mfkiwl/SDR-R/hw/SDRR/Draft1.asc

C1: cap; 20p
Q1: npn; 2N3904
R1: res; 100k
R2: res; 500
V1: voltage; PULSE(0 5 1u 1n 1n 1u 2u 10)
V2: voltage; 5
Named nets: 0
.tran 0 10u 0 10p
