mfkiwl/SDR-R/fpga-src/sources_1/imports/SDR-R/fpga-src/USB_Block/vhdl/ft245_sync_if.vhd

-----------------------------------------------------------------------------
-- file			: ft245_sync_if.vhd
--
-- brief		: Interface for FTDI ft2232h in ft245 synchronous mode
-- author(s)	: marc at pignat dot org
-----------------------------------------------------------------------------
-- Copyright 2015-2019 Marc Pignat
--
-- Licensed under the Apache License, Version 2.0 (the "License");
-- you may not use this file except in compliance with the License.
-- You may obtain a copy of the License at
--
-- 		http://www.apache.org/licenses/LICENSE-2.0
--
-- Unless required by applicable law or agreed to in writing, software
-- distributed under the License is distributed on an "AS IS" BASIS,
-- See the License for the specific language governing permissions and
-- limitations under the License.
-----------------------------------------------------------------------------
--
-- FIXME	: loose bytes when using ftdi_set_latency_timer(ftdi, 1), so
--			  use ftdi_set_latency_timer(ftdi, 2).
--
-----------------------------------------------------------------------------
--
-- Usage
--
-- * This block MUST be clocked by the FTDI chip
--
-- * FTDI Signals MUST be connected directly and tied into the IO pads.
--   * For Xilinx FPGA, nothing has to be done since the "iob" attribute is set.
--
-- * Host code at https://github.com/RandomReaper/ft2tcp
-----------------------------------------------------------------------------
--
-- * FPGA -> FTDI
--   Sending data to the FTDI chip is done using in_* signals.
--   Example: Sending 2 bytes:
--             ____     ____        ____     ____     ____     ____
--   clock ___/    \___/    \/\/\/\/    \___/    \___/    \___/    \____
--
--                ____t1                           t4__________________
--   in_empty (in)    \____________________________/
--
--                                t2________________
--   in_read (out)  _______________|                \__________________
--
--                                        t3
--   in_data (in)  -------------------------< D0    >< D1    >---------
--
--   At t1, in_empty is set to '0'.
--
--   At t2, (after an unknown number of clock cycles) the ft245_sync_if is
--          ready for sendind data and set in_read to '1'.
--
--   At t3, (one clock after in_read) The data (D0) is on in_data.
--
--   At t4, in_data contains the last data, in_empty is set '0'. The
--          ft245_sync_if sets in_read to '0' at the same time.
--
--   Note : This burst can be interrupted (in_read will go to '0', when the
--          FTDI chip FIFO is full.
--
-----------------------------------------------------------------------------
--
-- * FTDI -> FPGA
--   Receiving data from the FTDI chip is done using out_* signals.
--   Example: Receiving 2 bytes:
--             ____     ____        ____     ____     ____     ____
--   clock ___/    \___/    \/\/\/\/    \___/    \___/    \___/    \____
--
--                ____t1                            __________________
--   out_full (in)    \____________________________/___________________
--
--                                t2________________t4
--   out_valid (out)  _____________|                \__________________
--
--                                          t3
--   out_data (out)  --------------< D0    >< D1    >---------
--
--   At t1, the out_full is set to '0'.
--
--   At t2, (after an unknown number of clock cycles) and when the FTDI chip has
--          received data the ft245_sync_if set out_valid to '1' and set data
--          on data out.
--
--   At t3, There is a new data on every clock on out_data
--
--   At t4, out_valid goes '0' (no more data).
--
--   Note : Data receive can be interrupted at any time by setting out_full to
--          '1' at any time.
--
-----------------------------------------------------------------------------

library ieee;
	use ieee.std_logic_1164.all;
	use ieee.numeric_std.all;

entity ft245_sync_if is
port
(
	-----------------------------------------------------
	-- Interface to the ftdi chip
	-----------------------------------------------------
	adbus			: inout	std_logic_vector(7 downto 0);
	rxf_n			: in	std_ulogic;
	txe_n			: in	std_ulogic;
	rd_n			: out	std_ulogic := '1';
	wr_n			: out	std_ulogic := '1';
	clock			: in	std_ulogic;
	oe_n			: out	std_ulogic := '1';
	siwu			: out	std_ulogic;
	reset_n			: out	std_ulogic;
	suspend_n		: in	std_ulogic;

	-----------------------------------------------------
	-- Interface to the internal logic
	-----------------------------------------------------
	reset			: in	std_ulogic;

	-- FPGA -> FTDI
	in_data			: in	std_ulogic_vector(7 downto 0);
	in_empty		: in	std_ulogic;
	in_read			: out	std_ulogic;

	-- FTDI -> FPGA
	out_data		: out	std_ulogic_vector(7 downto 0);
	out_valid		: out	std_ulogic;
	out_full		: in	std_ulogic
	
	--debug
	--debug_out          : out std_logic_vector( 10 downto 0)
);

	-- Force signals into IO pads
	-- Warning XST specific syntax
	attribute iob				: string;
	attribute iob of rxf_n		: signal is "TRUE";
	attribute iob of txe_n		: signal is "TRUE";
	attribute iob of rd_n		: signal is "TRUE";
	attribute iob of wr_n		: signal is "TRUE";
	attribute iob of oe_n		: signal is "TRUE";
	attribute iob of siwu		: signal is "TRUE";
	attribute iob of reset_n	: signal is "TRUE";
	attribute iob of suspend_n	: signal is "TRUE";

end ft245_sync_if;

architecture rtl of ft245_sync_if is

	type state_e is
	(
		STATE_RESET,
		STATE_IDLE,
		STATE_WAIT_READ1,
		STATE_WAIT_READ2,
		STATE_READ,
		STATE_READ_OLD,
		STATE_AFTER_READ1,
		STATE_AFTER_READ2,
		STATE_WRITE,
		STATE_WRITE_OLD
	);

	-- State
	signal state			: state_e := STATE_RESET;
	signal next_state		: state_e;

	-- Positive versions of ft245 control signals
	signal ft_oe			: std_ulogic;
	signal ft_write			: std_ulogic;
	signal ft_read			: std_ulogic;
	signal ft_suspend		: std_ulogic := '0';
	signal ft_tx			: std_ulogic := '0';
	signal ft_rx			: std_ulogic := '0';
    
    --debug signals
    signal bug0, bug1, bug2, bug3, bug4, bug5, bug6, bug7, bug8, bug9 : std_logic;

	-- Store missed read/write
	type failed_element_t is
	record
		data	: std_ulogic_vector(in_data'range);
		valid	: std_ulogic;
	end record;

	type failed_t is array(integer range <>) of failed_element_t;

	-- Data RX
	signal out_data_old		: failed_t(1 downto 0) :=
		(others => (data => (others => '-'), valid => '0'));
	signal read_failed		: std_ulogic;
	signal oe				: std_ulogic;
	signal adbus_int		: std_ulogic_vector(in_data'range);
	signal ft_read_old		: std_ulogic_vector(1 downto 0) := (others => '0');
	signal out_data_int		: std_ulogic_vector(in_data'range) := (others => '0');
	signal out_valid_int	: std_ulogic;

	-- Data TX
	signal in_data_old		: failed_t(2 downto 0) :=
		(others => (data => (others => '-'), valid => '0'));
	signal ft_write_old		: std_ulogic_vector(1 downto 0)  := (others => '0');
	signal write_failed		: std_ulogic := '0';
	signal old_counter		: unsigned(1 downto 0) := (others => '0');
	signal in_read_int		: std_ulogic;
	signal in_read_old		: std_ulogic := '0';

	-- Force signals into IO pads
	-- Warning XST specific syntax
	attribute iob of adbus_int		: signal is "TRUE";
	attribute iob of ft_rx			: signal is "TRUE";
	attribute iob of ft_tx			: signal is "TRUE";
	attribute iob of ft_suspend		: signal is "TRUE";

begin

-----------------------------------------------------------------------------
-- Ports
-----------------------------------------------------------------------------

-- When the ft2232h is resest, it will exit the synchronous fifo mode
reset_n <= '1';

-- Unused output
siwu <= '1';

-- Tristate
adbus <= std_logic_vector(adbus_int) when oe = '1' else (others => 'Z');

-- Synchronize input signals
in_sync: process(reset, clock)
begin
	if reset = '1' then
		out_data_int	<= (others => '0');
		ft_tx			<= '0';
		ft_rx			<= '0';
		ft_suspend		<= '0';
	elsif rising_edge(clock) then
		out_data_int	<= std_ulogic_vector(adbus);
		ft_tx			<= not txe_n;
		ft_rx			<= not rxf_n;
		ft_suspend		<= not suspend_n;
		end if;
end process;

-- Synchronize output signals
out_sync: process(reset, clock)
begin
	if reset = '1' then
		adbus_int	<= (others => '0');
		rd_n			<= '1';
		wr_n			<= '1';
		oe_n			<= '1';
	elsif rising_edge(clock) then
		adbus_int		<= in_data;
		rd_n			<= not ft_read;
		wr_n			<= not ft_write;
		oe_n			<= not ft_oe;
		if state = STATE_WRITE_OLD then
			adbus_int <= in_data_old(in_data_old'left).data;
		end if;
	end if;
end process;

--debug process
--debug_sync: process(clock)
--begin
--    if rising_edge(clock) then
--        debug_out(0) <= bug0;
--        debug_out(1) <= bug1;
--        debug_out(2) <= bug2;
--        debug_out(3) <= bug3;
--        debug_out(4) <= bug4;
--        debug_out(5) <= bug5;
--        debug_out(6) <= bug6;
--        debug_out(7) <= bug7;
--        debug_out(8) <= bug8;
--        debug_out(9) <= bug9;
--    end if;
--end process; 

-----------------------------------------------------------------------------
-- State machine
-----------------------------------------------------------------------------

state_machine: process(reset, clock)
begin
	if reset = '1' then
		state <= STATE_RESET;
	elsif rising_edge(clock) then
		state <= next_state;
	end if;
end process;

state_machine_next: process(state, in_empty, ft_rx, ft_tx, write_failed, ft_write, old_counter, out_full, read_failed)
begin
	next_state <= state;

	case state is
		when STATE_RESET =>
			next_state <= STATE_IDLE;
		when STATE_IDLE =>
			if in_empty = '0' and ft_tx = '1' then
				next_state <= STATE_WRITE;
			end if;

			if write_failed = '1' and ft_tx = '1' then
				next_state <= STATE_WRITE_OLD;
			end if;

			if ft_rx = '1' and out_full = '0' then
				next_state <= STATE_WAIT_READ1;
			end if;

			if read_failed = '1' and out_full = '0' then
				next_state <= STATE_READ_OLD;
			end if;

		when STATE_WAIT_READ1 =>
			next_state <= STATE_WAIT_READ2;

		when STATE_WAIT_READ2 =>
			next_state <= STATE_READ;

		when STATE_READ =>
			if ft_rx = '0' or out_full = '1' then
				next_state <= STATE_AFTER_READ1;
			end if;

		when STATE_AFTER_READ1 =>
			next_state <= STATE_AFTER_READ2;
		when STATE_AFTER_READ2 =>
			next_state <= STATE_IDLE;

		when STATE_WRITE =>
			if ft_tx = '1' and in_empty = '0' then
				next_state <= STATE_WRITE;
			else
				next_state <= STATE_IDLE;
			end if;

		when STATE_WRITE_OLD =>
			if old_counter = in_data_old'left then
				next_state <= STATE_IDLE;
			end if;

		when STATE_READ_OLD =>
			if out_full = '1' or read_failed = '0' then
				next_state <= STATE_IDLE;
			end if;

	end case;
end process;


-- ft_oe and oe are not driven simultaneously to avoid bus contention.
with state select ft_oe <=
		'1' when STATE_WAIT_READ1 | STATE_WAIT_READ2 | STATE_READ,
		'0' when others;

with state select oe <=
		'0' when STATE_WAIT_READ1 | STATE_WAIT_READ2 | STATE_READ | STATE_AFTER_READ1 | STATE_AFTER_READ2,
		'1' when others;

with state select ft_read <=
		not out_full when STATE_WAIT_READ2 | STATE_READ,
		'0' when others;

with state select ft_write <=
		ft_tx when STATE_WRITE,
		in_data_old(in_data_old'left).valid when STATE_WRITE_OLD,
		'0' when others;

in_read <= in_read_int;
with next_state select in_read_int <=
		ft_tx when STATE_WRITE,
		'0' when others;

---Debug case states
with state select bug0 <=
    '1' when STATE_RESET, --pin 39
    '0' when others;
with state select bug1 <=
    '1' when STATE_IDLE, --pin 40
    '0' when others;
with state select bug2 <=
    '1' when STATE_WAIT_READ1, --pin 41
    '0' when others;
with state select bug3 <=
    '1' when STATE_WAIT_READ2, --pin 42
    '0' when others;
with state select bug4 <=
    '1' when STATE_READ,  --pin 43
    '0' when others;
with state select bug5 <=
    '1' when STATE_READ_OLD, --pin 44
    '0' when others;
with state select bug6 <=
    '1' when STATE_AFTER_READ1, -- pin 45
    '0' when others;
with state select bug7 <=
    '1' when STATE_AFTER_READ2, -- pin 46
    '0' when others;
with state select bug8 <=
    '1' when STATE_WRITE, ---pin 47
    '0' when others;
with state select bug9 <=
    '1' when STATE_WRITE_OLD, --pin 48
    '0' when others;
-----------------------------------------------------------------------------
-- RX data
-----------------------------------------------------------------------------

old_rx: process(reset, clock)
begin
	if reset = '1' then
		for i in ft_read_old'range loop
			ft_read_old(i) <= '0';
		end loop;
	elsif rising_edge(clock) then
		for i in ft_read_old'left downto 1 loop
			ft_read_old(i) <= ft_read_old(i-1);
		end loop;
		ft_read_old(0)	<= ft_read;
	end if;
end process;

read_failed_proc: process(out_data_old)
begin
	read_failed <= '0';
	for i in out_data_old'range loop
		if out_data_old(i).valid = '1' then
			read_failed <= '1';
		end if;
	end loop;
end process;

out_data_old_proc: process(reset, clock)
begin
	if reset = '1' then
		for i in out_data_old'range loop
			out_data_old(i).data <= (others => '0');
			out_data_old(i).valid <= '0';
		end loop;
	elsif rising_edge(clock) then
		if (ft_read_old(1) and ft_rx) = '1' or state = STATE_READ_OLD then
			for i in out_data_old'left downto 1 loop
				out_data_old(i) <= out_data_old(i-1);
			end loop;
			out_data_old(0).data	<= out_data_int;
			out_data_old(0).valid	<= ft_read_old(1) and ft_rx;
		end if;
	end if;
end process;

out_valid <= out_valid_int;
with state select out_valid_int <=
	ft_read_old(1) and ft_rx and not out_full when STATE_READ,
	out_data_old(out_data_old'left).valid and not out_full when STATE_READ_OLD,
	'0' when others;

out_data_proc: process(state, out_data_old, out_data_int, out_valid_int)
begin
	out_data <= out_data_int;

	if state = STATE_READ_OLD then
		out_data <= out_data_old(out_data_old'left).data;
	end if;

	--pragma synthesis_off
	if out_valid_int = '0' then
		out_data <= (others => '-');
	end if;
	--pragma synthesis_on

end process;

-----------------------------------------------------------------------------
-- TX data
-----------------------------------------------------------------------------
----reset stuff Or something for old tx/ writing?
old_tx: process(reset, clock)
begin
	if reset = '1' then
		for i in ft_write_old'range loop
			ft_write_old(i) <= '0';
		end loop;
	elsif rising_edge(clock) then
		for i in ft_write_old'left downto 1 loop
			ft_write_old(i) <= ft_write_old(i-1);
		end loop;
		ft_write_old(0)	<= ft_write;
	end if;
end process;

--something for reset
in_read_old_proc: process(reset, clock)
begin
	if reset = '1' then
		in_read_old			<= '0';
	elsif rising_edge(clock) then
		in_read_old			<= in_read_int;
	end if;
end process;

--looks like this is a process is for write failures
process(reset, clock)
begin
	if reset = '1' then
		for i in in_data_old'range loop
			in_data_old(i).data	 <= (others => '0');
			in_data_old(i).valid <= '0';

			--pragma synthesis_off
			in_data_old(i).data <= (others => '-');
			--pragma synthesis_on

		end loop;

		old_counter <= (others => '0');
		write_failed<= '0';
	elsif rising_edge(clock) then
		if write_failed = '0' then
			for i in in_data_old'left downto 1 loop
				in_data_old(i)		<= in_data_old(i-1);
			end loop;
			in_data_old(0).data		<= in_data;
			in_data_old(0).valid	<= in_read_old;

		end if;

		if ft_write_old(1) = '1' and ft_tx = '0' then
			write_failed <= '1';
		end if;

		if state = STATE_WRITE_OLD then
			old_counter <= old_counter + 1;
			for i in in_data_old'left downto 1 loop
				in_data_old(i) <= in_data_old(i-1);
			end loop;

			in_data_old(0).valid <= '0';

			--pragma synthesis_off
			in_data_old(0).data <= (others => '-');
			--pragma synthesis_on

			if next_state = STATE_IDLE then
				old_counter <= (others => '0');
				write_failed <= '0';
			end if;
		end if;
	end if;
end process;

end architecture;
