mfkiwl/SDR-R/fpga-src/sources_1/ip/FPGAtoFTDI_fifo/FPGAtoFTDI_fifo_stub.v

// Copyright 1986-2018 Xilinx, Inc. All Rights Reserved.
// --------------------------------------------------------------------------------
// Tool Version: Vivado v.2018.2.2 (win64) Build 2348494 Mon Oct  1 18:25:44 MDT 2018
// Date        : Thu May 16 00:08:55 2019
// Host        : DESKTOP-4O36AQC running 64-bit major release  (build 9200)
// Command     : write_verilog -force -mode synth_stub
//               C:/Users/Guy/Desktop/UMBC/2019_Spring/451/SDRR_FINAL/SDRR_FINAL.srcs/sources_1/ip/FPGAtoFTDI_fifo/FPGAtoFTDI_fifo_stub.v
// Design      : FPGAtoFTDI_fifo
// Purpose     : Stub declaration of top-level module interface
// Device      : xc7a15tcpg236-1
// --------------------------------------------------------------------------------

// This empty module with port declaration file causes synthesis tools to infer a black box for IP.
// The synthesis directives are for Synopsys Synplify support to prevent IO buffer insertion.
// Please paste the declaration into a Verilog source file or add the file as an additional source.
(* x_core_info = "fifo_generator_v13_2_2,Vivado 2018.2.2" *)
module FPGAtoFTDI_fifo(rst, wr_clk, rd_clk, din, wr_en, rd_en, dout, full, 
  empty)
/* synthesis syn_black_box black_box_pad_pin="rst,wr_clk,rd_clk,din[15:0],wr_en,rd_en,dout[7:0],full,empty" */;
  input rst;
  input wr_clk;
  input rd_clk;
  input [15:0]din;
  input wr_en;
  input rd_en;
  output [7:0]dout;
  output full;
  output empty;
endmodule
