mfkiwl/SDR-R/fpga-src/sources_1/ip/FPGAtoFTDI_fifo/FPGAtoFTDI_fifo_sim_netlist.v

// Copyright 1986-2018 Xilinx, Inc. All Rights Reserved.
// --------------------------------------------------------------------------------
// Tool Version: Vivado v.2018.2.2 (win64) Build 2348494 Mon Oct  1 18:25:44 MDT 2018
// Date        : Thu May 16 00:08:55 2019
// Host        : DESKTOP-4O36AQC running 64-bit major release  (build 9200)
// Command     : write_verilog -force -mode funcsim
//               C:/Users/Guy/Desktop/UMBC/2019_Spring/451/SDRR_FINAL/SDRR_FINAL.srcs/sources_1/ip/FPGAtoFTDI_fifo/FPGAtoFTDI_fifo_sim_netlist.v
// Design      : FPGAtoFTDI_fifo
// Purpose     : This verilog netlist is a functional simulation representation of the design and should not be modified
//               or synthesized. This netlist cannot be used for SDF annotated simulation.
// Device      : xc7a15tcpg236-1
// --------------------------------------------------------------------------------
`timescale 1 ps / 1 ps

(* CHECK_LICENSE_TYPE = "FPGAtoFTDI_fifo,fifo_generator_v13_2_2,{}" *) (* downgradeipidentifiedwarnings = "yes" *) (* x_core_info = "fifo_generator_v13_2_2,Vivado 2018.2.2" *) 
(* NotValidForBitStream *)
module FPGAtoFTDI_fifo
   (rst,
    wr_clk,
    rd_clk,
    din,
    wr_en,
    rd_en,
    dout,
    full,
    empty);
  input rst;
  (* x_interface_info = "xilinx.com:signal:clock:1.0 write_clk CLK" *) (* x_interface_parameter = "XIL_INTERFACENAME write_clk, FREQ_HZ 100000000, PHASE 0.000" *) input wr_clk;
  (* x_interface_info = "xilinx.com:signal:clock:1.0 read_clk CLK" *) (* x_interface_parameter = "XIL_INTERFACENAME read_clk, FREQ_HZ 100000000, PHASE 0.000" *) input rd_clk;
  (* x_interface_info = "xilinx.com:interface:fifo_write:1.0 FIFO_WRITE WR_DATA" *) input [15:0]din;
  (* x_interface_info = "xilinx.com:interface:fifo_write:1.0 FIFO_WRITE WR_EN" *) input wr_en;
  (* x_interface_info = "xilinx.com:interface:fifo_read:1.0 FIFO_READ RD_EN" *) input rd_en;
  (* x_interface_info = "xilinx.com:interface:fifo_read:1.0 FIFO_READ RD_DATA" *) output [7:0]dout;
  (* x_interface_info = "xilinx.com:interface:fifo_write:1.0 FIFO_WRITE FULL" *) output full;
  (* x_interface_info = "xilinx.com:interface:fifo_read:1.0 FIFO_READ EMPTY" *) output empty;

  wire [15:0]din;
  wire [7:0]dout;
  wire empty;
  wire full;
  wire rd_clk;
  wire rd_en;
  wire rst;
  wire wr_clk;
  wire wr_en;
  wire NLW_U0_almost_empty_UNCONNECTED;
  wire NLW_U0_almost_full_UNCONNECTED;
  wire NLW_U0_axi_ar_dbiterr_UNCONNECTED;
  wire NLW_U0_axi_ar_overflow_UNCONNECTED;
  wire NLW_U0_axi_ar_prog_empty_UNCONNECTED;
  wire NLW_U0_axi_ar_prog_full_UNCONNECTED;
  wire NLW_U0_axi_ar_sbiterr_UNCONNECTED;
  wire NLW_U0_axi_ar_underflow_UNCONNECTED;
  wire NLW_U0_axi_aw_dbiterr_UNCONNECTED;
  wire NLW_U0_axi_aw_overflow_UNCONNECTED;
  wire NLW_U0_axi_aw_prog_empty_UNCONNECTED;
  wire NLW_U0_axi_aw_prog_full_UNCONNECTED;
  wire NLW_U0_axi_aw_sbiterr_UNCONNECTED;
  wire NLW_U0_axi_aw_underflow_UNCONNECTED;
  wire NLW_U0_axi_b_dbiterr_UNCONNECTED;
  wire NLW_U0_axi_b_overflow_UNCONNECTED;
  wire NLW_U0_axi_b_prog_empty_UNCONNECTED;
  wire NLW_U0_axi_b_prog_full_UNCONNECTED;
  wire NLW_U0_axi_b_sbiterr_UNCONNECTED;
  wire NLW_U0_axi_b_underflow_UNCONNECTED;
  wire NLW_U0_axi_r_dbiterr_UNCONNECTED;
  wire NLW_U0_axi_r_overflow_UNCONNECTED;
  wire NLW_U0_axi_r_prog_empty_UNCONNECTED;
  wire NLW_U0_axi_r_prog_full_UNCONNECTED;
  wire NLW_U0_axi_r_sbiterr_UNCONNECTED;
  wire NLW_U0_axi_r_underflow_UNCONNECTED;
  wire NLW_U0_axi_w_dbiterr_UNCONNECTED;
  wire NLW_U0_axi_w_overflow_UNCONNECTED;
  wire NLW_U0_axi_w_prog_empty_UNCONNECTED;
  wire NLW_U0_axi_w_prog_full_UNCONNECTED;
  wire NLW_U0_axi_w_sbiterr_UNCONNECTED;
  wire NLW_U0_axi_w_underflow_UNCONNECTED;
  wire NLW_U0_axis_dbiterr_UNCONNECTED;
  wire NLW_U0_axis_overflow_UNCONNECTED;
  wire NLW_U0_axis_prog_empty_UNCONNECTED;
  wire NLW_U0_axis_prog_full_UNCONNECTED;
  wire NLW_U0_axis_sbiterr_UNCONNECTED;
  wire NLW_U0_axis_underflow_UNCONNECTED;
  wire NLW_U0_dbiterr_UNCONNECTED;
  wire NLW_U0_m_axi_arvalid_UNCONNECTED;
  wire NLW_U0_m_axi_awvalid_UNCONNECTED;
  wire NLW_U0_m_axi_bready_UNCONNECTED;
  wire NLW_U0_m_axi_rready_UNCONNECTED;
  wire NLW_U0_m_axi_wlast_UNCONNECTED;
  wire NLW_U0_m_axi_wvalid_UNCONNECTED;
  wire NLW_U0_m_axis_tlast_UNCONNECTED;
  wire NLW_U0_m_axis_tvalid_UNCONNECTED;
  wire NLW_U0_overflow_UNCONNECTED;
  wire NLW_U0_prog_empty_UNCONNECTED;
  wire NLW_U0_prog_full_UNCONNECTED;
  wire NLW_U0_rd_rst_busy_UNCONNECTED;
  wire NLW_U0_s_axi_arready_UNCONNECTED;
  wire NLW_U0_s_axi_awready_UNCONNECTED;
  wire NLW_U0_s_axi_bvalid_UNCONNECTED;
  wire NLW_U0_s_axi_rlast_UNCONNECTED;
  wire NLW_U0_s_axi_rvalid_UNCONNECTED;
  wire NLW_U0_s_axi_wready_UNCONNECTED;
  wire NLW_U0_s_axis_tready_UNCONNECTED;
  wire NLW_U0_sbiterr_UNCONNECTED;
  wire NLW_U0_underflow_UNCONNECTED;
  wire NLW_U0_valid_UNCONNECTED;
  wire NLW_U0_wr_ack_UNCONNECTED;
  wire NLW_U0_wr_rst_busy_UNCONNECTED;
  wire [4:0]NLW_U0_axi_ar_data_count_UNCONNECTED;
  wire [4:0]NLW_U0_axi_ar_rd_data_count_UNCONNECTED;
  wire [4:0]NLW_U0_axi_ar_wr_data_count_UNCONNECTED;
  wire [4:0]NLW_U0_axi_aw_data_count_UNCONNECTED;
  wire [4:0]NLW_U0_axi_aw_rd_data_count_UNCONNECTED;
  wire [4:0]NLW_U0_axi_aw_wr_data_count_UNCONNECTED;
  wire [4:0]NLW_U0_axi_b_data_count_UNCONNECTED;
  wire [4:0]NLW_U0_axi_b_rd_data_count_UNCONNECTED;
  wire [4:0]NLW_U0_axi_b_wr_data_count_UNCONNECTED;
  wire [10:0]NLW_U0_axi_r_data_count_UNCONNECTED;
  wire [10:0]NLW_U0_axi_r_rd_data_count_UNCONNECTED;
  wire [10:0]NLW_U0_axi_r_wr_data_count_UNCONNECTED;
  wire [10:0]NLW_U0_axi_w_data_count_UNCONNECTED;
  wire [10:0]NLW_U0_axi_w_rd_data_count_UNCONNECTED;
  wire [10:0]NLW_U0_axi_w_wr_data_count_UNCONNECTED;
  wire [10:0]NLW_U0_axis_data_count_UNCONNECTED;
  wire [10:0]NLW_U0_axis_rd_data_count_UNCONNECTED;
  wire [10:0]NLW_U0_axis_wr_data_count_UNCONNECTED;
  wire [9:0]NLW_U0_data_count_UNCONNECTED;
  wire [31:0]NLW_U0_m_axi_araddr_UNCONNECTED;
  wire [1:0]NLW_U0_m_axi_arburst_UNCONNECTED;
  wire [3:0]NLW_U0_m_axi_arcache_UNCONNECTED;
  wire [0:0]NLW_U0_m_axi_arid_UNCONNECTED;
  wire [7:0]NLW_U0_m_axi_arlen_UNCONNECTED;
  wire [0:0]NLW_U0_m_axi_arlock_UNCONNECTED;
  wire [2:0]NLW_U0_m_axi_arprot_UNCONNECTED;
  wire [3:0]NLW_U0_m_axi_arqos_UNCONNECTED;
  wire [3:0]NLW_U0_m_axi_arregion_UNCONNECTED;
  wire [2:0]NLW_U0_m_axi_arsize_UNCONNECTED;
  wire [0:0]NLW_U0_m_axi_aruser_UNCONNECTED;
  wire [31:0]NLW_U0_m_axi_awaddr_UNCONNECTED;
  wire [1:0]NLW_U0_m_axi_awburst_UNCONNECTED;
  wire [3:0]NLW_U0_m_axi_awcache_UNCONNECTED;
  wire [0:0]NLW_U0_m_axi_awid_UNCONNECTED;
  wire [7:0]NLW_U0_m_axi_awlen_UNCONNECTED;
  wire [0:0]NLW_U0_m_axi_awlock_UNCONNECTED;
  wire [2:0]NLW_U0_m_axi_awprot_UNCONNECTED;
  wire [3:0]NLW_U0_m_axi_awqos_UNCONNECTED;
  wire [3:0]NLW_U0_m_axi_awregion_UNCONNECTED;
  wire [2:0]NLW_U0_m_axi_awsize_UNCONNECTED;
  wire [0:0]NLW_U0_m_axi_awuser_UNCONNECTED;
  wire [63:0]NLW_U0_m_axi_wdata_UNCONNECTED;
  wire [0:0]NLW_U0_m_axi_wid_UNCONNECTED;
  wire [7:0]NLW_U0_m_axi_wstrb_UNCONNECTED;
  wire [0:0]NLW_U0_m_axi_wuser_UNCONNECTED;
  wire [7:0]NLW_U0_m_axis_tdata_UNCONNECTED;
  wire [0:0]NLW_U0_m_axis_tdest_UNCONNECTED;
  wire [0:0]NLW_U0_m_axis_tid_UNCONNECTED;
  wire [0:0]NLW_U0_m_axis_tkeep_UNCONNECTED;
  wire [0:0]NLW_U0_m_axis_tstrb_UNCONNECTED;
  wire [3:0]NLW_U0_m_axis_tuser_UNCONNECTED;
  wire [10:0]NLW_U0_rd_data_count_UNCONNECTED;
  wire [0:0]NLW_U0_s_axi_bid_UNCONNECTED;
  wire [1:0]NLW_U0_s_axi_bresp_UNCONNECTED;
  wire [0:0]NLW_U0_s_axi_buser_UNCONNECTED;
  wire [63:0]NLW_U0_s_axi_rdata_UNCONNECTED;
  wire [0:0]NLW_U0_s_axi_rid_UNCONNECTED;
  wire [1:0]NLW_U0_s_axi_rresp_UNCONNECTED;
  wire [0:0]NLW_U0_s_axi_ruser_UNCONNECTED;
  wire [9:0]NLW_U0_wr_data_count_UNCONNECTED;

  (* C_ADD_NGC_CONSTRAINT = "0" *) 
  (* C_APPLICATION_TYPE_AXIS = "0" *) 
  (* C_APPLICATION_TYPE_RACH = "0" *) 
  (* C_APPLICATION_TYPE_RDCH = "0" *) 
  (* C_APPLICATION_TYPE_WACH = "0" *) 
  (* C_APPLICATION_TYPE_WDCH = "0" *) 
  (* C_APPLICATION_TYPE_WRCH = "0" *) 
  (* C_AXIS_TDATA_WIDTH = "8" *) 
  (* C_AXIS_TDEST_WIDTH = "1" *) 
  (* C_AXIS_TID_WIDTH = "1" *) 
  (* C_AXIS_TKEEP_WIDTH = "1" *) 
  (* C_AXIS_TSTRB_WIDTH = "1" *) 
  (* C_AXIS_TUSER_WIDTH = "4" *) 
  (* C_AXIS_TYPE = "0" *) 
  (* C_AXI_ADDR_WIDTH = "32" *) 
  (* C_AXI_ARUSER_WIDTH = "1" *) 
  (* C_AXI_AWUSER_WIDTH = "1" *) 
  (* C_AXI_BUSER_WIDTH = "1" *) 
  (* C_AXI_DATA_WIDTH = "64" *) 
  (* C_AXI_ID_WIDTH = "1" *) 
  (* C_AXI_LEN_WIDTH = "8" *) 
  (* C_AXI_LOCK_WIDTH = "1" *) 
  (* C_AXI_RUSER_WIDTH = "1" *) 
  (* C_AXI_TYPE = "1" *) 
  (* C_AXI_WUSER_WIDTH = "1" *) 
  (* C_COMMON_CLOCK = "0" *) 
  (* C_COUNT_TYPE = "0" *) 
  (* C_DATA_COUNT_WIDTH = "10" *) 
  (* C_DEFAULT_VALUE = "BlankString" *) 
  (* C_DIN_WIDTH = "16" *) 
  (* C_DIN_WIDTH_AXIS = "1" *) 
  (* C_DIN_WIDTH_RACH = "32" *) 
  (* C_DIN_WIDTH_RDCH = "64" *) 
  (* C_DIN_WIDTH_WACH = "1" *) 
  (* C_DIN_WIDTH_WDCH = "64" *) 
  (* C_DIN_WIDTH_WRCH = "2" *) 
  (* C_DOUT_RST_VAL = "0" *) 
  (* C_DOUT_WIDTH = "8" *) 
  (* C_ENABLE_RLOCS = "0" *) 
  (* C_ENABLE_RST_SYNC = "1" *) 
  (* C_EN_SAFETY_CKT = "0" *) 
  (* C_ERROR_INJECTION_TYPE = "0" *) 
  (* C_ERROR_INJECTION_TYPE_AXIS = "0" *) 
  (* C_ERROR_INJECTION_TYPE_RACH = "0" *) 
  (* C_ERROR_INJECTION_TYPE_RDCH = "0" *) 
  (* C_ERROR_INJECTION_TYPE_WACH = "0" *) 
  (* C_ERROR_INJECTION_TYPE_WDCH = "0" *) 
  (* C_ERROR_INJECTION_TYPE_WRCH = "0" *) 
  (* C_FAMILY = "artix7" *) 
  (* C_FULL_FLAGS_RST_VAL = "1" *) 
  (* C_HAS_ALMOST_EMPTY = "0" *) 
  (* C_HAS_ALMOST_FULL = "0" *) 
  (* C_HAS_AXIS_TDATA = "1" *) 
  (* C_HAS_AXIS_TDEST = "0" *) 
  (* C_HAS_AXIS_TID = "0" *) 
  (* C_HAS_AXIS_TKEEP = "0" *) 
  (* C_HAS_AXIS_TLAST = "0" *) 
  (* C_HAS_AXIS_TREADY = "1" *) 
  (* C_HAS_AXIS_TSTRB = "0" *) 
  (* C_HAS_AXIS_TUSER = "1" *) 
  (* C_HAS_AXI_ARUSER = "0" *) 
  (* C_HAS_AXI_AWUSER = "0" *) 
  (* C_HAS_AXI_BUSER = "0" *) 
  (* C_HAS_AXI_ID = "0" *) 
  (* C_HAS_AXI_RD_CHANNEL = "1" *) 
  (* C_HAS_AXI_RUSER = "0" *) 
  (* C_HAS_AXI_WR_CHANNEL = "1" *) 
  (* C_HAS_AXI_WUSER = "0" *) 
  (* C_HAS_BACKUP = "0" *) 
  (* C_HAS_DATA_COUNT = "0" *) 
  (* C_HAS_DATA_COUNTS_AXIS = "0" *) 
  (* C_HAS_DATA_COUNTS_RACH = "0" *) 
  (* C_HAS_DATA_COUNTS_RDCH = "0" *) 
  (* C_HAS_DATA_COUNTS_WACH = "0" *) 
  (* C_HAS_DATA_COUNTS_WDCH = "0" *) 
  (* C_HAS_DATA_COUNTS_WRCH = "0" *) 
  (* C_HAS_INT_CLK = "0" *) 
  (* C_HAS_MASTER_CE = "0" *) 
  (* C_HAS_MEMINIT_FILE = "0" *) 
  (* C_HAS_OVERFLOW = "0" *) 
  (* C_HAS_PROG_FLAGS_AXIS = "0" *) 
  (* C_HAS_PROG_FLAGS_RACH = "0" *) 
  (* C_HAS_PROG_FLAGS_RDCH = "0" *) 
  (* C_HAS_PROG_FLAGS_WACH = "0" *) 
  (* C_HAS_PROG_FLAGS_WDCH = "0" *) 
  (* C_HAS_PROG_FLAGS_WRCH = "0" *) 
  (* C_HAS_RD_DATA_COUNT = "0" *) 
  (* C_HAS_RD_RST = "0" *) 
  (* C_HAS_RST = "1" *) 
  (* C_HAS_SLAVE_CE = "0" *) 
  (* C_HAS_SRST = "0" *) 
  (* C_HAS_UNDERFLOW = "0" *) 
  (* C_HAS_VALID = "0" *) 
  (* C_HAS_WR_ACK = "0" *) 
  (* C_HAS_WR_DATA_COUNT = "0" *) 
  (* C_HAS_WR_RST = "0" *) 
  (* C_IMPLEMENTATION_TYPE = "2" *) 
  (* C_IMPLEMENTATION_TYPE_AXIS = "1" *) 
  (* C_IMPLEMENTATION_TYPE_RACH = "1" *) 
  (* C_IMPLEMENTATION_TYPE_RDCH = "1" *) 
  (* C_IMPLEMENTATION_TYPE_WACH = "1" *) 
  (* C_IMPLEMENTATION_TYPE_WDCH = "1" *) 
  (* C_IMPLEMENTATION_TYPE_WRCH = "1" *) 
  (* C_INIT_WR_PNTR_VAL = "0" *) 
  (* C_INTERFACE_TYPE = "0" *) 
  (* C_MEMORY_TYPE = "1" *) 
  (* C_MIF_FILE_NAME = "BlankString" *) 
  (* C_MSGON_VAL = "1" *) 
  (* C_OPTIMIZATION_MODE = "0" *) 
  (* C_OVERFLOW_LOW = "0" *) 
  (* C_POWER_SAVING_MODE = "0" *) 
  (* C_PRELOAD_LATENCY = "1" *) 
  (* C_PRELOAD_REGS = "0" *) 
  (* C_PRIM_FIFO_TYPE = "1kx18" *) 
  (* C_PRIM_FIFO_TYPE_AXIS = "1kx18" *) 
  (* C_PRIM_FIFO_TYPE_RACH = "512x36" *) 
  (* C_PRIM_FIFO_TYPE_RDCH = "1kx36" *) 
  (* C_PRIM_FIFO_TYPE_WACH = "512x36" *) 
  (* C_PRIM_FIFO_TYPE_WDCH = "1kx36" *) 
  (* C_PRIM_FIFO_TYPE_WRCH = "512x36" *) 
  (* C_PROG_EMPTY_THRESH_ASSERT_VAL = "2" *) 
  (* C_PROG_EMPTY_THRESH_ASSERT_VAL_AXIS = "1022" *) 
  (* C_PROG_EMPTY_THRESH_ASSERT_VAL_RACH = "1022" *) 
  (* C_PROG_EMPTY_THRESH_ASSERT_VAL_RDCH = "1022" *) 
  (* C_PROG_EMPTY_THRESH_ASSERT_VAL_WACH = "1022" *) 
  (* C_PROG_EMPTY_THRESH_ASSERT_VAL_WDCH = "1022" *) 
  (* C_PROG_EMPTY_THRESH_ASSERT_VAL_WRCH = "1022" *) 
  (* C_PROG_EMPTY_THRESH_NEGATE_VAL = "3" *) 
  (* C_PROG_EMPTY_TYPE = "0" *) 
  (* C_PROG_EMPTY_TYPE_AXIS = "0" *) 
  (* C_PROG_EMPTY_TYPE_RACH = "0" *) 
  (* C_PROG_EMPTY_TYPE_RDCH = "0" *) 
  (* C_PROG_EMPTY_TYPE_WACH = "0" *) 
  (* C_PROG_EMPTY_TYPE_WDCH = "0" *) 
  (* C_PROG_EMPTY_TYPE_WRCH = "0" *) 
  (* C_PROG_FULL_THRESH_ASSERT_VAL = "1021" *) 
  (* C_PROG_FULL_THRESH_ASSERT_VAL_AXIS = "1023" *) 
  (* C_PROG_FULL_THRESH_ASSERT_VAL_RACH = "1023" *) 
  (* C_PROG_FULL_THRESH_ASSERT_VAL_RDCH = "1023" *) 
  (* C_PROG_FULL_THRESH_ASSERT_VAL_WACH = "1023" *) 
  (* C_PROG_FULL_THRESH_ASSERT_VAL_WDCH = "1023" *) 
  (* C_PROG_FULL_THRESH_ASSERT_VAL_WRCH = "1023" *) 
  (* C_PROG_FULL_THRESH_NEGATE_VAL = "1020" *) 
  (* C_PROG_FULL_TYPE = "0" *) 
  (* C_PROG_FULL_TYPE_AXIS = "0" *) 
  (* C_PROG_FULL_TYPE_RACH = "0" *) 
  (* C_PROG_FULL_TYPE_RDCH = "0" *) 
  (* C_PROG_FULL_TYPE_WACH = "0" *) 
  (* C_PROG_FULL_TYPE_WDCH = "0" *) 
  (* C_PROG_FULL_TYPE_WRCH = "0" *) 
  (* C_RACH_TYPE = "0" *) 
  (* C_RDCH_TYPE = "0" *) 
  (* C_RD_DATA_COUNT_WIDTH = "11" *) 
  (* C_RD_DEPTH = "2048" *) 
  (* C_RD_FREQ = "1" *) 
  (* C_RD_PNTR_WIDTH = "11" *) 
  (* C_REG_SLICE_MODE_AXIS = "0" *) 
  (* C_REG_SLICE_MODE_RACH = "0" *) 
  (* C_REG_SLICE_MODE_RDCH = "0" *) 
  (* C_REG_SLICE_MODE_WACH = "0" *) 
  (* C_REG_SLICE_MODE_WDCH = "0" *) 
  (* C_REG_SLICE_MODE_WRCH = "0" *) 
  (* C_SELECT_XPM = "0" *) 
  (* C_SYNCHRONIZER_STAGE = "2" *) 
  (* C_UNDERFLOW_LOW = "0" *) 
  (* C_USE_COMMON_OVERFLOW = "0" *) 
  (* C_USE_COMMON_UNDERFLOW = "0" *) 
  (* C_USE_DEFAULT_SETTINGS = "0" *) 
  (* C_USE_DOUT_RST = "1" *) 
  (* C_USE_ECC = "0" *) 
  (* C_USE_ECC_AXIS = "0" *) 
  (* C_USE_ECC_RACH = "0" *) 
  (* C_USE_ECC_RDCH = "0" *) 
  (* C_USE_ECC_WACH = "0" *) 
  (* C_USE_ECC_WDCH = "0" *) 
  (* C_USE_ECC_WRCH = "0" *) 
  (* C_USE_EMBEDDED_REG = "0" *) 
  (* C_USE_FIFO16_FLAGS = "0" *) 
  (* C_USE_FWFT_DATA_COUNT = "0" *) 
  (* C_USE_PIPELINE_REG = "0" *) 
  (* C_VALID_LOW = "0" *) 
  (* C_WACH_TYPE = "0" *) 
  (* C_WDCH_TYPE = "0" *) 
  (* C_WRCH_TYPE = "0" *) 
  (* C_WR_ACK_LOW = "0" *) 
  (* C_WR_DATA_COUNT_WIDTH = "10" *) 
  (* C_WR_DEPTH = "1024" *) 
  (* C_WR_DEPTH_AXIS = "1024" *) 
  (* C_WR_DEPTH_RACH = "16" *) 
  (* C_WR_DEPTH_RDCH = "1024" *) 
  (* C_WR_DEPTH_WACH = "16" *) 
  (* C_WR_DEPTH_WDCH = "1024" *) 
  (* C_WR_DEPTH_WRCH = "16" *) 
  (* C_WR_FREQ = "1" *) 
  (* C_WR_PNTR_WIDTH = "10" *) 
  (* C_WR_PNTR_WIDTH_AXIS = "10" *) 
  (* C_WR_PNTR_WIDTH_RACH = "4" *) 
  (* C_WR_PNTR_WIDTH_RDCH = "10" *) 
  (* C_WR_PNTR_WIDTH_WACH = "4" *) 
  (* C_WR_PNTR_WIDTH_WDCH = "10" *) 
  (* C_WR_PNTR_WIDTH_WRCH = "4" *) 
  (* C_WR_RESPONSE_LATENCY = "1" *) 
  FPGAtoFTDI_fifo_fifo_generator_v13_2_2 U0
       (.almost_empty(NLW_U0_almost_empty_UNCONNECTED),
        .almost_full(NLW_U0_almost_full_UNCONNECTED),
        .axi_ar_data_count(NLW_U0_axi_ar_data_count_UNCONNECTED[4:0]),
        .axi_ar_dbiterr(NLW_U0_axi_ar_dbiterr_UNCONNECTED),
        .axi_ar_injectdbiterr(1'b0),
        .axi_ar_injectsbiterr(1'b0),
        .axi_ar_overflow(NLW_U0_axi_ar_overflow_UNCONNECTED),
        .axi_ar_prog_empty(NLW_U0_axi_ar_prog_empty_UNCONNECTED),
        .axi_ar_prog_empty_thresh({1'b0,1'b0,1'b0,1'b0}),
        .axi_ar_prog_full(NLW_U0_axi_ar_prog_full_UNCONNECTED),
        .axi_ar_prog_full_thresh({1'b0,1'b0,1'b0,1'b0}),
        .axi_ar_rd_data_count(NLW_U0_axi_ar_rd_data_count_UNCONNECTED[4:0]),
        .axi_ar_sbiterr(NLW_U0_axi_ar_sbiterr_UNCONNECTED),
        .axi_ar_underflow(NLW_U0_axi_ar_underflow_UNCONNECTED),
        .axi_ar_wr_data_count(NLW_U0_axi_ar_wr_data_count_UNCONNECTED[4:0]),
        .axi_aw_data_count(NLW_U0_axi_aw_data_count_UNCONNECTED[4:0]),
        .axi_aw_dbiterr(NLW_U0_axi_aw_dbiterr_UNCONNECTED),
        .axi_aw_injectdbiterr(1'b0),
        .axi_aw_injectsbiterr(1'b0),
        .axi_aw_overflow(NLW_U0_axi_aw_overflow_UNCONNECTED),
        .axi_aw_prog_empty(NLW_U0_axi_aw_prog_empty_UNCONNECTED),
        .axi_aw_prog_empty_thresh({1'b0,1'b0,1'b0,1'b0}),
        .axi_aw_prog_full(NLW_U0_axi_aw_prog_full_UNCONNECTED),
        .axi_aw_prog_full_thresh({1'b0,1'b0,1'b0,1'b0}),
        .axi_aw_rd_data_count(NLW_U0_axi_aw_rd_data_count_UNCONNECTED[4:0]),
        .axi_aw_sbiterr(NLW_U0_axi_aw_sbiterr_UNCONNECTED),
        .axi_aw_underflow(NLW_U0_axi_aw_underflow_UNCONNECTED),
        .axi_aw_wr_data_count(NLW_U0_axi_aw_wr_data_count_UNCONNECTED[4:0]),
        .axi_b_data_count(NLW_U0_axi_b_data_count_UNCONNECTED[4:0]),
        .axi_b_dbiterr(NLW_U0_axi_b_dbiterr_UNCONNECTED),
        .axi_b_injectdbiterr(1'b0),
        .axi_b_injectsbiterr(1'b0),
        .axi_b_overflow(NLW_U0_axi_b_overflow_UNCONNECTED),
        .axi_b_prog_empty(NLW_U0_axi_b_prog_empty_UNCONNECTED),
        .axi_b_prog_empty_thresh({1'b0,1'b0,1'b0,1'b0}),
        .axi_b_prog_full(NLW_U0_axi_b_prog_full_UNCONNECTED),
        .axi_b_prog_full_thresh({1'b0,1'b0,1'b0,1'b0}),
        .axi_b_rd_data_count(NLW_U0_axi_b_rd_data_count_UNCONNECTED[4:0]),
        .axi_b_sbiterr(NLW_U0_axi_b_sbiterr_UNCONNECTED),
        .axi_b_underflow(NLW_U0_axi_b_underflow_UNCONNECTED),
        .axi_b_wr_data_count(NLW_U0_axi_b_wr_data_count_UNCONNECTED[4:0]),
        .axi_r_data_count(NLW_U0_axi_r_data_count_UNCONNECTED[10:0]),
        .axi_r_dbiterr(NLW_U0_axi_r_dbiterr_UNCONNECTED),
        .axi_r_injectdbiterr(1'b0),
        .axi_r_injectsbiterr(1'b0),
        .axi_r_overflow(NLW_U0_axi_r_overflow_UNCONNECTED),
        .axi_r_prog_empty(NLW_U0_axi_r_prog_empty_UNCONNECTED),
        .axi_r_prog_empty_thresh({1'b0,1'b0,1'b0,1'b0,1'b0,1'b0,1'b0,1'b0,1'b0,1'b0}),
        .axi_r_prog_full(NLW_U0_axi_r_prog_full_UNCONNECTED),
        .axi_r_prog_full_thresh({1'b0,1'b0,1'b0,1'b0,1'b0,1'b0,1'b0,1'b0,1'b0,1'b0}),
        .axi_r_rd_data_count(NLW_U0_axi_r_rd_data_count_UNCONNECTED[10:0]),
        .axi_r_sbiterr(NLW_U0_axi_r_sbiterr_UNCONNECTED),
        .axi_r_underflow(NLW_U0_axi_r_underflow_UNCONNECTED),
        .axi_r_wr_data_count(NLW_U0_axi_r_wr_data_count_UNCONNECTED[10:0]),
        .axi_w_data_count(NLW_U0_axi_w_data_count_UNCONNECTED[10:0]),
        .axi_w_dbiterr(NLW_U0_axi_w_dbiterr_UNCONNECTED),
        .axi_w_injectdbiterr(1'b0),
        .axi_w_injectsbiterr(1'b0),
        .axi_w_overflow(NLW_U0_axi_w_overflow_UNCONNECTED),
        .axi_w_prog_empty(NLW_U0_axi_w_prog_empty_UNCONNECTED),
        .axi_w_prog_empty_thresh({1'b0,1'b0,1'b0,1'b0,1'b0,1'b0,1'b0,1'b0,1'b0,1'b0}),
        .axi_w_prog_full(NLW_U0_axi_w_prog_full_UNCONNECTED),
        .axi_w_prog_full_thresh({1'b0,1'b0,1'b0,1'b0,1'b0,1'b0,1'b0,1'b0,1'b0,1'b0}),
        .axi_w_rd_data_count(NLW_U0_axi_w_rd_data_count_UNCONNECTED[10:0]),
        .axi_w_sbiterr(NLW_U0_axi_w_sbiterr_UNCONNECTED),
        .axi_w_underflow(NLW_U0_axi_w_underflow_UNCONNECTED),
        .axi_w_wr_data_count(NLW_U0_axi_w_wr_data_count_UNCONNECTED[10:0]),
        .axis_data_count(NLW_U0_axis_data_count_UNCONNECTED[10:0]),
        .axis_dbiterr(NLW_U0_axis_dbiterr_UNCONNECTED),
        .axis_injectdbiterr(1'b0),
        .axis_injectsbiterr(1'b0),
        .axis_overflow(NLW_U0_axis_overflow_UNCONNECTED),
        .axis_prog_empty(NLW_U0_axis_prog_empty_UNCONNECTED),
        .axis_prog_empty_thresh({1'b0,1'b0,1'b0,1'b0,1'b0,1'b0,1'b0,1'b0,1'b0,1'b0}),
        .axis_prog_full(NLW_U0_axis_prog_full_UNCONNECTED),
        .axis_prog_full_thresh({1'b0,1'b0,1'b0,1'b0,1'b0,1'b0,1'b0,1'b0,1'b0,1'b0}),
        .axis_rd_data_count(NLW_U0_axis_rd_data_count_UNCONNECTED[10:0]),
        .axis_sbiterr(NLW_U0_axis_sbiterr_UNCONNECTED),
        .axis_underflow(NLW_U0_axis_underflow_UNCONNECTED),
        .axis_wr_data_count(NLW_U0_axis_wr_data_count_UNCONNECTED[10:0]),
        .backup(1'b0),
        .backup_marker(1'b0),
        .clk(1'b0),
        .data_count(NLW_U0_data_count_UNCONNECTED[9:0]),
        .dbiterr(NLW_U0_dbiterr_UNCONNECTED),
        .din(din),
        .dout(dout),
        .empty(empty),
        .full(full),
        .injectdbiterr(1'b0),
        .injectsbiterr(1'b0),
        .int_clk(1'b0),
        .m_aclk(1'b0),
        .m_aclk_en(1'b0),
        .m_axi_araddr(NLW_U0_m_axi_araddr_UNCONNECTED[31:0]),
        .m_axi_arburst(NLW_U0_m_axi_arburst_UNCONNECTED[1:0]),
        .m_axi_arcache(NLW_U0_m_axi_arcache_UNCONNECTED[3:0]),
        .m_axi_arid(NLW_U0_m_axi_arid_UNCONNECTED[0]),
        .m_axi_arlen(NLW_U0_m_axi_arlen_UNCONNECTED[7:0]),
        .m_axi_arlock(NLW_U0_m_axi_arlock_UNCONNECTED[0]),
        .m_axi_arprot(NLW_U0_m_axi_arprot_UNCONNECTED[2:0]),
        .m_axi_arqos(NLW_U0_m_axi_arqos_UNCONNECTED[3:0]),
        .m_axi_arready(1'b0),
        .m_axi_arregion(NLW_U0_m_axi_arregion_UNCONNECTED[3:0]),
        .m_axi_arsize(NLW_U0_m_axi_arsize_UNCONNECTED[2:0]),
        .m_axi_aruser(NLW_U0_m_axi_aruser_UNCONNECTED[0]),
        .m_axi_arvalid(NLW_U0_m_axi_arvalid_UNCONNECTED),
        .m_axi_awaddr(NLW_U0_m_axi_awaddr_UNCONNECTED[31:0]),
        .m_axi_awburst(NLW_U0_m_axi_awburst_UNCONNECTED[1:0]),
        .m_axi_awcache(NLW_U0_m_axi_awcache_UNCONNECTED[3:0]),
        .m_axi_awid(NLW_U0_m_axi_awid_UNCONNECTED[0]),
        .m_axi_awlen(NLW_U0_m_axi_awlen_UNCONNECTED[7:0]),
        .m_axi_awlock(NLW_U0_m_axi_awlock_UNCONNECTED[0]),
        .m_axi_awprot(NLW_U0_m_axi_awprot_UNCONNECTED[2:0]),
        .m_axi_awqos(NLW_U0_m_axi_awqos_UNCONNECTED[3:0]),
        .m_axi_awready(1'b0),
        .m_axi_awregion(NLW_U0_m_axi_awregion_UNCONNECTED[3:0]),
        .m_axi_awsize(NLW_U0_m_axi_awsize_UNCONNECTED[2:0]),
        .m_axi_awuser(NLW_U0_m_axi_awuser_UNCONNECTED[0]),
        .m_axi_awvalid(NLW_U0_m_axi_awvalid_UNCONNECTED),
        .m_axi_bid(1'b0),
        .m_axi_bready(NLW_U0_m_axi_bready_UNCONNECTED),
        .m_axi_bresp({1'b0,1'b0}),
        .m_axi_buser(1'b0),
        .m_axi_bvalid(1'b0),
        .m_axi_rdata({1'b0,1'b0,1'b0,1'b0,1'b0,1'b0,1'b0,1'b0,1'b0,1'b0,1'b0,1'b0,1'b0,1'b0,1'b0,1'b0,1'b0,1'b0,1'b0,1'b0,1'b0,1'b0,1'b0,1'b0,1'b0,1'b0,1'b0,1'b0,1'b0,1'b0,1'b0,1'b0,1'b0,1'b0,1'b0,1'b0,1'b0,1'b0,1'b0,1'b0,1'b0,1'b0,1'b0,1'b0,1'b0,1'b0,1'b0,1'b0,1'b0,1'b0,1'b0,1'b0,1'b0,1'b0,1'b0,1'b0,1'b0,1'b0,1'b0,1'b0,1'b0,1'b0,1'b0,1'b0}),
        .m_axi_rid(1'b0),
        .m_axi_rlast(1'b0),
        .m_axi_rready(NLW_U0_m_axi_rready_UNCONNECTED),
        .m_axi_rresp({1'b0,1'b0}),
        .m_axi_ruser(1'b0),
        .m_axi_rvalid(1'b0),
        .m_axi_wdata(NLW_U0_m_axi_wdata_UNCONNECTED[63:0]),
        .m_axi_wid(NLW_U0_m_axi_wid_UNCONNECTED[0]),
        .m_axi_wlast(NLW_U0_m_axi_wlast_UNCONNECTED),
        .m_axi_wready(1'b0),
        .m_axi_wstrb(NLW_U0_m_axi_wstrb_UNCONNECTED[7:0]),
        .m_axi_wuser(NLW_U0_m_axi_wuser_UNCONNECTED[0]),
        .m_axi_wvalid(NLW_U0_m_axi_wvalid_UNCONNECTED),
        .m_axis_tdata(NLW_U0_m_axis_tdata_UNCONNECTED[7:0]),
        .m_axis_tdest(NLW_U0_m_axis_tdest_UNCONNECTED[0]),
        .m_axis_tid(NLW_U0_m_axis_tid_UNCONNECTED[0]),
        .m_axis_tkeep(NLW_U0_m_axis_tkeep_UNCONNECTED[0]),
        .m_axis_tlast(NLW_U0_m_axis_tlast_UNCONNECTED),
        .m_axis_tready(1'b0),
        .m_axis_tstrb(NLW_U0_m_axis_tstrb_UNCONNECTED[0]),
        .m_axis_tuser(NLW_U0_m_axis_tuser_UNCONNECTED[3:0]),
        .m_axis_tvalid(NLW_U0_m_axis_tvalid_UNCONNECTED),
        .overflow(NLW_U0_overflow_UNCONNECTED),
        .prog_empty(NLW_U0_prog_empty_UNCONNECTED),
        .prog_empty_thresh({1'b0,1'b0,1'b0,1'b0,1'b0,1'b0,1'b0,1'b0,1'b0,1'b0,1'b0}),
        .prog_empty_thresh_assert({1'b0,1'b0,1'b0,1'b0,1'b0,1'b0,1'b0,1'b0,1'b0,1'b0,1'b0}),
        .prog_empty_thresh_negate({1'b0,1'b0,1'b0,1'b0,1'b0,1'b0,1'b0,1'b0,1'b0,1'b0,1'b0}),
        .prog_full(NLW_U0_prog_full_UNCONNECTED),
        .prog_full_thresh({1'b0,1'b0,1'b0,1'b0,1'b0,1'b0,1'b0,1'b0,1'b0,1'b0}),
        .prog_full_thresh_assert({1'b0,1'b0,1'b0,1'b0,1'b0,1'b0,1'b0,1'b0,1'b0,1'b0}),
        .prog_full_thresh_negate({1'b0,1'b0,1'b0,1'b0,1'b0,1'b0,1'b0,1'b0,1'b0,1'b0}),
        .rd_clk(rd_clk),
        .rd_data_count(NLW_U0_rd_data_count_UNCONNECTED[10:0]),
        .rd_en(rd_en),
        .rd_rst(1'b0),
        .rd_rst_busy(NLW_U0_rd_rst_busy_UNCONNECTED),
        .rst(rst),
        .s_aclk(1'b0),
        .s_aclk_en(1'b0),
        .s_aresetn(1'b0),
        .s_axi_araddr({1'b0,1'b0,1'b0,1'b0,1'b0,1'b0,1'b0,1'b0,1'b0,1'b0,1'b0,1'b0,1'b0,1'b0,1'b0,1'b0,1'b0,1'b0,1'b0,1'b0,1'b0,1'b0,1'b0,1'b0,1'b0,1'b0,1'b0,1'b0,1'b0,1'b0,1'b0,1'b0}),
        .s_axi_arburst({1'b0,1'b0}),
        .s_axi_arcache({1'b0,1'b0,1'b0,1'b0}),
        .s_axi_arid(1'b0),
        .s_axi_arlen({1'b0,1'b0,1'b0,1'b0,1'b0,1'b0,1'b0,1'b0}),
        .s_axi_arlock(1'b0),
        .s_axi_arprot({1'b0,1'b0,1'b0}),
        .s_axi_arqos({1'b0,1'b0,1'b0,1'b0}),
        .s_axi_arready(NLW_U0_s_axi_arready_UNCONNECTED),
        .s_axi_arregion({1'b0,1'b0,1'b0,1'b0}),
        .s_axi_arsize({1'b0,1'b0,1'b0}),
        .s_axi_aruser(1'b0),
        .s_axi_arvalid(1'b0),
        .s_axi_awaddr({1'b0,1'b0,1'b0,1'b0,1'b0,1'b0,1'b0,1'b0,1'b0,1'b0,1'b0,1'b0,1'b0,1'b0,1'b0,1'b0,1'b0,1'b0,1'b0,1'b0,1'b0,1'b0,1'b0,1'b0,1'b0,1'b0,1'b0,1'b0,1'b0,1'b0,1'b0,1'b0}),
        .s_axi_awburst({1'b0,1'b0}),
        .s_axi_awcache({1'b0,1'b0,1'b0,1'b0}),
        .s_axi_awid(1'b0),
        .s_axi_awlen({1'b0,1'b0,1'b0,1'b0,1'b0,1'b0,1'b0,1'b0}),
        .s_axi_awlock(1'b0),
        .s_axi_awprot({1'b0,1'b0,1'b0}),
        .s_axi_awqos({1'b0,1'b0,1'b0,1'b0}),
        .s_axi_awready(NLW_U0_s_axi_awready_UNCONNECTED),
        .s_axi_awregion({1'b0,1'b0,1'b0,1'b0}),
        .s_axi_awsize({1'b0,1'b0,1'b0}),
        .s_axi_awuser(1'b0),
        .s_axi_awvalid(1'b0),
        .s_axi_bid(NLW_U0_s_axi_bid_UNCONNECTED[0]),
        .s_axi_bready(1'b0),
        .s_axi_bresp(NLW_U0_s_axi_bresp_UNCONNECTED[1:0]),
        .s_axi_buser(NLW_U0_s_axi_buser_UNCONNECTED[0]),
        .s_axi_bvalid(NLW_U0_s_axi_bvalid_UNCONNECTED),
        .s_axi_rdata(NLW_U0_s_axi_rdata_UNCONNECTED[63:0]),
        .s_axi_rid(NLW_U0_s_axi_rid_UNCONNECTED[0]),
        .s_axi_rlast(NLW_U0_s_axi_rlast_UNCONNECTED),
        .s_axi_rready(1'b0),
        .s_axi_rresp(NLW_U0_s_axi_rresp_UNCONNECTED[1:0]),
        .s_axi_ruser(NLW_U0_s_axi_ruser_UNCONNECTED[0]),
        .s_axi_rvalid(NLW_U0_s_axi_rvalid_UNCONNECTED),
        .s_axi_wdata({1'b0,1'b0,1'b0,1'b0,1'b0,1'b0,1'b0,1'b0,1'b0,1'b0,1'b0,1'b0,1'b0,1'b0,1'b0,1'b0,1'b0,1'b0,1'b0,1'b0,1'b0,1'b0,1'b0,1'b0,1'b0,1'b0,1'b0,1'b0,1'b0,1'b0,1'b0,1'b0,1'b0,1'b0,1'b0,1'b0,1'b0,1'b0,1'b0,1'b0,1'b0,1'b0,1'b0,1'b0,1'b0,1'b0,1'b0,1'b0,1'b0,1'b0,1'b0,1'b0,1'b0,1'b0,1'b0,1'b0,1'b0,1'b0,1'b0,1'b0,1'b0,1'b0,1'b0,1'b0}),
        .s_axi_wid(1'b0),
        .s_axi_wlast(1'b0),
        .s_axi_wready(NLW_U0_s_axi_wready_UNCONNECTED),
        .s_axi_wstrb({1'b0,1'b0,1'b0,1'b0,1'b0,1'b0,1'b0,1'b0}),
        .s_axi_wuser(1'b0),
        .s_axi_wvalid(1'b0),
        .s_axis_tdata({1'b0,1'b0,1'b0,1'b0,1'b0,1'b0,1'b0,1'b0}),
        .s_axis_tdest(1'b0),
        .s_axis_tid(1'b0),
        .s_axis_tkeep(1'b0),
        .s_axis_tlast(1'b0),
        .s_axis_tready(NLW_U0_s_axis_tready_UNCONNECTED),
        .s_axis_tstrb(1'b0),
        .s_axis_tuser({1'b0,1'b0,1'b0,1'b0}),
        .s_axis_tvalid(1'b0),
        .sbiterr(NLW_U0_sbiterr_UNCONNECTED),
        .sleep(1'b0),
        .srst(1'b0),
        .underflow(NLW_U0_underflow_UNCONNECTED),
        .valid(NLW_U0_valid_UNCONNECTED),
        .wr_ack(NLW_U0_wr_ack_UNCONNECTED),
        .wr_clk(wr_clk),
        .wr_data_count(NLW_U0_wr_data_count_UNCONNECTED[9:0]),
        .wr_en(wr_en),
        .wr_rst(1'b0),
        .wr_rst_busy(NLW_U0_wr_rst_busy_UNCONNECTED));
endmodule

(* DEF_VAL = "1'b0" *) (* DEST_SYNC_FF = "2" *) (* INIT_SYNC_FF = "0" *) 
(* INV_DEF_VAL = "1'b1" *) (* ORIG_REF_NAME = "xpm_cdc_async_rst" *) (* RST_ACTIVE_HIGH = "1" *) 
(* VERSION = "0" *) (* XPM_MODULE = "TRUE" *) (* xpm_cdc = "ASYNC_RST" *) 
module FPGAtoFTDI_fifo_xpm_cdc_async_rst
   (src_arst,
    dest_clk,
    dest_arst);
  input src_arst;
  input dest_clk;
  output dest_arst;

  (* RTL_KEEP = "true" *) (* async_reg = "true" *) (* xpm_cdc = "ASYNC_RST" *) wire [1:0]arststages_ff;
  wire dest_clk;
  wire src_arst;

  assign dest_arst = arststages_ff[1];
  (* ASYNC_REG *) 
  (* KEEP = "true" *) 
  (* XPM_CDC = "ASYNC_RST" *) 
  FDPE #(
    .INIT(1'b0)) 
    \arststages_ff_reg[0] 
       (.C(dest_clk),
        .CE(1'b1),
        .D(1'b0),
        .PRE(src_arst),
        .Q(arststages_ff[0]));
  (* ASYNC_REG *) 
  (* KEEP = "true" *) 
  (* XPM_CDC = "ASYNC_RST" *) 
  FDPE #(
    .INIT(1'b0)) 
    \arststages_ff_reg[1] 
       (.C(dest_clk),
        .CE(1'b1),
        .D(arststages_ff[0]),
        .PRE(src_arst),
        .Q(arststages_ff[1]));
endmodule

(* DEF_VAL = "1'b0" *) (* DEST_SYNC_FF = "2" *) (* INIT_SYNC_FF = "0" *) 
(* INV_DEF_VAL = "1'b1" *) (* ORIG_REF_NAME = "xpm_cdc_async_rst" *) (* RST_ACTIVE_HIGH = "1" *) 
(* VERSION = "0" *) (* XPM_MODULE = "TRUE" *) (* xpm_cdc = "ASYNC_RST" *) 
module FPGAtoFTDI_fifo_xpm_cdc_async_rst__1
   (src_arst,
    dest_clk,
    dest_arst);
  input src_arst;
  input dest_clk;
  output dest_arst;

  (* RTL_KEEP = "true" *) (* async_reg = "true" *) (* xpm_cdc = "ASYNC_RST" *) wire [1:0]arststages_ff;
  wire dest_clk;
  wire src_arst;

  assign dest_arst = arststages_ff[1];
  (* ASYNC_REG *) 
  (* KEEP = "true" *) 
  (* XPM_CDC = "ASYNC_RST" *) 
  FDPE #(
    .INIT(1'b0)) 
    \arststages_ff_reg[0] 
       (.C(dest_clk),
        .CE(1'b1),
        .D(1'b0),
        .PRE(src_arst),
        .Q(arststages_ff[0]));
  (* ASYNC_REG *) 
  (* KEEP = "true" *) 
  (* XPM_CDC = "ASYNC_RST" *) 
  FDPE #(
    .INIT(1'b0)) 
    \arststages_ff_reg[1] 
       (.C(dest_clk),
        .CE(1'b1),
        .D(arststages_ff[0]),
        .PRE(src_arst),
        .Q(arststages_ff[1]));
endmodule

(* DEST_SYNC_FF = "2" *) (* INIT_SYNC_FF = "0" *) (* ORIG_REF_NAME = "xpm_cdc_gray" *) 
(* REG_OUTPUT = "1" *) (* SIM_ASSERT_CHK = "0" *) (* SIM_LOSSLESS_GRAY_CHK = "0" *) 
(* VERSION = "0" *) (* WIDTH = "10" *) (* XPM_MODULE = "TRUE" *) 
(* xpm_cdc = "GRAY" *) 
module FPGAtoFTDI_fifo_xpm_cdc_gray
   (src_clk,
    src_in_bin,
    dest_clk,
    dest_out_bin);
  input src_clk;
  input [9:0]src_in_bin;
  input dest_clk;
  output [9:0]dest_out_bin;

  wire [9:0]async_path;
  wire [8:0]binval;
  wire dest_clk;
  (* RTL_KEEP = "true" *) (* async_reg = "true" *) (* xpm_cdc = "GRAY" *) wire [9:0]\dest_graysync_ff[0] ;
  (* RTL_KEEP = "true" *) (* async_reg = "true" *) (* xpm_cdc = "GRAY" *) wire [9:0]\dest_graysync_ff[1] ;
  wire [9:0]dest_out_bin;
  wire [8:0]gray_enc;
  wire src_clk;
  wire [9:0]src_in_bin;

  (* ASYNC_REG *) 
  (* KEEP = "true" *) 
  (* XPM_CDC = "GRAY" *) 
  FDRE \dest_graysync_ff_reg[0][0] 
       (.C(dest_clk),
        .CE(1'b1),
        .D(async_path[0]),
        .Q(\dest_graysync_ff[0] [0]),
        .R(1'b0));
  (* ASYNC_REG *) 
  (* KEEP = "true" *) 
  (* XPM_CDC = "GRAY" *) 
  FDRE \dest_graysync_ff_reg[0][1] 
       (.C(dest_clk),
        .CE(1'b1),
        .D(async_path[1]),
        .Q(\dest_graysync_ff[0] [1]),
        .R(1'b0));
  (* ASYNC_REG *) 
  (* KEEP = "true" *) 
  (* XPM_CDC = "GRAY" *) 
  FDRE \dest_graysync_ff_reg[0][2] 
       (.C(dest_clk),
        .CE(1'b1),
        .D(async_path[2]),
        .Q(\dest_graysync_ff[0] [2]),
        .R(1'b0));
  (* ASYNC_REG *) 
  (* KEEP = "true" *) 
  (* XPM_CDC = "GRAY" *) 
  FDRE \dest_graysync_ff_reg[0][3] 
       (.C(dest_clk),
        .CE(1'b1),
        .D(async_path[3]),
        .Q(\dest_graysync_ff[0] [3]),
        .R(1'b0));
  (* ASYNC_REG *) 
  (* KEEP = "true" *) 
  (* XPM_CDC = "GRAY" *) 
  FDRE \dest_graysync_ff_reg[0][4] 
       (.C(dest_clk),
        .CE(1'b1),
        .D(async_path[4]),
        .Q(\dest_graysync_ff[0] [4]),
        .R(1'b0));
  (* ASYNC_REG *) 
  (* KEEP = "true" *) 
  (* XPM_CDC = "GRAY" *) 
  FDRE \dest_graysync_ff_reg[0][5] 
       (.C(dest_clk),
        .CE(1'b1),
        .D(async_path[5]),
        .Q(\dest_graysync_ff[0] [5]),
        .R(1'b0));
  (* ASYNC_REG *) 
  (* KEEP = "true" *) 
  (* XPM_CDC = "GRAY" *) 
  FDRE \dest_graysync_ff_reg[0][6] 
       (.C(dest_clk),
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
        .O(gray_enc[2]));
  (* SOFT_HLUTNM = "soft_lutpair1" *) 
  LUT2 #(
    .INIT(4'h6)) 
    \src_gray_ff[3]_i_1 
       (.I0(src_in_bin[4]),
        .I1(src_in_bin[3]),
        .O(gray_enc[3]));
  (* SOFT_HLUTNM = "soft_lutpair2" *) 
  LUT2 #(
    .INIT(4'h6)) 
    \src_gray_ff[4]_i_1 
       (.I0(src_in_bin[5]),
        .I1(src_in_bin[4]),
        .O(gray_enc[4]));
  (* SOFT_HLUTNM = "soft_lutpair2" *) 
  LUT2 #(
    .INIT(4'h6)) 
    \src_gray_ff[5]_i_1 
       (.I0(src_in_bin[6]),
        .I1(src_in_bin[5]),
        .O(gray_enc[5]));
  (* SOFT_HLUTNM = "soft_lutpair3" *) 
  LUT2 #(
    .INIT(4'h6)) 
    \src_gray_ff[6]_i_1 
       (.I0(src_in_bin[7]),
        .I1(src_in_bin[6]),
        .O(gray_enc[6]));
  (* SOFT_HLUTNM = "soft_lutpair3" *) 
  LUT2 #(
    .INIT(4'h6)) 
    \src_gray_ff[7]_i_1 
       (.I0(src_in_bin[8]),
        .I1(src_in_bin[7]),
        .O(gray_enc[7]));
  LUT2 #(
    .INIT(4'h6)) 
    \src_gray_ff[8]_i_1 
       (.I0(src_in_bin[9]),
        .I1(src_in_bin[8]),
        .O(gray_enc[8]));
  FDRE \src_gray_ff_reg[0] 
       (.C(src_clk),
        .CE(1'b1),
        .D(gray_enc[0]),
        .Q(async_path[0]),
        .R(1'b0));
  FDRE \src_gray_ff_reg[1] 
       (.C(src_clk),
        .CE(1'b1),
        .D(gray_enc[1]),
        .Q(async_path[1]),
        .R(1'b0));
  FDRE \src_gray_ff_reg[2] 
       (.C(src_clk),
        .CE(1'b1),
        .D(gray_enc[2]),
        .Q(async_path[2]),
        .R(1'b0));
  FDRE \src_gray_ff_reg[3] 
       (.C(src_clk),
        .CE(1'b1),
        .D(gray_enc[3]),
        .Q(async_path[3]),
        .R(1'b0));
  FDRE \src_gray_ff_reg[4] 
       (.C(src_clk),
        .CE(1'b1),
        .D(gray_enc[4]),
        .Q(async_path[4]),
        .R(1'b0));
  FDRE \src_gray_ff_reg[5] 
       (.C(src_clk),
        .CE(1'b1),
        .D(gray_enc[5]),
        .Q(async_path[5]),
        .R(1'b0));
  FDRE \src_gray_ff_reg[6] 
       (.C(src_clk),
        .CE(1'b1),
        .D(gray_enc[6]),
        .Q(async_path[6]),
        .R(1'b0));
  FDRE \src_gray_ff_reg[7] 
       (.C(src_clk),
        .CE(1'b1),
        .D(gray_enc[7]),
        .Q(async_path[7]),
        .R(1'b0));
  FDRE \src_gray_ff_reg[8] 
       (.C(src_clk),
        .CE(1'b1),
        .D(gray_enc[8]),
        .Q(async_path[8]),
        .R(1'b0));
  FDRE \src_gray_ff_reg[9] 
       (.C(src_clk),
        .CE(1'b1),
        .D(src_in_bin[9]),
        .Q(async_path[9]),
        .R(1'b0));
endmodule

(* DEST_SYNC_FF = "2" *) (* INIT_SYNC_FF = "0" *) (* ORIG_REF_NAME = "xpm_cdc_gray" *) 
(* REG_OUTPUT = "1" *) (* SIM_ASSERT_CHK = "0" *) (* SIM_LOSSLESS_GRAY_CHK = "0" *) 
(* VERSION = "0" *) (* WIDTH = "11" *) (* XPM_MODULE = "TRUE" *) 
(* xpm_cdc = "GRAY" *) 
module FPGAtoFTDI_fifo_xpm_cdc_gray__parameterized0
   (src_clk,
    src_in_bin,
    dest_clk,
    dest_out_bin);
  input src_clk;
  input [10:0]src_in_bin;
  input dest_clk;
  output [10:0]dest_out_bin;

  wire [10:0]async_path;
  wire [9:0]binval;
  wire dest_clk;
  (* RTL_KEEP = "true" *) (* async_reg = "true" *) (* xpm_cdc = "GRAY" *) wire [10:0]\dest_graysync_ff[0] ;
  (* RTL_KEEP = "true" *) (* async_reg = "true" *) (* xpm_cdc = "GRAY" *) wire [10:0]\dest_graysync_ff[1] ;
  wire [10:0]dest_out_bin;
  wire [9:0]gray_enc;
  wire src_clk;
  wire [10:0]src_in_bin;

  (* ASYNC_REG *) 
  (* KEEP = "true" *) 
  (* XPM_CDC = "GRAY" *) 
  FDRE \dest_graysync_ff_reg[0][0] 
       (.C(dest_clk),
        .CE(1'b1),
        .D(async_path[0]),
        .Q(\dest_graysync_ff[0] [0]),
        .R(1'b0));
  (* ASYNC_REG *) 
  (* KEEP = "true" *) 
  (* XPM_CDC = "GRAY" *) 
  FDRE \dest_graysync_ff_reg[0][10] 
       (.C(dest_clk),
        .CE(1'b1),
        .D(async_path[10]),
        .Q(\dest_graysync_ff[0] [10]),
        .R(1'b0));
  (* ASYNC_REG *) 
  (* KEEP = "true" *) 
  (* XPM_CDC = "GRAY" *) 
  FDRE \dest_graysync_ff_reg[0][1] 
       (.C(dest_clk),
        .CE(1'b1),
        .D(async_path[1]),
        .Q(\dest_graysync_ff[0] [1]),
        .R(1'b0));
  (* ASYNC_REG *) 
  (* KEEP = "true" *) 
  (* XPM_CDC = "GRAY" *) 
  FDRE \dest_graysync_ff_reg[0][2] 
       (.C(dest_clk),
        .CE(1'b1),
        .D(async_path[2]),
        .Q(\dest_graysync_ff[0] [2]),
        .R(1'b0));
  (* ASYNC_REG *) 
  (* KEEP = "true" *) 
  (* XPM_CDC = "GRAY" *) 
  FDRE \dest_graysync_ff_reg[0][3] 
       (.C(dest_clk),
        .CE(1'b1),
        .D(async_path[3]),
        .Q(\dest_graysync_ff[0] [3]),
        .R(1'b0));
  (* ASYNC_REG *) 
  (* KEEP = "true" *) 
  (* XPM_CDC = "GRAY" *) 
  FDRE \dest_graysync_ff_reg[0][4] 
       (.C(dest_clk),
        .CE(1'b1),
        .D(async_path[4]),
        .Q(\dest_graysync_ff[0] [4]),
        .R(1'b0));
  (* ASYNC_REG *) 
  (* KEEP = "true" *) 
  (* XPM_CDC = "GRAY" *) 
  FDRE \dest_graysync_ff_reg[0][5] 
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
        .R(1'b0));
  FDRE \src_gray_ff_reg[5] 
       (.C(src_clk),
        .CE(1'b1),
        .D(gray_enc[5]),
        .Q(async_path[5]),
        .R(1'b0));
  FDRE \src_gray_ff_reg[6] 
       (.C(src_clk),
        .CE(1'b1),
        .D(gray_enc[6]),
        .Q(async_path[6]),
        .R(1'b0));
  FDRE \src_gray_ff_reg[7] 
       (.C(src_clk),
        .CE(1'b1),
        .D(gray_enc[7]),
        .Q(async_path[7]),
        .R(1'b0));
  FDRE \src_gray_ff_reg[8] 
       (.C(src_clk),
        .CE(1'b1),
        .D(gray_enc[8]),
        .Q(async_path[8]),
        .R(1'b0));
  FDRE \src_gray_ff_reg[9] 
       (.C(src_clk),
        .CE(1'b1),
        .D(gray_enc[9]),
        .Q(async_path[9]),
        .R(1'b0));
endmodule

(* DEST_SYNC_FF = "4" *) (* INIT_SYNC_FF = "0" *) (* ORIG_REF_NAME = "xpm_cdc_single" *) 
(* SIM_ASSERT_CHK = "0" *) (* SRC_INPUT_REG = "0" *) (* VERSION = "0" *) 
(* XPM_MODULE = "TRUE" *) (* xpm_cdc = "SINGLE" *) 
module FPGAtoFTDI_fifo_xpm_cdc_single
   (src_clk,
    src_in,
    dest_clk,
    dest_out);
  input src_clk;
  input src_in;
  input dest_clk;
  output dest_out;

  wire dest_clk;
  wire src_in;
  (* RTL_KEEP = "true" *) (* async_reg = "true" *) (* xpm_cdc = "SINGLE" *) wire [3:0]syncstages_ff;

  assign dest_out = syncstages_ff[3];
  (* ASYNC_REG *) 
  (* KEEP = "true" *) 
  (* XPM_CDC = "SINGLE" *) 
  FDRE \syncstages_ff_reg[0] 
       (.C(dest_clk),
        .CE(1'b1),
        .D(src_in),
        .Q(syncstages_ff[0]),
        .R(1'b0));
  (* ASYNC_REG *) 
  (* KEEP = "true" *) 
  (* XPM_CDC = "SINGLE" *) 
  FDRE \syncstages_ff_reg[1] 
       (.C(dest_clk),
        .CE(1'b1),
        .D(syncstages_ff[0]),
        .Q(syncstages_ff[1]),
        .R(1'b0));
  (* ASYNC_REG *) 
  (* KEEP = "true" *) 
  (* XPM_CDC = "SINGLE" *) 
  FDRE \syncstages_ff_reg[2] 
       (.C(dest_clk),
        .CE(1'b1),
        .D(syncstages_ff[1]),
        .Q(syncstages_ff[2]),
        .R(1'b0));
  (* ASYNC_REG *) 
  (* KEEP = "true" *) 
  (* XPM_CDC = "SINGLE" *) 
  FDRE \syncstages_ff_reg[3] 
       (.C(dest_clk),
        .CE(1'b1),
        .D(syncstages_ff[2]),
        .Q(syncstages_ff[3]),
        .R(1'b0));
endmodule

(* DEST_SYNC_FF = "4" *) (* INIT_SYNC_FF = "0" *) (* ORIG_REF_NAME = "xpm_cdc_single" *) 
(* SIM_ASSERT_CHK = "0" *) (* SRC_INPUT_REG = "0" *) (* VERSION = "0" *) 
(* XPM_MODULE = "TRUE" *) (* xpm_cdc = "SINGLE" *) 
module FPGAtoFTDI_fifo_xpm_cdc_single__1
   (src_clk,
    src_in,
    dest_clk,
    dest_out);
  input src_clk;
  input src_in;
  input dest_clk;
  output dest_out;

  wire dest_clk;
  wire src_in;
  (* RTL_KEEP = "true" *) (* async_reg = "true" *) (* xpm_cdc = "SINGLE" *) wire [3:0]syncstages_ff;

  assign dest_out = syncstages_ff[3];
  (* ASYNC_REG *) 
  (* KEEP = "true" *) 
  (* XPM_CDC = "SINGLE" *) 
  FDRE \syncstages_ff_reg[0] 
       (.C(dest_clk),
        .CE(1'b1),
        .D(src_in),
        .Q(syncstages_ff[0]),
        .R(1'b0));
  (* ASYNC_REG *) 
  (* KEEP = "true" *) 
  (* XPM_CDC = "SINGLE" *) 
  FDRE \syncstages_ff_reg[1] 
       (.C(dest_clk),
        .CE(1'b1),
        .D(syncstages_ff[0]),
        .Q(syncstages_ff[1]),
        .R(1'b0));
  (* ASYNC_REG *) 
  (* KEEP = "true" *) 
  (* XPM_CDC = "SINGLE" *) 
  FDRE \syncstages_ff_reg[2] 
       (.C(dest_clk),
        .CE(1'b1),
        .D(syncstages_ff[1]),
        .Q(syncstages_ff[2]),
        .R(1'b0));
  (* ASYNC_REG *) 
  (* KEEP = "true" *) 
  (* XPM_CDC = "SINGLE" *) 
  FDRE \syncstages_ff_reg[3] 
       (.C(dest_clk),
        .CE(1'b1),
        .D(syncstages_ff[2]),
        .Q(syncstages_ff[3]),
        .R(1'b0));
endmodule

(* ORIG_REF_NAME = "blk_mem_gen_generic_cstr" *) 
module FPGAtoFTDI_fifo_blk_mem_gen_generic_cstr
   (dout,
    wr_clk,
    rd_clk,
    E,
    tmp_ram_rd_en,
    AR,
    \gic0.gc0.count_d2_reg[9] ,
    \gc0.count_d1_reg[10] ,
    din);
  output [7:0]dout;
  input wr_clk;
  input rd_clk;
  input [0:0]E;
  input tmp_ram_rd_en;
  input [0:0]AR;
  input [9:0]\gic0.gc0.count_d2_reg[9] ;
  input [10:0]\gc0.count_d1_reg[10] ;
  input [15:0]din;

  wire [0:0]AR;
  wire [0:0]E;
  wire [15:0]din;
  wire [7:0]dout;
  wire [10:0]\gc0.count_d1_reg[10] ;
  wire [9:0]\gic0.gc0.count_d2_reg[9] ;
  wire rd_clk;
  wire tmp_ram_rd_en;
  wire wr_clk;

  FPGAtoFTDI_fifo_blk_mem_gen_prim_width \ramloop[0].ram.r 
       (.AR(AR),
        .E(E),
        .din(din),
        .dout(dout),
        .\gc0.count_d1_reg[10] (\gc0.count_d1_reg[10] ),
        .\gic0.gc0.count_d2_reg[9] (\gic0.gc0.count_d2_reg[9] ),
        .rd_clk(rd_clk),
        .tmp_ram_rd_en(tmp_ram_rd_en),
        .wr_clk(wr_clk));
endmodule

(* ORIG_REF_NAME = "blk_mem_gen_prim_width" *) 
module FPGAtoFTDI_fifo_blk_mem_gen_prim_width
   (dout,
    wr_clk,
    rd_clk,
    E,
    tmp_ram_rd_en,
    AR,
    \gic0.gc0.count_d2_reg[9] ,
    \gc0.count_d1_reg[10] ,
    din);
  output [7:0]dout;
  input wr_clk;
  input rd_clk;
  input [0:0]E;
  input tmp_ram_rd_en;
  input [0:0]AR;
  input [9:0]\gic0.gc0.count_d2_reg[9] ;
  input [10:0]\gc0.count_d1_reg[10] ;
  input [15:0]din;

  wire [0:0]AR;
  wire [0:0]E;
  wire [15:0]din;
  wire [7:0]dout;
  wire [10:0]\gc0.count_d1_reg[10] ;
  wire [9:0]\gic0.gc0.count_d2_reg[9] ;
  wire rd_clk;
  wire tmp_ram_rd_en;
  wire wr_clk;

  FPGAtoFTDI_fifo_blk_mem_gen_prim_wrapper \prim_noinit.ram 
       (.AR(AR),
        .E(E),
        .din(din),
        .dout(dout),
        .\gc0.count_d1_reg[10] (\gc0.count_d1_reg[10] ),
        .\gic0.gc0.count_d2_reg[9] (\gic0.gc0.count_d2_reg[9] ),
        .rd_clk(rd_clk),
        .tmp_ram_rd_en(tmp_ram_rd_en),
        .wr_clk(wr_clk));
endmodule

(* ORIG_REF_NAME = "blk_mem_gen_prim_wrapper" *) 
module FPGAtoFTDI_fifo_blk_mem_gen_prim_wrapper
   (dout,
    wr_clk,
    rd_clk,
    E,
    tmp_ram_rd_en,
    AR,
    \gic0.gc0.count_d2_reg[9] ,
    \gc0.count_d1_reg[10] ,
    din);
  output [7:0]dout;
  input wr_clk;
  input rd_clk;
  input [0:0]E;
  input tmp_ram_rd_en;
  input [0:0]AR;
  input [9:0]\gic0.gc0.count_d2_reg[9] ;
  input [10:0]\gc0.count_d1_reg[10] ;
  input [15:0]din;

  wire [0:0]AR;
  wire \DEVICE_7SERIES.NO_BMM_INFO.SDP.SIMPLE_PRIM18.ram_n_35 ;
  wire [0:0]E;
  wire [15:0]din;
  wire [7:0]dout;
  wire [10:0]\gc0.count_d1_reg[10] ;
  wire [9:0]\gic0.gc0.count_d2_reg[9] ;
  wire rd_clk;
  wire tmp_ram_rd_en;
  wire wr_clk;
  wire [15:0]\NLW_DEVICE_7SERIES.NO_BMM_INFO.SDP.SIMPLE_PRIM18.ram_DOADO_UNCONNECTED ;
  wire [15:8]\NLW_DEVICE_7SERIES.NO_BMM_INFO.SDP.SIMPLE_PRIM18.ram_DOBDO_UNCONNECTED ;
  wire [1:0]\NLW_DEVICE_7SERIES.NO_BMM_INFO.SDP.SIMPLE_PRIM18.ram_DOPADOP_UNCONNECTED ;
  wire [1:1]\NLW_DEVICE_7SERIES.NO_BMM_INFO.SDP.SIMPLE_PRIM18.ram_DOPBDOP_UNCONNECTED ;

  (* box_type = "PRIMITIVE" *) 
  RAMB18E1 #(
    .DOA_REG(0),
    .DOB_REG(0),
    .INITP_00(256'h0000000000000000000000000000000000000000000000000000000000000000),
    .INITP_01(256'h0000000000000000000000000000000000000000000000000000000000000000),
    .INITP_02(256'h0000000000000000000000000000000000000000000000000000000000000000),
    .INITP_03(256'h0000000000000000000000000000000000000000000000000000000000000000),
    .INITP_04(256'h0000000000000000000000000000000000000000000000000000000000000000),
    .INITP_05(256'h0000000000000000000000000000000000000000000000000000000000000000),
    .INITP_06(256'h0000000000000000000000000000000000000000000000000000000000000000),
    .INITP_07(256'h0000000000000000000000000000000000000000000000000000000000000000),
    .INIT_00(256'h0000000000000000000000000000000000000000000000000000000000000000),
    .INIT_01(256'h0000000000000000000000000000000000000000000000000000000000000000),
    .INIT_02(256'h0000000000000000000000000000000000000000000000000000000000000000),
    .INIT_03(256'h0000000000000000000000000000000000000000000000000000000000000000),
    .INIT_04(256'h0000000000000000000000000000000000000000000000000000000000000000),
    .INIT_05(256'h0000000000000000000000000000000000000000000000000000000000000000),
    .INIT_06(256'h0000000000000000000000000000000000000000000000000000000000000000),
    .INIT_07(256'h0000000000000000000000000000000000000000000000000000000000000000),
    .INIT_08(256'h0000000000000000000000000000000000000000000000000000000000000000),
    .INIT_09(256'h0000000000000000000000000000000000000000000000000000000000000000),
    .INIT_0A(256'h0000000000000000000000000000000000000000000000000000000000000000),
    .INIT_0B(256'h0000000000000000000000000000000000000000000000000000000000000000),
    .INIT_0C(256'h0000000000000000000000000000000000000000000000000000000000000000),
    .INIT_0D(256'h0000000000000000000000000000000000000000000000000000000000000000),
    .INIT_0E(256'h0000000000000000000000000000000000000000000000000000000000000000),
    .INIT_0F(256'h0000000000000000000000000000000000000000000000000000000000000000),
    .INIT_10(256'h0000000000000000000000000000000000000000000000000000000000000000),
    .INIT_11(256'h0000000000000000000000000000000000000000000000000000000000000000),
    .INIT_12(256'h0000000000000000000000000000000000000000000000000000000000000000),
    .INIT_13(256'h0000000000000000000000000000000000000000000000000000000000000000),
    .INIT_14(256'h0000000000000000000000000000000000000000000000000000000000000000),
    .INIT_15(256'h0000000000000000000000000000000000000000000000000000000000000000),
    .INIT_16(256'h0000000000000000000000000000000000000000000000000000000000000000),
    .INIT_17(256'h0000000000000000000000000000000000000000000000000000000000000000),
    .INIT_18(256'h0000000000000000000000000000000000000000000000000000000000000000),
    .INIT_19(256'h0000000000000000000000000000000000000000000000000000000000000000),
    .INIT_1A(256'h0000000000000000000000000000000000000000000000000000000000000000),
    .INIT_1B(256'h0000000000000000000000000000000000000000000000000000000000000000),
    .INIT_1C(256'h0000000000000000000000000000000000000000000000000000000000000000),
    .INIT_1D(256'h0000000000000000000000000000000000000000000000000000000000000000),
    .INIT_1E(256'h0000000000000000000000000000000000000000000000000000000000000000),
    .INIT_1F(256'h0000000000000000000000000000000000000000000000000000000000000000),
    .INIT_20(256'h0000000000000000000000000000000000000000000000000000000000000000),
    .INIT_21(256'h0000000000000000000000000000000000000000000000000000000000000000),
    .INIT_22(256'h0000000000000000000000000000000000000000000000000000000000000000),
    .INIT_23(256'h0000000000000000000000000000000000000000000000000000000000000000),
    .INIT_24(256'h0000000000000000000000000000000000000000000000000000000000000000),
    .INIT_25(256'h0000000000000000000000000000000000000000000000000000000000000000),
    .INIT_26(256'h0000000000000000000000000000000000000000000000000000000000000000),
    .INIT_27(256'h0000000000000000000000000000000000000000000000000000000000000000),
    .INIT_28(256'h0000000000000000000000000000000000000000000000000000000000000000),
    .INIT_29(256'h0000000000000000000000000000000000000000000000000000000000000000),
    .INIT_2A(256'h0000000000000000000000000000000000000000000000000000000000000000),
    .INIT_2B(256'h0000000000000000000000000000000000000000000000000000000000000000),
    .INIT_2C(256'h0000000000000000000000000000000000000000000000000000000000000000),
    .INIT_2D(256'h0000000000000000000000000000000000000000000000000000000000000000),
    .INIT_2E(256'h0000000000000000000000000000000000000000000000000000000000000000),
    .INIT_2F(256'h0000000000000000000000000000000000000000000000000000000000000000),
    .INIT_30(256'h0000000000000000000000000000000000000000000000000000000000000000),
    .INIT_31(256'h0000000000000000000000000000000000000000000000000000000000000000),
    .INIT_32(256'h0000000000000000000000000000000000000000000000000000000000000000),
    .INIT_33(256'h0000000000000000000000000000000000000000000000000000000000000000),
    .INIT_34(256'h0000000000000000000000000000000000000000000000000000000000000000),
    .INIT_35(256'h0000000000000000000000000000000000000000000000000000000000000000),
    .INIT_36(256'h0000000000000000000000000000000000000000000000000000000000000000),
    .INIT_37(256'h0000000000000000000000000000000000000000000000000000000000000000),
    .INIT_38(256'h0000000000000000000000000000000000000000000000000000000000000000),
    .INIT_39(256'h0000000000000000000000000000000000000000000000000000000000000000),
    .INIT_3A(256'h0000000000000000000000000000000000000000000000000000000000000000),
    .INIT_3B(256'h0000000000000000000000000000000000000000000000000000000000000000),
    .INIT_3C(256'h0000000000000000000000000000000000000000000000000000000000000000),
    .INIT_3D(256'h0000000000000000000000000000000000000000000000000000000000000000),
    .INIT_3E(256'h0000000000000000000000000000000000000000000000000000000000000000),
    .INIT_3F(256'h0000000000000000000000000000000000000000000000000000000000000000),
    .INIT_A(18'h00000),
    .INIT_B(18'h00000),
    .INIT_FILE("NONE"),
    .IS_CLKARDCLK_INVERTED(1'b0),
    .IS_CLKBWRCLK_INVERTED(1'b0),
    .IS_ENARDEN_INVERTED(1'b0),
    .IS_ENBWREN_INVERTED(1'b0),
    .IS_RSTRAMARSTRAM_INVERTED(1'b0),
    .IS_RSTRAMB_INVERTED(1'b0),
    .IS_RSTREGARSTREG_INVERTED(1'b0),
    .IS_RSTREGB_INVERTED(1'b0),
    .RAM_MODE("TDP"),
    .RDADDR_COLLISION_HWCONFIG("DELAYED_WRITE"),
    .READ_WIDTH_A(9),
    .READ_WIDTH_B(9),
    .RSTREG_PRIORITY_A("REGCE"),
    .RSTREG_PRIORITY_B("REGCE"),
    .SIM_COLLISION_CHECK("ALL"),
    .SIM_DEVICE("7SERIES"),
    .SRVAL_A(18'h00000),
    .SRVAL_B(18'h00000),
    .WRITE_MODE_A("WRITE_FIRST"),
    .WRITE_MODE_B("WRITE_FIRST"),
    .WRITE_WIDTH_A(18),
    .WRITE_WIDTH_B(18)) 
    \DEVICE_7SERIES.NO_BMM_INFO.SDP.SIMPLE_PRIM18.ram 
       (.ADDRARDADDR({\gic0.gc0.count_d2_reg[9] ,1'b0,1'b0,1'b0,1'b0}),
        .ADDRBWRADDR({\gc0.count_d1_reg[10] ,1'b0,1'b0,1'b0}),
        .CLKARDCLK(wr_clk),
        .CLKBWRCLK(rd_clk),
        .DIADI({din[7:0],din[15:8]}),
        .DIBDI({1'b0,1'b0,1'b0,1'b0,1'b0,1'b0,1'b0,1'b0,1'b0,1'b0,1'b0,1'b0,1'b0,1'b0,1'b0,1'b0}),
        .DIPADIP({1'b0,1'b0}),
        .DIPBDIP({1'b0,1'b0}),
        .DOADO(\NLW_DEVICE_7SERIES.NO_BMM_INFO.SDP.SIMPLE_PRIM18.ram_DOADO_UNCONNECTED [15:0]),
        .DOBDO({\NLW_DEVICE_7SERIES.NO_BMM_INFO.SDP.SIMPLE_PRIM18.ram_DOBDO_UNCONNECTED [15:8],dout}),
        .DOPADOP(\NLW_DEVICE_7SERIES.NO_BMM_INFO.SDP.SIMPLE_PRIM18.ram_DOPADOP_UNCONNECTED [1:0]),
        .DOPBDOP({\NLW_DEVICE_7SERIES.NO_BMM_INFO.SDP.SIMPLE_PRIM18.ram_DOPBDOP_UNCONNECTED [1],\DEVICE_7SERIES.NO_BMM_INFO.SDP.SIMPLE_PRIM18.ram_n_35 }),
        .ENARDEN(E),
        .ENBWREN(tmp_ram_rd_en),
        .REGCEAREGCE(1'b0),
        .REGCEB(1'b0),
        .RSTRAMARSTRAM(1'b0),
        .RSTRAMB(AR),
        .RSTREGARSTREG(1'b0),
        .RSTREGB(1'b0),
        .WEA({E,E}),
        .WEBWE({1'b0,1'b0,1'b0,1'b0}));
endmodule

(* ORIG_REF_NAME = "blk_mem_gen_top" *) 
module FPGAtoFTDI_fifo_blk_mem_gen_top
   (dout,
    wr_clk,
    rd_clk,
    E,
    tmp_ram_rd_en,
    AR,
    \gic0.gc0.count_d2_reg[9] ,
    \gc0.count_d1_reg[10] ,
    din);
  output [7:0]dout;
  input wr_clk;
  input rd_clk;
  input [0:0]E;
  input tmp_ram_rd_en;
  input [0:0]AR;
  input [9:0]\gic0.gc0.count_d2_reg[9] ;
  input [10:0]\gc0.count_d1_reg[10] ;
  input [15:0]din;

  wire [0:0]AR;
  wire [0:0]E;
  wire [15:0]din;
  wire [7:0]dout;
  wire [10:0]\gc0.count_d1_reg[10] ;
  wire [9:0]\gic0.gc0.count_d2_reg[9] ;
  wire rd_clk;
  wire tmp_ram_rd_en;
  wire wr_clk;

  FPGAtoFTDI_fifo_blk_mem_gen_generic_cstr \valid.cstr 
       (.AR(AR),
        .E(E),
        .din(din),
        .dout(dout),
        .\gc0.count_d1_reg[10] (\gc0.count_d1_reg[10] ),
        .\gic0.gc0.count_d2_reg[9] (\gic0.gc0.count_d2_reg[9] ),
        .rd_clk(rd_clk),
        .tmp_ram_rd_en(tmp_ram_rd_en),
        .wr_clk(wr_clk));
endmodule

(* ORIG_REF_NAME = "blk_mem_gen_v8_4_1" *) 
module FPGAtoFTDI_fifo_blk_mem_gen_v8_4_1
   (dout,
    wr_clk,
    rd_clk,
    E,
    tmp_ram_rd_en,
    AR,
    \gic0.gc0.count_d2_reg[9] ,
    \gc0.count_d1_reg[10] ,
    din);
  output [7:0]dout;
  input wr_clk;
  input rd_clk;
  input [0:0]E;
  input tmp_ram_rd_en;
  input [0:0]AR;
  input [9:0]\gic0.gc0.count_d2_reg[9] ;
  input [10:0]\gc0.count_d1_reg[10] ;
  input [15:0]din;

  wire [0:0]AR;
  wire [0:0]E;
  wire [15:0]din;
  wire [7:0]dout;
  wire [10:0]\gc0.count_d1_reg[10] ;
  wire [9:0]\gic0.gc0.count_d2_reg[9] ;
  wire rd_clk;
  wire tmp_ram_rd_en;
  wire wr_clk;

  FPGAtoFTDI_fifo_blk_mem_gen_v8_4_1_synth inst_blk_mem_gen
       (.AR(AR),
        .E(E),
        .din(din),
        .dout(dout),
        .\gc0.count_d1_reg[10] (\gc0.count_d1_reg[10] ),
        .\gic0.gc0.count_d2_reg[9] (\gic0.gc0.count_d2_reg[9] ),
        .rd_clk(rd_clk),
        .tmp_ram_rd_en(tmp_ram_rd_en),
        .wr_clk(wr_clk));
endmodule

(* ORIG_REF_NAME = "blk_mem_gen_v8_4_1_synth" *) 
module FPGAtoFTDI_fifo_blk_mem_gen_v8_4_1_synth
   (dout,
    wr_clk,
    rd_clk,
    E,
    tmp_ram_rd_en,
    AR,
    \gic0.gc0.count_d2_reg[9] ,
    \gc0.count_d1_reg[10] ,
    din);
  output [7:0]dout;
  input wr_clk;
  input rd_clk;
  input [0:0]E;
  input tmp_ram_rd_en;
  input [0:0]AR;
  input [9:0]\gic0.gc0.count_d2_reg[9] ;
  input [10:0]\gc0.count_d1_reg[10] ;
  input [15:0]din;

  wire [0:0]AR;
  wire [0:0]E;
  wire [15:0]din;
  wire [7:0]dout;
  wire [10:0]\gc0.count_d1_reg[10] ;
  wire [9:0]\gic0.gc0.count_d2_reg[9] ;
  wire rd_clk;
  wire tmp_ram_rd_en;
  wire wr_clk;

  FPGAtoFTDI_fifo_blk_mem_gen_top \gnbram.gnativebmg.native_blk_mem_gen 
       (.AR(AR),
        .E(E),
        .din(din),
        .dout(dout),
        .\gc0.count_d1_reg[10] (\gc0.count_d1_reg[10] ),
        .\gic0.gc0.count_d2_reg[9] (\gic0.gc0.count_d2_reg[9] ),
        .rd_clk(rd_clk),
        .tmp_ram_rd_en(tmp_ram_rd_en),
        .wr_clk(wr_clk));
endmodule

(* ORIG_REF_NAME = "clk_x_pntrs" *) 
module FPGAtoFTDI_fifo_clk_x_pntrs
   (v1_reg,
    v1_reg_0,
    v1_reg_1,
    WR_PNTR_RD,
    v1_reg_2,
    Q,
    \gic0.gc0.count_reg[9] ,
    \gc0.count_d1_reg[10] ,
    \gc0.count_reg[10] ,
    wr_clk,
    \gic0.gc0.count_d2_reg[9] ,
    rd_clk);
  output [4:0]v1_reg;
  output [4:0]v1_reg_0;
  output [0:0]v1_reg_1;
  output [8:0]WR_PNTR_RD;
  output [0:0]v1_reg_2;
  input [9:0]Q;
  input [9:0]\gic0.gc0.count_reg[9] ;
  input [10:0]\gc0.count_d1_reg[10] ;
  input [0:0]\gc0.count_reg[10] ;
  input wr_clk;
  input [9:0]\gic0.gc0.count_d2_reg[9] ;
  input rd_clk;

  wire [9:0]Q;
  wire [8:0]WR_PNTR_RD;
  wire [10:0]\gc0.count_d1_reg[10] ;
  wire [0:0]\gc0.count_reg[10] ;
  wire [9:0]\gic0.gc0.count_d2_reg[9] ;
  wire [9:0]\gic0.gc0.count_reg[9] ;
  wire [9:9]p_24_out;
  wire [10:0]p_25_out;
  wire rd_clk;
  wire [4:0]v1_reg;
  wire [4:0]v1_reg_0;
  wire [0:0]v1_reg_1;
  wire [0:0]v1_reg_2;
  wire wr_clk;

  LUT4 #(
    .INIT(16'h9009)) 
    \gmux.gm[0].gm1.m1_i_1 
       (.I0(p_25_out[1]),
        .I1(Q[0]),
        .I2(p_25_out[2]),
        .I3(Q[1]),
        .O(v1_reg[0]));
  LUT4 #(
    .INIT(16'h9009)) 
    \gmux.gm[0].gm1.m1_i_1__0 
       (.I0(p_25_out[1]),
        .I1(\gic0.gc0.count_reg[9] [0]),
        .I2(p_25_out[2]),
        .I3(\gic0.gc0.count_reg[9] [1]),
        .O(v1_reg_0[0]));
  LUT4 #(
    .INIT(16'h9009)) 
    \gmux.gm[1].gms.ms_i_1 
       (.I0(p_25_out[3]),
        .I1(Q[2]),
        .I2(p_25_out[4]),
        .I3(Q[3]),
        .O(v1_reg[1]));
  LUT4 #(
    .INIT(16'h9009)) 
    \gmux.gm[1].gms.ms_i_1__0 
       (.I0(p_25_out[3]),
        .I1(\gic0.gc0.count_reg[9] [2]),
        .I2(p_25_out[4]),
        .I3(\gic0.gc0.count_reg[9] [3]),
        .O(v1_reg_0[1]));
  LUT4 #(
    .INIT(16'h9009)) 
    \gmux.gm[2].gms.ms_i_1 
       (.I0(p_25_out[5]),
        .I1(Q[4]),
        .I2(p_25_out[6]),
        .I3(Q[5]),
        .O(v1_reg[2]));
  LUT4 #(
    .INIT(16'h9009)) 
    \gmux.gm[2].gms.ms_i_1__0 
       (.I0(p_25_out[5]),
        .I1(\gic0.gc0.count_reg[9] [4]),
        .I2(p_25_out[6]),
        .I3(\gic0.gc0.count_reg[9] [5]),
        .O(v1_reg_0[2]));
  LUT4 #(
    .INIT(16'h9009)) 
    \gmux.gm[3].gms.ms_i_1 
       (.I0(p_25_out[7]),
        .I1(Q[6]),
        .I2(p_25_out[8]),
        .I3(Q[7]),
        .O(v1_reg[3]));
  LUT4 #(
    .INIT(16'h9009)) 
    \gmux.gm[3].gms.ms_i_1__0 
       (.I0(p_25_out[7]),
        .I1(\gic0.gc0.count_reg[9] [6]),
        .I2(p_25_out[8]),
        .I3(\gic0.gc0.count_reg[9] [7]),
        .O(v1_reg_0[3]));
  LUT4 #(
    .INIT(16'h9009)) 
    \gmux.gm[4].gms.ms_i_1 
       (.I0(p_25_out[9]),
        .I1(Q[8]),
        .I2(p_25_out[10]),
        .I3(Q[9]),
        .O(v1_reg[4]));
  LUT4 #(
    .INIT(16'h9009)) 
    \gmux.gm[4].gms.ms_i_1__0 
       (.I0(p_25_out[9]),
        .I1(\gic0.gc0.count_reg[9] [8]),
        .I2(p_25_out[10]),
        .I3(\gic0.gc0.count_reg[9] [9]),
        .O(v1_reg_0[4]));
  LUT2 #(
    .INIT(4'h9)) 
    \gmux.gm[5].gms.ms_i_1 
       (.I0(p_24_out),
        .I1(\gc0.count_d1_reg[10] [10]),
        .O(v1_reg_1));
  LUT2 #(
    .INIT(4'h9)) 
    \gmux.gm[5].gms.ms_i_1__0 
       (.I0(p_24_out),
        .I1(\gc0.count_reg[10] ),
        .O(v1_reg_2));
  (* DEST_SYNC_FF = "2" *) 
  (* INIT_SYNC_FF = "0" *) 
  (* REG_OUTPUT = "1" *) 
  (* SIM_ASSERT_CHK = "0" *) 
  (* SIM_LOSSLESS_GRAY_CHK = "0" *) 
  (* VERSION = "0" *) 
  (* WIDTH = "11" *) 
  (* XPM_CDC = "GRAY" *) 
  (* XPM_MODULE = "TRUE" *) 
  FPGAtoFTDI_fifo_xpm_cdc_gray__parameterized0 rd_pntr_cdc_inst
       (.dest_clk(wr_clk),
        .dest_out_bin(p_25_out),
        .src_clk(rd_clk),
        .src_in_bin(\gc0.count_d1_reg[10] ));
  (* DEST_SYNC_FF = "2" *) 
  (* INIT_SYNC_FF = "0" *) 
  (* REG_OUTPUT = "1" *) 
  (* SIM_ASSERT_CHK = "0" *) 
  (* SIM_LOSSLESS_GRAY_CHK = "0" *) 
  (* VERSION = "0" *) 
  (* WIDTH = "10" *) 
  (* XPM_CDC = "GRAY" *) 
  (* XPM_MODULE = "TRUE" *) 
  FPGAtoFTDI_fifo_xpm_cdc_gray wr_pntr_cdc_inst
       (.dest_clk(rd_clk),
        .dest_out_bin({p_24_out,WR_PNTR_RD}),
        .src_clk(wr_clk),
        .src_in_bin(\gic0.gc0.count_d2_reg[9] ));
endmodule

(* ORIG_REF_NAME = "compare" *) 
module FPGAtoFTDI_fifo_compare
   (ram_empty_fb_i_reg,
    v1_reg,
    \dest_out_bin_ff_reg[9] ,
    rd_en,
    out,
    comp1);
  output ram_empty_fb_i_reg;
  input [4:0]v1_reg;
  input [0:0]\dest_out_bin_ff_reg[9] ;
  input rd_en;
  input out;
  input comp1;

  wire carrynet_0;
  wire carrynet_1;
  wire carrynet_2;
  wire carrynet_3;
  wire carrynet_4;
  wire comp0;
  wire comp1;
  wire [0:0]\dest_out_bin_ff_reg[9] ;
  wire out;
  wire ram_empty_fb_i_reg;
  wire rd_en;
  wire [4:0]v1_reg;
  wire [3:0]\NLW_gmux.gm[0].gm1.m1_CARRY4_O_UNCONNECTED ;
  wire [3:2]\NLW_gmux.gm[4].gms.ms_CARRY4_CO_UNCONNECTED ;
  wire [3:2]\NLW_gmux.gm[4].gms.ms_CARRY4_DI_UNCONNECTED ;
  wire [3:0]\NLW_gmux.gm[4].gms.ms_CARRY4_O_UNCONNECTED ;
  wire [3:2]\NLW_gmux.gm[4].gms.ms_CARRY4_S_UNCONNECTED ;

  (* XILINX_LEGACY_PRIM = "(MUXCY,XORCY)" *) 
  (* box_type = "PRIMITIVE" *) 
  CARRY4 \gmux.gm[0].gm1.m1_CARRY4 
       (.CI(1'b0),
        .CO({carrynet_3,carrynet_2,carrynet_1,carrynet_0}),
        .CYINIT(1'b1),
        .DI({1'b0,1'b0,1'b0,1'b0}),
        .O(\NLW_gmux.gm[0].gm1.m1_CARRY4_O_UNCONNECTED [3:0]),
        .S(v1_reg[3:0]));
  (* XILINX_LEGACY_PRIM = "(MUXCY,XORCY)" *) 
  (* box_type = "PRIMITIVE" *) 
  CARRY4 \gmux.gm[4].gms.ms_CARRY4 
       (.CI(carrynet_3),
        .CO({\NLW_gmux.gm[4].gms.ms_CARRY4_CO_UNCONNECTED [3:2],comp0,carrynet_4}),
        .CYINIT(1'b0),
        .DI({\NLW_gmux.gm[4].gms.ms_CARRY4_DI_UNCONNECTED [3:2],1'b0,1'b0}),
        .O(\NLW_gmux.gm[4].gms.ms_CARRY4_O_UNCONNECTED [3:0]),
        .S({\NLW_gmux.gm[4].gms.ms_CARRY4_S_UNCONNECTED [3:2],\dest_out_bin_ff_reg[9] ,v1_reg[4]}));
  LUT4 #(
    .INIT(16'hAEAA)) 
    ram_empty_i_i_1
       (.I0(comp0),
        .I1(rd_en),
        .I2(out),
        .I3(comp1),
        .O(ram_empty_fb_i_reg));
endmodule

(* ORIG_REF_NAME = "compare" *) 
module FPGAtoFTDI_fifo_compare_1
   (comp1,
    v1_reg_0,
    \dest_out_bin_ff_reg[9] );
  output comp1;
  input [4:0]v1_reg_0;
  input [0:0]\dest_out_bin_ff_reg[9] ;

  wire carrynet_0;
  wire carrynet_1;
  wire carrynet_2;
  wire carrynet_3;
  wire carrynet_4;
  wire comp1;
  wire [0:0]\dest_out_bin_ff_reg[9] ;
  wire [4:0]v1_reg_0;
  wire [3:0]\NLW_gmux.gm[0].gm1.m1_CARRY4_O_UNCONNECTED ;
  wire [3:2]\NLW_gmux.gm[4].gms.ms_CARRY4_CO_UNCONNECTED ;
  wire [3:2]\NLW_gmux.gm[4].gms.ms_CARRY4_DI_UNCONNECTED ;
  wire [3:0]\NLW_gmux.gm[4].gms.ms_CARRY4_O_UNCONNECTED ;
  wire [3:2]\NLW_gmux.gm[4].gms.ms_CARRY4_S_UNCONNECTED ;

  (* XILINX_LEGACY_PRIM = "(MUXCY,XORCY)" *) 
  (* box_type = "PRIMITIVE" *) 
  CARRY4 \gmux.gm[0].gm1.m1_CARRY4 
       (.CI(1'b0),
        .CO({carrynet_3,carrynet_2,carrynet_1,carrynet_0}),
        .CYINIT(1'b1),
        .DI({1'b0,1'b0,1'b0,1'b0}),
        .O(\NLW_gmux.gm[0].gm1.m1_CARRY4_O_UNCONNECTED [3:0]),
        .S(v1_reg_0[3:0]));
  (* XILINX_LEGACY_PRIM = "(MUXCY,XORCY)" *) 
  (* box_type = "PRIMITIVE" *) 
  CARRY4 \gmux.gm[4].gms.ms_CARRY4 
       (.CI(carrynet_3),
        .CO({\NLW_gmux.gm[4].gms.ms_CARRY4_CO_UNCONNECTED [3:2],comp1,carrynet_4}),
        .CYINIT(1'b0),
        .DI({\NLW_gmux.gm[4].gms.ms_CARRY4_DI_UNCONNECTED [3:2],1'b0,1'b0}),
        .O(\NLW_gmux.gm[4].gms.ms_CARRY4_O_UNCONNECTED [3:0]),
        .S({\NLW_gmux.gm[4].gms.ms_CARRY4_S_UNCONNECTED [3:2],\dest_out_bin_ff_reg[9] ,v1_reg_0[4]}));
endmodule

(* ORIG_REF_NAME = "compare" *) 
module FPGAtoFTDI_fifo_compare__parameterized0
   (comp1,
    v1_reg);
  output comp1;
  input [4:0]v1_reg;

  wire carrynet_0;
  wire carrynet_1;
  wire carrynet_2;
  wire carrynet_3;
  wire comp1;
  wire [4:0]v1_reg;
  wire [3:0]\NLW_gmux.gm[0].gm1.m1_CARRY4_O_UNCONNECTED ;
  wire [3:1]\NLW_gmux.gm[4].gms.ms_CARRY4_CO_UNCONNECTED ;
  wire [3:1]\NLW_gmux.gm[4].gms.ms_CARRY4_DI_UNCONNECTED ;
  wire [3:0]\NLW_gmux.gm[4].gms.ms_CARRY4_O_UNCONNECTED ;
  wire [3:1]\NLW_gmux.gm[4].gms.ms_CARRY4_S_UNCONNECTED ;

  (* XILINX_LEGACY_PRIM = "(MUXCY,XORCY)" *) 
  (* box_type = "PRIMITIVE" *) 
  CARRY4 \gmux.gm[0].gm1.m1_CARRY4 
       (.CI(1'b0),
        .CO({carrynet_3,carrynet_2,carrynet_1,carrynet_0}),
        .CYINIT(1'b1),
        .DI({1'b0,1'b0,1'b0,1'b0}),
        .O(\NLW_gmux.gm[0].gm1.m1_CARRY4_O_UNCONNECTED [3:0]),
        .S(v1_reg[3:0]));
  (* XILINX_LEGACY_PRIM = "(MUXCY,XORCY)" *) 
  (* box_type = "PRIMITIVE" *) 
  CARRY4 \gmux.gm[4].gms.ms_CARRY4 
       (.CI(carrynet_3),
        .CO({\NLW_gmux.gm[4].gms.ms_CARRY4_CO_UNCONNECTED [3:1],comp1}),
        .CYINIT(1'b0),
        .DI({\NLW_gmux.gm[4].gms.ms_CARRY4_DI_UNCONNECTED [3:1],1'b0}),
        .O(\NLW_gmux.gm[4].gms.ms_CARRY4_O_UNCONNECTED [3:0]),
        .S({\NLW_gmux.gm[4].gms.ms_CARRY4_S_UNCONNECTED [3:1],v1_reg[4]}));
endmodule

(* ORIG_REF_NAME = "compare" *) 
module FPGAtoFTDI_fifo_compare__parameterized0_0
   (ram_full_fb_i_reg,
    v1_reg_0,
    out,
    wr_en,
    comp1,
    \grstd1.grst_full.grst_f.rst_d3_reg );
  output ram_full_fb_i_reg;
  input [4:0]v1_reg_0;
  input out;
  input wr_en;
  input comp1;
  input \grstd1.grst_full.grst_f.rst_d3_reg ;

  wire carrynet_0;
  wire carrynet_1;
  wire carrynet_2;
  wire carrynet_3;
  wire comp1;
  wire comp2;
  wire \grstd1.grst_full.grst_f.rst_d3_reg ;
  wire out;
  wire ram_full_fb_i_reg;
  wire [4:0]v1_reg_0;
  wire wr_en;
  wire [3:0]\NLW_gmux.gm[0].gm1.m1_CARRY4_O_UNCONNECTED ;
  wire [3:1]\NLW_gmux.gm[4].gms.ms_CARRY4_CO_UNCONNECTED ;
  wire [3:1]\NLW_gmux.gm[4].gms.ms_CARRY4_DI_UNCONNECTED ;
  wire [3:0]\NLW_gmux.gm[4].gms.ms_CARRY4_O_UNCONNECTED ;
  wire [3:1]\NLW_gmux.gm[4].gms.ms_CARRY4_S_UNCONNECTED ;

  (* XILINX_LEGACY_PRIM = "(MUXCY,XORCY)" *) 
  (* box_type = "PRIMITIVE" *) 
  CARRY4 \gmux.gm[0].gm1.m1_CARRY4 
       (.CI(1'b0),
        .CO({carrynet_3,carrynet_2,carrynet_1,carrynet_0}),
        .CYINIT(1'b1),
        .DI({1'b0,1'b0,1'b0,1'b0}),
        .O(\NLW_gmux.gm[0].gm1.m1_CARRY4_O_UNCONNECTED [3:0]),
        .S(v1_reg_0[3:0]));
  (* XILINX_LEGACY_PRIM = "(MUXCY,XORCY)" *) 
  (* box_type = "PRIMITIVE" *) 
  CARRY4 \gmux.gm[4].gms.ms_CARRY4 
       (.CI(carrynet_3),
        .CO({\NLW_gmux.gm[4].gms.ms_CARRY4_CO_UNCONNECTED [3:1],comp2}),
        .CYINIT(1'b0),
        .DI({\NLW_gmux.gm[4].gms.ms_CARRY4_DI_UNCONNECTED [3:1],1'b0}),
        .O(\NLW_gmux.gm[4].gms.ms_CARRY4_O_UNCONNECTED [3:0]),
        .S({\NLW_gmux.gm[4].gms.ms_CARRY4_S_UNCONNECTED [3:1],v1_reg_0[4]}));
  LUT5 #(
    .INIT(32'h0000FF20)) 
    ram_full_i_i_1
       (.I0(comp2),
        .I1(out),
        .I2(wr_en),
        .I3(comp1),
        .I4(\grstd1.grst_full.grst_f.rst_d3_reg ),
        .O(ram_full_fb_i_reg));
endmodule

(* ORIG_REF_NAME = "fifo_generator_ramfifo" *) 
module FPGAtoFTDI_fifo_fifo_generator_ramfifo
   (wr_rst_busy,
    AR,
    dout,
    empty,
    full,
    rst,
    wr_clk,
    rd_clk,
    din,
    wr_en,
    rd_en);
  output wr_rst_busy;
  output [0:0]AR;
  output [7:0]dout;
  output empty;
  output full;
  input rst;
  input wr_clk;
  input rd_clk;
  input [15:0]din;
  input wr_en;
  input rd_en;

  wire [0:0]AR;
  wire [15:0]din;
  wire [7:0]dout;
  wire empty;
  wire full;
  wire [5:5]\gras.rsts/c0/v1_reg ;
  wire [5:5]\gras.rsts/c1/v1_reg ;
  wire [4:0]\gwas.wsts/c1/v1_reg ;
  wire [4:0]\gwas.wsts/c2/v1_reg ;
  wire [10:0]p_0_out;
  wire [9:0]p_13_out;
  wire [9:0]p_14_out;
  wire p_20_out;
  wire [8:0]p_24_out;
  wire rd_clk;
  wire rd_en;
  wire [10:10]rd_pntr_plus1;
  wire rst;
  wire rst_full_ff_i;
  wire rst_full_gen_i;
  wire rstblk_n_0;
  wire tmp_ram_rd_en;
  wire wr_clk;
  wire wr_en;
  wire [9:0]wr_pntr_plus2;
  wire wr_rst_busy;

  FPGAtoFTDI_fifo_clk_x_pntrs \gntv_or_sync_fifo.gcx.clkx 
       (.Q(p_14_out),
        .WR_PNTR_RD(p_24_out),
        .\gc0.count_d1_reg[10] (p_0_out),
        .\gc0.count_reg[10] (rd_pntr_plus1),
        .\gic0.gc0.count_d2_reg[9] (p_13_out),
        .\gic0.gc0.count_reg[9] (wr_pntr_plus2),
        .rd_clk(rd_clk),
        .v1_reg(\gwas.wsts/c1/v1_reg ),
        .v1_reg_0(\gwas.wsts/c2/v1_reg ),
        .v1_reg_1(\gras.rsts/c0/v1_reg ),
        .v1_reg_2(\gras.rsts/c1/v1_reg ),
        .wr_clk(wr_clk));
  FPGAtoFTDI_fifo_rd_logic \gntv_or_sync_fifo.gl0.rd 
       (.AR(AR),
        .\DEVICE_7SERIES.NO_BMM_INFO.SDP.SIMPLE_PRIM18.ram (p_0_out),
        .Q(rd_pntr_plus1),
        .WR_PNTR_RD(p_24_out),
        .\dest_out_bin_ff_reg[9] (\gras.rsts/c0/v1_reg ),
        .\dest_out_bin_ff_reg[9]_0 (\gras.rsts/c1/v1_reg ),
        .empty(empty),
        .rd_clk(rd_clk),
        .rd_en(rd_en),
        .tmp_ram_rd_en(tmp_ram_rd_en));
  FPGAtoFTDI_fifo_wr_logic \gntv_or_sync_fifo.gl0.wr 
       (.AR(rstblk_n_0),
        .\DEVICE_7SERIES.NO_BMM_INFO.SDP.SIMPLE_PRIM18.ram (p_13_out),
        .E(p_20_out),
        .Q(wr_pntr_plus2),
        .full(full),
        .\gic0.gc0.count_d2_reg[9] (p_14_out),
        .\grstd1.grst_full.grst_f.rst_d3_reg (rst_full_gen_i),
        .out(rst_full_ff_i),
        .v1_reg(\gwas.wsts/c1/v1_reg ),
        .v1_reg_0(\gwas.wsts/c2/v1_reg ),
        .wr_clk(wr_clk),
        .wr_en(wr_en));
  FPGAtoFTDI_fifo_memory \gntv_or_sync_fifo.mem 
       (.AR(AR),
        .E(p_20_out),
        .din(din),
        .dout(dout),
        .\gc0.count_d1_reg[10] (p_0_out),
        .\gic0.gc0.count_d2_reg[9] (p_13_out),
        .rd_clk(rd_clk),
        .tmp_ram_rd_en(tmp_ram_rd_en),
        .wr_clk(wr_clk));
  FPGAtoFTDI_fifo_reset_blk_ramfifo rstblk
       (.AR(rstblk_n_0),
        .out(rst_full_ff_i),
        .ram_full_fb_i_reg(rst_full_gen_i),
        .rd_clk(rd_clk),
        .rst(rst),
        .\syncstages_ff_reg[0] (AR),
        .wr_clk(wr_clk),
        .wr_rst_busy(wr_rst_busy));
endmodule

(* ORIG_REF_NAME = "fifo_generator_top" *) 
module FPGAtoFTDI_fifo_fifo_generator_top
   (wr_rst_busy,
    AR,
    dout,
    empty,
    full,
    rst,
    wr_clk,
    rd_clk,
    din,
    wr_en,
    rd_en);
  output wr_rst_busy;
  output [0:0]AR;
  output [7:0]dout;
  output empty;
  output full;
  input rst;
  input wr_clk;
  input rd_clk;
  input [15:0]din;
  input wr_en;
  input rd_en;

  wire [0:0]AR;
  wire [15:0]din;
  wire [7:0]dout;
  wire empty;
  wire full;
  wire rd_clk;
  wire rd_en;
  wire rst;
  wire wr_clk;
  wire wr_en;
  wire wr_rst_busy;

  FPGAtoFTDI_fifo_fifo_generator_ramfifo \grf.rf 
       (.AR(AR),
        .din(din),
        .dout(dout),
        .empty(empty),
        .full(full),
        .rd_clk(rd_clk),
        .rd_en(rd_en),
        .rst(rst),
        .wr_clk(wr_clk),
        .wr_en(wr_en),
        .wr_rst_busy(wr_rst_busy));
endmodule
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
