mfkiwl/SDR-R/fpga-src/sources_1/ip/FPGAtoFTDI_fifo/FPGAtoFTDI_fifo_sim_netlist.vhdl

-- Copyright 1986-2018 Xilinx, Inc. All Rights Reserved.
-- --------------------------------------------------------------------------------
-- Tool Version: Vivado v.2018.2.2 (win64) Build 2348494 Mon Oct  1 18:25:44 MDT 2018
-- Date        : Thu May 16 00:08:55 2019
-- Host        : DESKTOP-4O36AQC running 64-bit major release  (build 9200)
-- Command     : write_vhdl -force -mode funcsim
--               C:/Users/Guy/Desktop/UMBC/2019_Spring/451/SDRR_FINAL/SDRR_FINAL.srcs/sources_1/ip/FPGAtoFTDI_fifo/FPGAtoFTDI_fifo_sim_netlist.vhdl
-- Design      : FPGAtoFTDI_fifo
-- Purpose     : This VHDL netlist is a functional simulation representation of the design and should not be modified or
--               synthesized. This netlist cannot be used for SDF annotated simulation.
-- Device      : xc7a15tcpg236-1
-- --------------------------------------------------------------------------------
library IEEE;
use IEEE.STD_LOGIC_1164.ALL;
library UNISIM;
use UNISIM.VCOMPONENTS.ALL;
entity FPGAtoFTDI_fifo_xpm_cdc_async_rst is
  port (
    src_arst : in STD_LOGIC;
    dest_clk : in STD_LOGIC;
    dest_arst : out STD_LOGIC
  );
  attribute DEF_VAL : string;
  attribute DEF_VAL of FPGAtoFTDI_fifo_xpm_cdc_async_rst : entity is "1'b0";
  attribute DEST_SYNC_FF : integer;
  attribute DEST_SYNC_FF of FPGAtoFTDI_fifo_xpm_cdc_async_rst : entity is 2;
  attribute INIT_SYNC_FF : integer;
  attribute INIT_SYNC_FF of FPGAtoFTDI_fifo_xpm_cdc_async_rst : entity is 0;
  attribute INV_DEF_VAL : string;
  attribute INV_DEF_VAL of FPGAtoFTDI_fifo_xpm_cdc_async_rst : entity is "1'b1";
  attribute ORIG_REF_NAME : string;
  attribute ORIG_REF_NAME of FPGAtoFTDI_fifo_xpm_cdc_async_rst : entity is "xpm_cdc_async_rst";
  attribute RST_ACTIVE_HIGH : integer;
  attribute RST_ACTIVE_HIGH of FPGAtoFTDI_fifo_xpm_cdc_async_rst : entity is 1;
  attribute VERSION : integer;
  attribute VERSION of FPGAtoFTDI_fifo_xpm_cdc_async_rst : entity is 0;
  attribute XPM_MODULE : string;
  attribute XPM_MODULE of FPGAtoFTDI_fifo_xpm_cdc_async_rst : entity is "TRUE";
  attribute xpm_cdc : string;
  attribute xpm_cdc of FPGAtoFTDI_fifo_xpm_cdc_async_rst : entity is "ASYNC_RST";
end FPGAtoFTDI_fifo_xpm_cdc_async_rst;

architecture STRUCTURE of FPGAtoFTDI_fifo_xpm_cdc_async_rst is
  signal arststages_ff : STD_LOGIC_VECTOR ( 1 downto 0 );
  attribute RTL_KEEP : string;
  attribute RTL_KEEP of arststages_ff : signal is "true";
  attribute async_reg : string;
  attribute async_reg of arststages_ff : signal is "true";
  attribute xpm_cdc of arststages_ff : signal is "ASYNC_RST";
  attribute ASYNC_REG_boolean : boolean;
  attribute ASYNC_REG_boolean of \arststages_ff_reg[0]\ : label is std.standard.true;
  attribute KEEP : string;
  attribute KEEP of \arststages_ff_reg[0]\ : label is "true";
  attribute XPM_CDC of \arststages_ff_reg[0]\ : label is "ASYNC_RST";
  attribute ASYNC_REG_boolean of \arststages_ff_reg[1]\ : label is std.standard.true;
  attribute KEEP of \arststages_ff_reg[1]\ : label is "true";
  attribute XPM_CDC of \arststages_ff_reg[1]\ : label is "ASYNC_RST";
begin
  dest_arst <= arststages_ff(1);
\arststages_ff_reg[0]\: unisim.vcomponents.FDPE
    generic map(
      INIT => '0'
    )
        port map (
      C => dest_clk,
      CE => '1',
      D => '0',
      PRE => src_arst,
      Q => arststages_ff(0)
    );
\arststages_ff_reg[1]\: unisim.vcomponents.FDPE
    generic map(
      INIT => '0'
    )
        port map (
      C => dest_clk,
      CE => '1',
      D => arststages_ff(0),
      PRE => src_arst,
      Q => arststages_ff(1)
    );
end STRUCTURE;
library IEEE;
use IEEE.STD_LOGIC_1164.ALL;
library UNISIM;
use UNISIM.VCOMPONENTS.ALL;
entity \FPGAtoFTDI_fifo_xpm_cdc_async_rst__1\ is
  port (
    src_arst : in STD_LOGIC;
    dest_clk : in STD_LOGIC;
    dest_arst : out STD_LOGIC
  );
  attribute DEF_VAL : string;
  attribute DEF_VAL of \FPGAtoFTDI_fifo_xpm_cdc_async_rst__1\ : entity is "1'b0";
  attribute DEST_SYNC_FF : integer;
  attribute DEST_SYNC_FF of \FPGAtoFTDI_fifo_xpm_cdc_async_rst__1\ : entity is 2;
  attribute INIT_SYNC_FF : integer;
  attribute INIT_SYNC_FF of \FPGAtoFTDI_fifo_xpm_cdc_async_rst__1\ : entity is 0;
  attribute INV_DEF_VAL : string;
  attribute INV_DEF_VAL of \FPGAtoFTDI_fifo_xpm_cdc_async_rst__1\ : entity is "1'b1";
  attribute ORIG_REF_NAME : string;
  attribute ORIG_REF_NAME of \FPGAtoFTDI_fifo_xpm_cdc_async_rst__1\ : entity is "xpm_cdc_async_rst";
  attribute RST_ACTIVE_HIGH : integer;
  attribute RST_ACTIVE_HIGH of \FPGAtoFTDI_fifo_xpm_cdc_async_rst__1\ : entity is 1;
  attribute VERSION : integer;
  attribute VERSION of \FPGAtoFTDI_fifo_xpm_cdc_async_rst__1\ : entity is 0;
  attribute XPM_MODULE : string;
  attribute XPM_MODULE of \FPGAtoFTDI_fifo_xpm_cdc_async_rst__1\ : entity is "TRUE";
  attribute xpm_cdc : string;
  attribute xpm_cdc of \FPGAtoFTDI_fifo_xpm_cdc_async_rst__1\ : entity is "ASYNC_RST";
end \FPGAtoFTDI_fifo_xpm_cdc_async_rst__1\;

architecture STRUCTURE of \FPGAtoFTDI_fifo_xpm_cdc_async_rst__1\ is
  signal arststages_ff : STD_LOGIC_VECTOR ( 1 downto 0 );
  attribute RTL_KEEP : string;
  attribute RTL_KEEP of arststages_ff : signal is "true";
  attribute async_reg : string;
  attribute async_reg of arststages_ff : signal is "true";
  attribute xpm_cdc of arststages_ff : signal is "ASYNC_RST";
  attribute ASYNC_REG_boolean : boolean;
  attribute ASYNC_REG_boolean of \arststages_ff_reg[0]\ : label is std.standard.true;
  attribute KEEP : string;
  attribute KEEP of \arststages_ff_reg[0]\ : label is "true";
  attribute XPM_CDC of \arststages_ff_reg[0]\ : label is "ASYNC_RST";
  attribute ASYNC_REG_boolean of \arststages_ff_reg[1]\ : label is std.standard.true;
  attribute KEEP of \arststages_ff_reg[1]\ : label is "true";
  attribute XPM_CDC of \arststages_ff_reg[1]\ : label is "ASYNC_RST";
begin
  dest_arst <= arststages_ff(1);
\arststages_ff_reg[0]\: unisim.vcomponents.FDPE
    generic map(
      INIT => '0'
    )
        port map (
      C => dest_clk,
      CE => '1',
      D => '0',
      PRE => src_arst,
      Q => arststages_ff(0)
    );
\arststages_ff_reg[1]\: unisim.vcomponents.FDPE
    generic map(
      INIT => '0'
    )
        port map (
      C => dest_clk,
      CE => '1',
      D => arststages_ff(0),
      PRE => src_arst,
      Q => arststages_ff(1)
    );
end STRUCTURE;
library IEEE;
use IEEE.STD_LOGIC_1164.ALL;
library UNISIM;
use UNISIM.VCOMPONENTS.ALL;
entity FPGAtoFTDI_fifo_xpm_cdc_gray is
  port (
    src_clk : in STD_LOGIC;
    src_in_bin : in STD_LOGIC_VECTOR ( 9 downto 0 );
    dest_clk : in STD_LOGIC;
    dest_out_bin : out STD_LOGIC_VECTOR ( 9 downto 0 )
  );
  attribute DEST_SYNC_FF : integer;
  attribute DEST_SYNC_FF of FPGAtoFTDI_fifo_xpm_cdc_gray : entity is 2;
  attribute INIT_SYNC_FF : integer;
  attribute INIT_SYNC_FF of FPGAtoFTDI_fifo_xpm_cdc_gray : entity is 0;
  attribute ORIG_REF_NAME : string;
  attribute ORIG_REF_NAME of FPGAtoFTDI_fifo_xpm_cdc_gray : entity is "xpm_cdc_gray";
  attribute REG_OUTPUT : integer;
  attribute REG_OUTPUT of FPGAtoFTDI_fifo_xpm_cdc_gray : entity is 1;
  attribute SIM_ASSERT_CHK : integer;
  attribute SIM_ASSERT_CHK of FPGAtoFTDI_fifo_xpm_cdc_gray : entity is 0;
  attribute SIM_LOSSLESS_GRAY_CHK : integer;
  attribute SIM_LOSSLESS_GRAY_CHK of FPGAtoFTDI_fifo_xpm_cdc_gray : entity is 0;
  attribute VERSION : integer;
  attribute VERSION of FPGAtoFTDI_fifo_xpm_cdc_gray : entity is 0;
  attribute WIDTH : integer;
  attribute WIDTH of FPGAtoFTDI_fifo_xpm_cdc_gray : entity is 10;
  attribute XPM_MODULE : string;
  attribute XPM_MODULE of FPGAtoFTDI_fifo_xpm_cdc_gray : entity is "TRUE";
  attribute xpm_cdc : string;
  attribute xpm_cdc of FPGAtoFTDI_fifo_xpm_cdc_gray : entity is "GRAY";
end FPGAtoFTDI_fifo_xpm_cdc_gray;

architecture STRUCTURE of FPGAtoFTDI_fifo_xpm_cdc_gray is
  signal async_path : STD_LOGIC_VECTOR ( 9 downto 0 );
  signal binval : STD_LOGIC_VECTOR ( 8 downto 0 );
  signal \dest_graysync_ff[0]\ : STD_LOGIC_VECTOR ( 9 downto 0 );
  attribute RTL_KEEP : string;
  attribute RTL_KEEP of \dest_graysync_ff[0]\ : signal is "true";
  attribute async_reg : string;
  attribute async_reg of \dest_graysync_ff[0]\ : signal is "true";
  attribute xpm_cdc of \dest_graysync_ff[0]\ : signal is "GRAY";
  signal \dest_graysync_ff[1]\ : STD_LOGIC_VECTOR ( 9 downto 0 );
  attribute RTL_KEEP of \dest_graysync_ff[1]\ : signal is "true";
  attribute async_reg of \dest_graysync_ff[1]\ : signal is "true";
  attribute xpm_cdc of \dest_graysync_ff[1]\ : signal is "GRAY";
  signal gray_enc : STD_LOGIC_VECTOR ( 8 downto 0 );
  attribute ASYNC_REG_boolean : boolean;
  attribute ASYNC_REG_boolean of \dest_graysync_ff_reg[0][0]\ : label is std.standard.true;
  attribute KEEP : string;
  attribute KEEP of \dest_graysync_ff_reg[0][0]\ : label is "true";
  attribute XPM_CDC of \dest_graysync_ff_reg[0][0]\ : label is "GRAY";
  attribute ASYNC_REG_boolean of \dest_graysync_ff_reg[0][1]\ : label is std.standard.true;
  attribute KEEP of \dest_graysync_ff_reg[0][1]\ : label is "true";
  attribute XPM_CDC of \dest_graysync_ff_reg[0][1]\ : label is "GRAY";
  attribute ASYNC_REG_boolean of \dest_graysync_ff_reg[0][2]\ : label is std.standard.true;
  attribute KEEP of \dest_graysync_ff_reg[0][2]\ : label is "true";
  attribute XPM_CDC of \dest_graysync_ff_reg[0][2]\ : label is "GRAY";
  attribute ASYNC_REG_boolean of \dest_graysync_ff_reg[0][3]\ : label is std.standard.true;
  attribute KEEP of \dest_graysync_ff_reg[0][3]\ : label is "true";
  attribute XPM_CDC of \dest_graysync_ff_reg[0][3]\ : label is "GRAY";
  attribute ASYNC_REG_boolean of \dest_graysync_ff_reg[0][4]\ : label is std.standard.true;
  attribute KEEP of \dest_graysync_ff_reg[0][4]\ : label is "true";
  attribute XPM_CDC of \dest_graysync_ff_reg[0][4]\ : label is "GRAY";
  attribute ASYNC_REG_boolean of \dest_graysync_ff_reg[0][5]\ : label is std.standard.true;
  attribute KEEP of \dest_graysync_ff_reg[0][5]\ : label is "true";
  attribute XPM_CDC of \dest_graysync_ff_reg[0][5]\ : label is "GRAY";
  attribute ASYNC_REG_boolean of \dest_graysync_ff_reg[0][6]\ : label is std.standard.true;
  attribute KEEP of \dest_graysync_ff_reg[0][6]\ : label is "true";
  attribute XPM_CDC of \dest_graysync_ff_reg[0][6]\ : label is "GRAY";
  attribute ASYNC_REG_boolean of \dest_graysync_ff_reg[0][7]\ : label is std.standard.true;
  attribute KEEP of \dest_graysync_ff_reg[0][7]\ : label is "true";
  attribute XPM_CDC of \dest_graysync_ff_reg[0][7]\ : label is "GRAY";
  attribute ASYNC_REG_boolean of \dest_graysync_ff_reg[0][8]\ : label is std.standard.true;
  attribute KEEP of \dest_graysync_ff_reg[0][8]\ : label is "true";
  attribute XPM_CDC of \dest_graysync_ff_reg[0][8]\ : label is "GRAY";
  attribute ASYNC_REG_boolean of \dest_graysync_ff_reg[0][9]\ : label is std.standard.true;
  attribute KEEP of \dest_graysync_ff_reg[0][9]\ : label is "true";
  attribute XPM_CDC of \dest_graysync_ff_reg[0][9]\ : label is "GRAY";
  attribute ASYNC_REG_boolean of \dest_graysync_ff_reg[1][0]\ : label is std.standard.true;
  attribute KEEP of \dest_graysync_ff_reg[1][0]\ : label is "true";
  attribute XPM_CDC of \dest_graysync_ff_reg[1][0]\ : label is "GRAY";
  attribute ASYNC_REG_boolean of \dest_graysync_ff_reg[1][1]\ : label is std.standard.true;
  attribute KEEP of \dest_graysync_ff_reg[1][1]\ : label is "true";
  attribute XPM_CDC of \dest_graysync_ff_reg[1][1]\ : label is "GRAY";
  attribute ASYNC_REG_boolean of \dest_graysync_ff_reg[1][2]\ : label is std.standard.true;
  attribute KEEP of \dest_graysync_ff_reg[1][2]\ : label is "true";
  attribute XPM_CDC of \dest_graysync_ff_reg[1][2]\ : label is "GRAY";
  attribute ASYNC_REG_boolean of \dest_graysync_ff_reg[1][3]\ : label is std.standard.true;
  attribute KEEP of \dest_graysync_ff_reg[1][3]\ : label is "true";
  attribute XPM_CDC of \dest_graysync_ff_reg[1][3]\ : label is "GRAY";
  attribute ASYNC_REG_boolean of \dest_graysync_ff_reg[1][4]\ : label is std.standard.true;
  attribute KEEP of \dest_graysync_ff_reg[1][4]\ : label is "true";
  attribute XPM_CDC of \dest_graysync_ff_reg[1][4]\ : label is "GRAY";
  attribute ASYNC_REG_boolean of \dest_graysync_ff_reg[1][5]\ : label is std.standard.true;
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
     port map (
      C => src_clk,
      CE => '1',
      D => gray_enc(8),
      Q => async_path(8),
      R => '0'
    );
\src_gray_ff_reg[9]\: unisim.vcomponents.FDRE
     port map (
      C => src_clk,
      CE => '1',
      D => src_in_bin(9),
      Q => async_path(9),
      R => '0'
    );
end STRUCTURE;
library IEEE;
use IEEE.STD_LOGIC_1164.ALL;
library UNISIM;
use UNISIM.VCOMPONENTS.ALL;
entity \FPGAtoFTDI_fifo_xpm_cdc_gray__parameterized0\ is
  port (
    src_clk : in STD_LOGIC;
    src_in_bin : in STD_LOGIC_VECTOR ( 10 downto 0 );
    dest_clk : in STD_LOGIC;
    dest_out_bin : out STD_LOGIC_VECTOR ( 10 downto 0 )
  );
  attribute DEST_SYNC_FF : integer;
  attribute DEST_SYNC_FF of \FPGAtoFTDI_fifo_xpm_cdc_gray__parameterized0\ : entity is 2;
  attribute INIT_SYNC_FF : integer;
  attribute INIT_SYNC_FF of \FPGAtoFTDI_fifo_xpm_cdc_gray__parameterized0\ : entity is 0;
  attribute ORIG_REF_NAME : string;
  attribute ORIG_REF_NAME of \FPGAtoFTDI_fifo_xpm_cdc_gray__parameterized0\ : entity is "xpm_cdc_gray";
  attribute REG_OUTPUT : integer;
  attribute REG_OUTPUT of \FPGAtoFTDI_fifo_xpm_cdc_gray__parameterized0\ : entity is 1;
  attribute SIM_ASSERT_CHK : integer;
  attribute SIM_ASSERT_CHK of \FPGAtoFTDI_fifo_xpm_cdc_gray__parameterized0\ : entity is 0;
  attribute SIM_LOSSLESS_GRAY_CHK : integer;
  attribute SIM_LOSSLESS_GRAY_CHK of \FPGAtoFTDI_fifo_xpm_cdc_gray__parameterized0\ : entity is 0;
  attribute VERSION : integer;
  attribute VERSION of \FPGAtoFTDI_fifo_xpm_cdc_gray__parameterized0\ : entity is 0;
  attribute WIDTH : integer;
  attribute WIDTH of \FPGAtoFTDI_fifo_xpm_cdc_gray__parameterized0\ : entity is 11;
  attribute XPM_MODULE : string;
  attribute XPM_MODULE of \FPGAtoFTDI_fifo_xpm_cdc_gray__parameterized0\ : entity is "TRUE";
  attribute xpm_cdc : string;
  attribute xpm_cdc of \FPGAtoFTDI_fifo_xpm_cdc_gray__parameterized0\ : entity is "GRAY";
end \FPGAtoFTDI_fifo_xpm_cdc_gray__parameterized0\;

architecture STRUCTURE of \FPGAtoFTDI_fifo_xpm_cdc_gray__parameterized0\ is
  signal async_path : STD_LOGIC_VECTOR ( 10 downto 0 );
  signal binval : STD_LOGIC_VECTOR ( 9 downto 0 );
  signal \dest_graysync_ff[0]\ : STD_LOGIC_VECTOR ( 10 downto 0 );
  attribute RTL_KEEP : string;
  attribute RTL_KEEP of \dest_graysync_ff[0]\ : signal is "true";
  attribute async_reg : string;
  attribute async_reg of \dest_graysync_ff[0]\ : signal is "true";
  attribute xpm_cdc of \dest_graysync_ff[0]\ : signal is "GRAY";
  signal \dest_graysync_ff[1]\ : STD_LOGIC_VECTOR ( 10 downto 0 );
  attribute RTL_KEEP of \dest_graysync_ff[1]\ : signal is "true";
  attribute async_reg of \dest_graysync_ff[1]\ : signal is "true";
  attribute xpm_cdc of \dest_graysync_ff[1]\ : signal is "GRAY";
  signal gray_enc : STD_LOGIC_VECTOR ( 9 downto 0 );
  attribute ASYNC_REG_boolean : boolean;
  attribute ASYNC_REG_boolean of \dest_graysync_ff_reg[0][0]\ : label is std.standard.true;
  attribute KEEP : string;
  attribute KEEP of \dest_graysync_ff_reg[0][0]\ : label is "true";
  attribute XPM_CDC of \dest_graysync_ff_reg[0][0]\ : label is "GRAY";
  attribute ASYNC_REG_boolean of \dest_graysync_ff_reg[0][10]\ : label is std.standard.true;
  attribute KEEP of \dest_graysync_ff_reg[0][10]\ : label is "true";
  attribute XPM_CDC of \dest_graysync_ff_reg[0][10]\ : label is "GRAY";
  attribute ASYNC_REG_boolean of \dest_graysync_ff_reg[0][1]\ : label is std.standard.true;
  attribute KEEP of \dest_graysync_ff_reg[0][1]\ : label is "true";
  attribute XPM_CDC of \dest_graysync_ff_reg[0][1]\ : label is "GRAY";
  attribute ASYNC_REG_boolean of \dest_graysync_ff_reg[0][2]\ : label is std.standard.true;
  attribute KEEP of \dest_graysync_ff_reg[0][2]\ : label is "true";
  attribute XPM_CDC of \dest_graysync_ff_reg[0][2]\ : label is "GRAY";
  attribute ASYNC_REG_boolean of \dest_graysync_ff_reg[0][3]\ : label is std.standard.true;
  attribute KEEP of \dest_graysync_ff_reg[0][3]\ : label is "true";
  attribute XPM_CDC of \dest_graysync_ff_reg[0][3]\ : label is "GRAY";
  attribute ASYNC_REG_boolean of \dest_graysync_ff_reg[0][4]\ : label is std.standard.true;
  attribute KEEP of \dest_graysync_ff_reg[0][4]\ : label is "true";
  attribute XPM_CDC of \dest_graysync_ff_reg[0][4]\ : label is "GRAY";
  attribute ASYNC_REG_boolean of \dest_graysync_ff_reg[0][5]\ : label is std.standard.true;
  attribute KEEP of \dest_graysync_ff_reg[0][5]\ : label is "true";
  attribute XPM_CDC of \dest_graysync_ff_reg[0][5]\ : label is "GRAY";
  attribute ASYNC_REG_boolean of \dest_graysync_ff_reg[0][6]\ : label is std.standard.true;
  attribute KEEP of \dest_graysync_ff_reg[0][6]\ : label is "true";
  attribute XPM_CDC of \dest_graysync_ff_reg[0][6]\ : label is "GRAY";
  attribute ASYNC_REG_boolean of \dest_graysync_ff_reg[0][7]\ : label is std.standard.true;
  attribute KEEP of \dest_graysync_ff_reg[0][7]\ : label is "true";
  attribute XPM_CDC of \dest_graysync_ff_reg[0][7]\ : label is "GRAY";
  attribute ASYNC_REG_boolean of \dest_graysync_ff_reg[0][8]\ : label is std.standard.true;
  attribute KEEP of \dest_graysync_ff_reg[0][8]\ : label is "true";
  attribute XPM_CDC of \dest_graysync_ff_reg[0][8]\ : label is "GRAY";
  attribute ASYNC_REG_boolean of \dest_graysync_ff_reg[0][9]\ : label is std.standard.true;
  attribute KEEP of \dest_graysync_ff_reg[0][9]\ : label is "true";
  attribute XPM_CDC of \dest_graysync_ff_reg[0][9]\ : label is "GRAY";
  attribute ASYNC_REG_boolean of \dest_graysync_ff_reg[1][0]\ : label is std.standard.true;
  attribute KEEP of \dest_graysync_ff_reg[1][0]\ : label is "true";
  attribute XPM_CDC of \dest_graysync_ff_reg[1][0]\ : label is "GRAY";
  attribute ASYNC_REG_boolean of \dest_graysync_ff_reg[1][10]\ : label is std.standard.true;
  attribute KEEP of \dest_graysync_ff_reg[1][10]\ : label is "true";
  attribute XPM_CDC of \dest_graysync_ff_reg[1][10]\ : label is "GRAY";
  attribute ASYNC_REG_boolean of \dest_graysync_ff_reg[1][1]\ : label is std.standard.true;
  attribute KEEP of \dest_graysync_ff_reg[1][1]\ : label is "true";
  attribute XPM_CDC of \dest_graysync_ff_reg[1][1]\ : label is "GRAY";
  attribute ASYNC_REG_boolean of \dest_graysync_ff_reg[1][2]\ : label is std.standard.true;
  attribute KEEP of \dest_graysync_ff_reg[1][2]\ : label is "true";
  attribute XPM_CDC of \dest_graysync_ff_reg[1][2]\ : label is "GRAY";
  attribute ASYNC_REG_boolean of \dest_graysync_ff_reg[1][3]\ : label is std.standard.true;
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
    generic map(
      INIT => X"6"
    )
        port map (
      I0 => src_in_bin(9),
      I1 => src_in_bin(8),
      O => gray_enc(8)
    );
\src_gray_ff[9]_i_1\: unisim.vcomponents.LUT2
    generic map(
      INIT => X"6"
    )
        port map (
      I0 => src_in_bin(10),
      I1 => src_in_bin(9),
      O => gray_enc(9)
    );
\src_gray_ff_reg[0]\: unisim.vcomponents.FDRE
     port map (
      C => src_clk,
      CE => '1',
      D => gray_enc(0),
      Q => async_path(0),
      R => '0'
    );
\src_gray_ff_reg[10]\: unisim.vcomponents.FDRE
     port map (
      C => src_clk,
      CE => '1',
      D => src_in_bin(10),
      Q => async_path(10),
      R => '0'
    );
\src_gray_ff_reg[1]\: unisim.vcomponents.FDRE
     port map (
      C => src_clk,
      CE => '1',
      D => gray_enc(1),
      Q => async_path(1),
      R => '0'
    );
\src_gray_ff_reg[2]\: unisim.vcomponents.FDRE
     port map (
      C => src_clk,
      CE => '1',
      D => gray_enc(2),
      Q => async_path(2),
      R => '0'
    );
\src_gray_ff_reg[3]\: unisim.vcomponents.FDRE
     port map (
      C => src_clk,
      CE => '1',
      D => gray_enc(3),
      Q => async_path(3),
      R => '0'
    );
\src_gray_ff_reg[4]\: unisim.vcomponents.FDRE
     port map (
      C => src_clk,
      CE => '1',
      D => gray_enc(4),
      Q => async_path(4),
      R => '0'
    );
\src_gray_ff_reg[5]\: unisim.vcomponents.FDRE
     port map (
      C => src_clk,
      CE => '1',
      D => gray_enc(5),
      Q => async_path(5),
      R => '0'
    );
\src_gray_ff_reg[6]\: unisim.vcomponents.FDRE
     port map (
      C => src_clk,
      CE => '1',
      D => gray_enc(6),
      Q => async_path(6),
      R => '0'
    );
\src_gray_ff_reg[7]\: unisim.vcomponents.FDRE
     port map (
      C => src_clk,
      CE => '1',
      D => gray_enc(7),
      Q => async_path(7),
      R => '0'
    );
\src_gray_ff_reg[8]\: unisim.vcomponents.FDRE
     port map (
      C => src_clk,
      CE => '1',
      D => gray_enc(8),
      Q => async_path(8),
      R => '0'
    );
\src_gray_ff_reg[9]\: unisim.vcomponents.FDRE
     port map (
      C => src_clk,
      CE => '1',
      D => gray_enc(9),
      Q => async_path(9),
      R => '0'
    );
end STRUCTURE;
library IEEE;
use IEEE.STD_LOGIC_1164.ALL;
library UNISIM;
use UNISIM.VCOMPONENTS.ALL;
entity FPGAtoFTDI_fifo_xpm_cdc_single is
  port (
    src_clk : in STD_LOGIC;
    src_in : in STD_LOGIC;
    dest_clk : in STD_LOGIC;
    dest_out : out STD_LOGIC
  );
  attribute DEST_SYNC_FF : integer;
  attribute DEST_SYNC_FF of FPGAtoFTDI_fifo_xpm_cdc_single : entity is 4;
  attribute INIT_SYNC_FF : integer;
  attribute INIT_SYNC_FF of FPGAtoFTDI_fifo_xpm_cdc_single : entity is 0;
  attribute ORIG_REF_NAME : string;
  attribute ORIG_REF_NAME of FPGAtoFTDI_fifo_xpm_cdc_single : entity is "xpm_cdc_single";
  attribute SIM_ASSERT_CHK : integer;
  attribute SIM_ASSERT_CHK of FPGAtoFTDI_fifo_xpm_cdc_single : entity is 0;
  attribute SRC_INPUT_REG : integer;
  attribute SRC_INPUT_REG of FPGAtoFTDI_fifo_xpm_cdc_single : entity is 0;
  attribute VERSION : integer;
  attribute VERSION of FPGAtoFTDI_fifo_xpm_cdc_single : entity is 0;
  attribute XPM_MODULE : string;
  attribute XPM_MODULE of FPGAtoFTDI_fifo_xpm_cdc_single : entity is "TRUE";
  attribute xpm_cdc : string;
  attribute xpm_cdc of FPGAtoFTDI_fifo_xpm_cdc_single : entity is "SINGLE";
end FPGAtoFTDI_fifo_xpm_cdc_single;

architecture STRUCTURE of FPGAtoFTDI_fifo_xpm_cdc_single is
  signal syncstages_ff : STD_LOGIC_VECTOR ( 3 downto 0 );
  attribute RTL_KEEP : string;
  attribute RTL_KEEP of syncstages_ff : signal is "true";
  attribute async_reg : string;
  attribute async_reg of syncstages_ff : signal is "true";
  attribute xpm_cdc of syncstages_ff : signal is "SINGLE";
  attribute ASYNC_REG_boolean : boolean;
  attribute ASYNC_REG_boolean of \syncstages_ff_reg[0]\ : label is std.standard.true;
  attribute KEEP : string;
  attribute KEEP of \syncstages_ff_reg[0]\ : label is "true";
  attribute XPM_CDC of \syncstages_ff_reg[0]\ : label is "SINGLE";
  attribute ASYNC_REG_boolean of \syncstages_ff_reg[1]\ : label is std.standard.true;
  attribute KEEP of \syncstages_ff_reg[1]\ : label is "true";
  attribute XPM_CDC of \syncstages_ff_reg[1]\ : label is "SINGLE";
  attribute ASYNC_REG_boolean of \syncstages_ff_reg[2]\ : label is std.standard.true;
  attribute KEEP of \syncstages_ff_reg[2]\ : label is "true";
  attribute XPM_CDC of \syncstages_ff_reg[2]\ : label is "SINGLE";
  attribute ASYNC_REG_boolean of \syncstages_ff_reg[3]\ : label is std.standard.true;
  attribute KEEP of \syncstages_ff_reg[3]\ : label is "true";
  attribute XPM_CDC of \syncstages_ff_reg[3]\ : label is "SINGLE";
begin
  dest_out <= syncstages_ff(3);
\syncstages_ff_reg[0]\: unisim.vcomponents.FDRE
     port map (
      C => dest_clk,
      CE => '1',
      D => src_in,
      Q => syncstages_ff(0),
      R => '0'
    );
\syncstages_ff_reg[1]\: unisim.vcomponents.FDRE
     port map (
      C => dest_clk,
      CE => '1',
      D => syncstages_ff(0),
      Q => syncstages_ff(1),
      R => '0'
    );
\syncstages_ff_reg[2]\: unisim.vcomponents.FDRE
     port map (
      C => dest_clk,
      CE => '1',
      D => syncstages_ff(1),
      Q => syncstages_ff(2),
      R => '0'
    );
\syncstages_ff_reg[3]\: unisim.vcomponents.FDRE
     port map (
      C => dest_clk,
      CE => '1',
      D => syncstages_ff(2),
      Q => syncstages_ff(3),
      R => '0'
    );
end STRUCTURE;
library IEEE;
use IEEE.STD_LOGIC_1164.ALL;
library UNISIM;
use UNISIM.VCOMPONENTS.ALL;
entity \FPGAtoFTDI_fifo_xpm_cdc_single__1\ is
  port (
    src_clk : in STD_LOGIC;
    src_in : in STD_LOGIC;
    dest_clk : in STD_LOGIC;
    dest_out : out STD_LOGIC
  );
  attribute DEST_SYNC_FF : integer;
  attribute DEST_SYNC_FF of \FPGAtoFTDI_fifo_xpm_cdc_single__1\ : entity is 4;
  attribute INIT_SYNC_FF : integer;
  attribute INIT_SYNC_FF of \FPGAtoFTDI_fifo_xpm_cdc_single__1\ : entity is 0;
  attribute ORIG_REF_NAME : string;
  attribute ORIG_REF_NAME of \FPGAtoFTDI_fifo_xpm_cdc_single__1\ : entity is "xpm_cdc_single";
  attribute SIM_ASSERT_CHK : integer;
  attribute SIM_ASSERT_CHK of \FPGAtoFTDI_fifo_xpm_cdc_single__1\ : entity is 0;
  attribute SRC_INPUT_REG : integer;
  attribute SRC_INPUT_REG of \FPGAtoFTDI_fifo_xpm_cdc_single__1\ : entity is 0;
  attribute VERSION : integer;
  attribute VERSION of \FPGAtoFTDI_fifo_xpm_cdc_single__1\ : entity is 0;
  attribute XPM_MODULE : string;
  attribute XPM_MODULE of \FPGAtoFTDI_fifo_xpm_cdc_single__1\ : entity is "TRUE";
  attribute xpm_cdc : string;
  attribute xpm_cdc of \FPGAtoFTDI_fifo_xpm_cdc_single__1\ : entity is "SINGLE";
end \FPGAtoFTDI_fifo_xpm_cdc_single__1\;

architecture STRUCTURE of \FPGAtoFTDI_fifo_xpm_cdc_single__1\ is
  signal syncstages_ff : STD_LOGIC_VECTOR ( 3 downto 0 );
  attribute RTL_KEEP : string;
  attribute RTL_KEEP of syncstages_ff : signal is "true";
  attribute async_reg : string;
  attribute async_reg of syncstages_ff : signal is "true";
  attribute xpm_cdc of syncstages_ff : signal is "SINGLE";
  attribute ASYNC_REG_boolean : boolean;
  attribute ASYNC_REG_boolean of \syncstages_ff_reg[0]\ : label is std.standard.true;
  attribute KEEP : string;
  attribute KEEP of \syncstages_ff_reg[0]\ : label is "true";
  attribute XPM_CDC of \syncstages_ff_reg[0]\ : label is "SINGLE";
  attribute ASYNC_REG_boolean of \syncstages_ff_reg[1]\ : label is std.standard.true;
  attribute KEEP of \syncstages_ff_reg[1]\ : label is "true";
  attribute XPM_CDC of \syncstages_ff_reg[1]\ : label is "SINGLE";
  attribute ASYNC_REG_boolean of \syncstages_ff_reg[2]\ : label is std.standard.true;
  attribute KEEP of \syncstages_ff_reg[2]\ : label is "true";
  attribute XPM_CDC of \syncstages_ff_reg[2]\ : label is "SINGLE";
  attribute ASYNC_REG_boolean of \syncstages_ff_reg[3]\ : label is std.standard.true;
  attribute KEEP of \syncstages_ff_reg[3]\ : label is "true";
  attribute XPM_CDC of \syncstages_ff_reg[3]\ : label is "SINGLE";
begin
  dest_out <= syncstages_ff(3);
\syncstages_ff_reg[0]\: unisim.vcomponents.FDRE
     port map (
      C => dest_clk,
      CE => '1',
      D => src_in,
      Q => syncstages_ff(0),
      R => '0'
    );
\syncstages_ff_reg[1]\: unisim.vcomponents.FDRE
     port map (
      C => dest_clk,
      CE => '1',
      D => syncstages_ff(0),
      Q => syncstages_ff(1),
      R => '0'
    );
\syncstages_ff_reg[2]\: unisim.vcomponents.FDRE
     port map (
      C => dest_clk,
      CE => '1',
      D => syncstages_ff(1),
      Q => syncstages_ff(2),
      R => '0'
    );
\syncstages_ff_reg[3]\: unisim.vcomponents.FDRE
     port map (
      C => dest_clk,
      CE => '1',
      D => syncstages_ff(2),
      Q => syncstages_ff(3),
      R => '0'
    );
end STRUCTURE;
library IEEE;
use IEEE.STD_LOGIC_1164.ALL;
library UNISIM;
use UNISIM.VCOMPONENTS.ALL;
entity FPGAtoFTDI_fifo_blk_mem_gen_prim_wrapper is
  port (
    dout : out STD_LOGIC_VECTOR ( 7 downto 0 );
    wr_clk : in STD_LOGIC;
    rd_clk : in STD_LOGIC;
    E : in STD_LOGIC_VECTOR ( 0 to 0 );
    tmp_ram_rd_en : in STD_LOGIC;
    AR : in STD_LOGIC_VECTOR ( 0 to 0 );
    \gic0.gc0.count_d2_reg[9]\ : in STD_LOGIC_VECTOR ( 9 downto 0 );
    \gc0.count_d1_reg[10]\ : in STD_LOGIC_VECTOR ( 10 downto 0 );
    din : in STD_LOGIC_VECTOR ( 15 downto 0 )
  );
  attribute ORIG_REF_NAME : string;
  attribute ORIG_REF_NAME of FPGAtoFTDI_fifo_blk_mem_gen_prim_wrapper : entity is "blk_mem_gen_prim_wrapper";
end FPGAtoFTDI_fifo_blk_mem_gen_prim_wrapper;

architecture STRUCTURE of FPGAtoFTDI_fifo_blk_mem_gen_prim_wrapper is
  signal \DEVICE_7SERIES.NO_BMM_INFO.SDP.SIMPLE_PRIM18.ram_n_35\ : STD_LOGIC;
  signal \NLW_DEVICE_7SERIES.NO_BMM_INFO.SDP.SIMPLE_PRIM18.ram_DOADO_UNCONNECTED\ : STD_LOGIC_VECTOR ( 15 downto 0 );
  signal \NLW_DEVICE_7SERIES.NO_BMM_INFO.SDP.SIMPLE_PRIM18.ram_DOBDO_UNCONNECTED\ : STD_LOGIC_VECTOR ( 15 downto 8 );
  signal \NLW_DEVICE_7SERIES.NO_BMM_INFO.SDP.SIMPLE_PRIM18.ram_DOPADOP_UNCONNECTED\ : STD_LOGIC_VECTOR ( 1 downto 0 );
  signal \NLW_DEVICE_7SERIES.NO_BMM_INFO.SDP.SIMPLE_PRIM18.ram_DOPBDOP_UNCONNECTED\ : STD_LOGIC_VECTOR ( 1 to 1 );
  attribute box_type : string;
  attribute box_type of \DEVICE_7SERIES.NO_BMM_INFO.SDP.SIMPLE_PRIM18.ram\ : label is "PRIMITIVE";
begin
\DEVICE_7SERIES.NO_BMM_INFO.SDP.SIMPLE_PRIM18.ram\: unisim.vcomponents.RAMB18E1
    generic map(
      DOA_REG => 0,
      DOB_REG => 0,
      INITP_00 => X"0000000000000000000000000000000000000000000000000000000000000000",
      INITP_01 => X"0000000000000000000000000000000000000000000000000000000000000000",
      INITP_02 => X"0000000000000000000000000000000000000000000000000000000000000000",
      INITP_03 => X"0000000000000000000000000000000000000000000000000000000000000000",
      INITP_04 => X"0000000000000000000000000000000000000000000000000000000000000000",
      INITP_05 => X"0000000000000000000000000000000000000000000000000000000000000000",
      INITP_06 => X"0000000000000000000000000000000000000000000000000000000000000000",
      INITP_07 => X"0000000000000000000000000000000000000000000000000000000000000000",
      INIT_00 => X"0000000000000000000000000000000000000000000000000000000000000000",
      INIT_01 => X"0000000000000000000000000000000000000000000000000000000000000000",
      INIT_02 => X"0000000000000000000000000000000000000000000000000000000000000000",
      INIT_03 => X"0000000000000000000000000000000000000000000000000000000000000000",
      INIT_04 => X"0000000000000000000000000000000000000000000000000000000000000000",
      INIT_05 => X"0000000000000000000000000000000000000000000000000000000000000000",
      INIT_06 => X"0000000000000000000000000000000000000000000000000000000000000000",
      INIT_07 => X"0000000000000000000000000000000000000000000000000000000000000000",
      INIT_08 => X"0000000000000000000000000000000000000000000000000000000000000000",
      INIT_09 => X"0000000000000000000000000000000000000000000000000000000000000000",
      INIT_0A => X"0000000000000000000000000000000000000000000000000000000000000000",
      INIT_0B => X"0000000000000000000000000000000000000000000000000000000000000000",
      INIT_0C => X"0000000000000000000000000000000000000000000000000000000000000000",
      INIT_0D => X"0000000000000000000000000000000000000000000000000000000000000000",
      INIT_0E => X"0000000000000000000000000000000000000000000000000000000000000000",
      INIT_0F => X"0000000000000000000000000000000000000000000000000000000000000000",
      INIT_10 => X"0000000000000000000000000000000000000000000000000000000000000000",
      INIT_11 => X"0000000000000000000000000000000000000000000000000000000000000000",
      INIT_12 => X"0000000000000000000000000000000000000000000000000000000000000000",
      INIT_13 => X"0000000000000000000000000000000000000000000000000000000000000000",
      INIT_14 => X"0000000000000000000000000000000000000000000000000000000000000000",
      INIT_15 => X"0000000000000000000000000000000000000000000000000000000000000000",
      INIT_16 => X"0000000000000000000000000000000000000000000000000000000000000000",
      INIT_17 => X"0000000000000000000000000000000000000000000000000000000000000000",
      INIT_18 => X"0000000000000000000000000000000000000000000000000000000000000000",
      INIT_19 => X"0000000000000000000000000000000000000000000000000000000000000000",
      INIT_1A => X"0000000000000000000000000000000000000000000000000000000000000000",
      INIT_1B => X"0000000000000000000000000000000000000000000000000000000000000000",
      INIT_1C => X"0000000000000000000000000000000000000000000000000000000000000000",
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
      DIADI(7 downto 0) => din(15 downto 8),
      DIBDI(15 downto 0) => B"0000000000000000",
      DIPADIP(1 downto 0) => B"00",
      DIPBDIP(1 downto 0) => B"00",
      DOADO(15 downto 0) => \NLW_DEVICE_7SERIES.NO_BMM_INFO.SDP.SIMPLE_PRIM18.ram_DOADO_UNCONNECTED\(15 downto 0),
      DOBDO(15 downto 8) => \NLW_DEVICE_7SERIES.NO_BMM_INFO.SDP.SIMPLE_PRIM18.ram_DOBDO_UNCONNECTED\(15 downto 8),
      DOBDO(7 downto 0) => dout(7 downto 0),
      DOPADOP(1 downto 0) => \NLW_DEVICE_7SERIES.NO_BMM_INFO.SDP.SIMPLE_PRIM18.ram_DOPADOP_UNCONNECTED\(1 downto 0),
      DOPBDOP(1) => \NLW_DEVICE_7SERIES.NO_BMM_INFO.SDP.SIMPLE_PRIM18.ram_DOPBDOP_UNCONNECTED\(1),
      DOPBDOP(0) => \DEVICE_7SERIES.NO_BMM_INFO.SDP.SIMPLE_PRIM18.ram_n_35\,
      ENARDEN => E(0),
      ENBWREN => tmp_ram_rd_en,
      REGCEAREGCE => '0',
      REGCEB => '0',
      RSTRAMARSTRAM => '0',
      RSTRAMB => AR(0),
      RSTREGARSTREG => '0',
      RSTREGB => '0',
      WEA(1) => E(0),
      WEA(0) => E(0),
      WEBWE(3 downto 0) => B"0000"
    );
end STRUCTURE;
library IEEE;
use IEEE.STD_LOGIC_1164.ALL;
library UNISIM;
use UNISIM.VCOMPONENTS.ALL;
entity FPGAtoFTDI_fifo_compare is
  port (
    ram_empty_fb_i_reg : out STD_LOGIC;
    v1_reg : in STD_LOGIC_VECTOR ( 4 downto 0 );
    \dest_out_bin_ff_reg[9]\ : in STD_LOGIC_VECTOR ( 0 to 0 );
    rd_en : in STD_LOGIC;
    \out\ : in STD_LOGIC;
    comp1 : in STD_LOGIC
  );
  attribute ORIG_REF_NAME : string;
  attribute ORIG_REF_NAME of FPGAtoFTDI_fifo_compare : entity is "compare";
end FPGAtoFTDI_fifo_compare;

architecture STRUCTURE of FPGAtoFTDI_fifo_compare is
  signal carrynet_0 : STD_LOGIC;
  signal carrynet_1 : STD_LOGIC;
  signal carrynet_2 : STD_LOGIC;
  signal carrynet_3 : STD_LOGIC;
  signal carrynet_4 : STD_LOGIC;
  signal comp0 : STD_LOGIC;
  signal \NLW_gmux.gm[0].gm1.m1_CARRY4_O_UNCONNECTED\ : STD_LOGIC_VECTOR ( 3 downto 0 );
  signal \NLW_gmux.gm[4].gms.ms_CARRY4_CO_UNCONNECTED\ : STD_LOGIC_VECTOR ( 3 downto 2 );
  signal \NLW_gmux.gm[4].gms.ms_CARRY4_DI_UNCONNECTED\ : STD_LOGIC_VECTOR ( 3 downto 2 );
  signal \NLW_gmux.gm[4].gms.ms_CARRY4_O_UNCONNECTED\ : STD_LOGIC_VECTOR ( 3 downto 0 );
  signal \NLW_gmux.gm[4].gms.ms_CARRY4_S_UNCONNECTED\ : STD_LOGIC_VECTOR ( 3 downto 2 );
  attribute XILINX_LEGACY_PRIM : string;
  attribute XILINX_LEGACY_PRIM of \gmux.gm[0].gm1.m1_CARRY4\ : label is "(MUXCY,XORCY)";
  attribute box_type : string;
  attribute box_type of \gmux.gm[0].gm1.m1_CARRY4\ : label is "PRIMITIVE";
  attribute XILINX_LEGACY_PRIM of \gmux.gm[4].gms.ms_CARRY4\ : label is "(MUXCY,XORCY)";
  attribute box_type of \gmux.gm[4].gms.ms_CARRY4\ : label is "PRIMITIVE";
begin
\gmux.gm[0].gm1.m1_CARRY4\: unisim.vcomponents.CARRY4
     port map (
      CI => '0',
      CO(3) => carrynet_3,
      CO(2) => carrynet_2,
      CO(1) => carrynet_1,
      CO(0) => carrynet_0,
      CYINIT => '1',
      DI(3 downto 0) => B"0000",
      O(3 downto 0) => \NLW_gmux.gm[0].gm1.m1_CARRY4_O_UNCONNECTED\(3 downto 0),
      S(3 downto 0) => v1_reg(3 downto 0)
    );
\gmux.gm[4].gms.ms_CARRY4\: unisim.vcomponents.CARRY4
     port map (
      CI => carrynet_3,
      CO(3 downto 2) => \NLW_gmux.gm[4].gms.ms_CARRY4_CO_UNCONNECTED\(3 downto 2),
      CO(1) => comp0,
      CO(0) => carrynet_4,
      CYINIT => '0',
      DI(3 downto 2) => \NLW_gmux.gm[4].gms.ms_CARRY4_DI_UNCONNECTED\(3 downto 2),
      DI(1 downto 0) => B"00",
      O(3 downto 0) => \NLW_gmux.gm[4].gms.ms_CARRY4_O_UNCONNECTED\(3 downto 0),
      S(3 downto 2) => \NLW_gmux.gm[4].gms.ms_CARRY4_S_UNCONNECTED\(3 downto 2),
      S(1) => \dest_out_bin_ff_reg[9]\(0),
      S(0) => v1_reg(4)
    );
ram_empty_i_i_1: unisim.vcomponents.LUT4
    generic map(
      INIT => X"AEAA"
    )
        port map (
      I0 => comp0,
      I1 => rd_en,
      I2 => \out\,
      I3 => comp1,
      O => ram_empty_fb_i_reg
    );
end STRUCTURE;
library IEEE;
use IEEE.STD_LOGIC_1164.ALL;
library UNISIM;
use UNISIM.VCOMPONENTS.ALL;
entity FPGAtoFTDI_fifo_compare_1 is
  port (
    comp1 : out STD_LOGIC;
    v1_reg_0 : in STD_LOGIC_VECTOR ( 4 downto 0 );
    \dest_out_bin_ff_reg[9]\ : in STD_LOGIC_VECTOR ( 0 to 0 )
  );
  attribute ORIG_REF_NAME : string;
  attribute ORIG_REF_NAME of FPGAtoFTDI_fifo_compare_1 : entity is "compare";
end FPGAtoFTDI_fifo_compare_1;

architecture STRUCTURE of FPGAtoFTDI_fifo_compare_1 is
  signal carrynet_0 : STD_LOGIC;
  signal carrynet_1 : STD_LOGIC;
  signal carrynet_2 : STD_LOGIC;
  signal carrynet_3 : STD_LOGIC;
  signal carrynet_4 : STD_LOGIC;
  signal \NLW_gmux.gm[0].gm1.m1_CARRY4_O_UNCONNECTED\ : STD_LOGIC_VECTOR ( 3 downto 0 );
  signal \NLW_gmux.gm[4].gms.ms_CARRY4_CO_UNCONNECTED\ : STD_LOGIC_VECTOR ( 3 downto 2 );
  signal \NLW_gmux.gm[4].gms.ms_CARRY4_DI_UNCONNECTED\ : STD_LOGIC_VECTOR ( 3 downto 2 );
  signal \NLW_gmux.gm[4].gms.ms_CARRY4_O_UNCONNECTED\ : STD_LOGIC_VECTOR ( 3 downto 0 );
  signal \NLW_gmux.gm[4].gms.ms_CARRY4_S_UNCONNECTED\ : STD_LOGIC_VECTOR ( 3 downto 2 );
  attribute XILINX_LEGACY_PRIM : string;
  attribute XILINX_LEGACY_PRIM of \gmux.gm[0].gm1.m1_CARRY4\ : label is "(MUXCY,XORCY)";
  attribute box_type : string;
  attribute box_type of \gmux.gm[0].gm1.m1_CARRY4\ : label is "PRIMITIVE";
  attribute XILINX_LEGACY_PRIM of \gmux.gm[4].gms.ms_CARRY4\ : label is "(MUXCY,XORCY)";
  attribute box_type of \gmux.gm[4].gms.ms_CARRY4\ : label is "PRIMITIVE";
begin
\gmux.gm[0].gm1.m1_CARRY4\: unisim.vcomponents.CARRY4
     port map (
      CI => '0',
      CO(3) => carrynet_3,
      CO(2) => carrynet_2,
      CO(1) => carrynet_1,
      CO(0) => carrynet_0,
      CYINIT => '1',
      DI(3 downto 0) => B"0000",
      O(3 downto 0) => \NLW_gmux.gm[0].gm1.m1_CARRY4_O_UNCONNECTED\(3 downto 0),
      S(3 downto 0) => v1_reg_0(3 downto 0)
    );
\gmux.gm[4].gms.ms_CARRY4\: unisim.vcomponents.CARRY4
     port map (
      CI => carrynet_3,
      CO(3 downto 2) => \NLW_gmux.gm[4].gms.ms_CARRY4_CO_UNCONNECTED\(3 downto 2),
      CO(1) => comp1,
      CO(0) => carrynet_4,
      CYINIT => '0',
      DI(3 downto 2) => \NLW_gmux.gm[4].gms.ms_CARRY4_DI_UNCONNECTED\(3 downto 2),
      DI(1 downto 0) => B"00",
      O(3 downto 0) => \NLW_gmux.gm[4].gms.ms_CARRY4_O_UNCONNECTED\(3 downto 0),
      S(3 downto 2) => \NLW_gmux.gm[4].gms.ms_CARRY4_S_UNCONNECTED\(3 downto 2),
      S(1) => \dest_out_bin_ff_reg[9]\(0),
      S(0) => v1_reg_0(4)
    );
end STRUCTURE;
library IEEE;
use IEEE.STD_LOGIC_1164.ALL;
library UNISIM;
use UNISIM.VCOMPONENTS.ALL;
entity \FPGAtoFTDI_fifo_compare__parameterized0\ is
  port (
    comp1 : out STD_LOGIC;
    v1_reg : in STD_LOGIC_VECTOR ( 4 downto 0 )
  );
  attribute ORIG_REF_NAME : string;
  attribute ORIG_REF_NAME of \FPGAtoFTDI_fifo_compare__parameterized0\ : entity is "compare";
end \FPGAtoFTDI_fifo_compare__parameterized0\;

architecture STRUCTURE of \FPGAtoFTDI_fifo_compare__parameterized0\ is
  signal carrynet_0 : STD_LOGIC;
  signal carrynet_1 : STD_LOGIC;
  signal carrynet_2 : STD_LOGIC;
  signal carrynet_3 : STD_LOGIC;
  signal \NLW_gmux.gm[0].gm1.m1_CARRY4_O_UNCONNECTED\ : STD_LOGIC_VECTOR ( 3 downto 0 );
  signal \NLW_gmux.gm[4].gms.ms_CARRY4_CO_UNCONNECTED\ : STD_LOGIC_VECTOR ( 3 downto 1 );
  signal \NLW_gmux.gm[4].gms.ms_CARRY4_DI_UNCONNECTED\ : STD_LOGIC_VECTOR ( 3 downto 1 );
  signal \NLW_gmux.gm[4].gms.ms_CARRY4_O_UNCONNECTED\ : STD_LOGIC_VECTOR ( 3 downto 0 );
  signal \NLW_gmux.gm[4].gms.ms_CARRY4_S_UNCONNECTED\ : STD_LOGIC_VECTOR ( 3 downto 1 );
  attribute XILINX_LEGACY_PRIM : string;
  attribute XILINX_LEGACY_PRIM of \gmux.gm[0].gm1.m1_CARRY4\ : label is "(MUXCY,XORCY)";
  attribute box_type : string;
  attribute box_type of \gmux.gm[0].gm1.m1_CARRY4\ : label is "PRIMITIVE";
  attribute XILINX_LEGACY_PRIM of \gmux.gm[4].gms.ms_CARRY4\ : label is "(MUXCY,XORCY)";
  attribute box_type of \gmux.gm[4].gms.ms_CARRY4\ : label is "PRIMITIVE";
begin
\gmux.gm[0].gm1.m1_CARRY4\: unisim.vcomponents.CARRY4
     port map (
      CI => '0',
      CO(3) => carrynet_3,
      CO(2) => carrynet_2,
      CO(1) => carrynet_1,
      CO(0) => carrynet_0,
      CYINIT => '1',
      DI(3 downto 0) => B"0000",
      O(3 downto 0) => \NLW_gmux.gm[0].gm1.m1_CARRY4_O_UNCONNECTED\(3 downto 0),
      S(3 downto 0) => v1_reg(3 downto 0)
    );
\gmux.gm[4].gms.ms_CARRY4\: unisim.vcomponents.CARRY4
     port map (
      CI => carrynet_3,
      CO(3 downto 1) => \NLW_gmux.gm[4].gms.ms_CARRY4_CO_UNCONNECTED\(3 downto 1),
      CO(0) => comp1,
      CYINIT => '0',
      DI(3 downto 1) => \NLW_gmux.gm[4].gms.ms_CARRY4_DI_UNCONNECTED\(3 downto 1),
      DI(0) => '0',
      O(3 downto 0) => \NLW_gmux.gm[4].gms.ms_CARRY4_O_UNCONNECTED\(3 downto 0),
      S(3 downto 1) => \NLW_gmux.gm[4].gms.ms_CARRY4_S_UNCONNECTED\(3 downto 1),
      S(0) => v1_reg(4)
    );
end STRUCTURE;
library IEEE;
use IEEE.STD_LOGIC_1164.ALL;
library UNISIM;
use UNISIM.VCOMPONENTS.ALL;
entity \FPGAtoFTDI_fifo_compare__parameterized0_0\ is
  port (
    ram_full_fb_i_reg : out STD_LOGIC;
    v1_reg_0 : in STD_LOGIC_VECTOR ( 4 downto 0 );
    \out\ : in STD_LOGIC;
    wr_en : in STD_LOGIC;
    comp1 : in STD_LOGIC;
    \grstd1.grst_full.grst_f.rst_d3_reg\ : in STD_LOGIC
  );
  attribute ORIG_REF_NAME : string;
  attribute ORIG_REF_NAME of \FPGAtoFTDI_fifo_compare__parameterized0_0\ : entity is "compare";
end \FPGAtoFTDI_fifo_compare__parameterized0_0\;

architecture STRUCTURE of \FPGAtoFTDI_fifo_compare__parameterized0_0\ is
  signal carrynet_0 : STD_LOGIC;
  signal carrynet_1 : STD_LOGIC;
  signal carrynet_2 : STD_LOGIC;
  signal carrynet_3 : STD_LOGIC;
  signal comp2 : STD_LOGIC;
  signal \NLW_gmux.gm[0].gm1.m1_CARRY4_O_UNCONNECTED\ : STD_LOGIC_VECTOR ( 3 downto 0 );
  signal \NLW_gmux.gm[4].gms.ms_CARRY4_CO_UNCONNECTED\ : STD_LOGIC_VECTOR ( 3 downto 1 );
  signal \NLW_gmux.gm[4].gms.ms_CARRY4_DI_UNCONNECTED\ : STD_LOGIC_VECTOR ( 3 downto 1 );
  signal \NLW_gmux.gm[4].gms.ms_CARRY4_O_UNCONNECTED\ : STD_LOGIC_VECTOR ( 3 downto 0 );
  signal \NLW_gmux.gm[4].gms.ms_CARRY4_S_UNCONNECTED\ : STD_LOGIC_VECTOR ( 3 downto 1 );
  attribute XILINX_LEGACY_PRIM : string;
  attribute XILINX_LEGACY_PRIM of \gmux.gm[0].gm1.m1_CARRY4\ : label is "(MUXCY,XORCY)";
  attribute box_type : string;
  attribute box_type of \gmux.gm[0].gm1.m1_CARRY4\ : label is "PRIMITIVE";
  attribute XILINX_LEGACY_PRIM of \gmux.gm[4].gms.ms_CARRY4\ : label is "(MUXCY,XORCY)";
  attribute box_type of \gmux.gm[4].gms.ms_CARRY4\ : label is "PRIMITIVE";
begin
\gmux.gm[0].gm1.m1_CARRY4\: unisim.vcomponents.CARRY4
     port map (
      CI => '0',
      CO(3) => carrynet_3,
      CO(2) => carrynet_2,
      CO(1) => carrynet_1,
      CO(0) => carrynet_0,
      CYINIT => '1',
      DI(3 downto 0) => B"0000",
      O(3 downto 0) => \NLW_gmux.gm[0].gm1.m1_CARRY4_O_UNCONNECTED\(3 downto 0),
      S(3 downto 0) => v1_reg_0(3 downto 0)
    );
\gmux.gm[4].gms.ms_CARRY4\: unisim.vcomponents.CARRY4
     port map (
      CI => carrynet_3,
      CO(3 downto 1) => \NLW_gmux.gm[4].gms.ms_CARRY4_CO_UNCONNECTED\(3 downto 1),
      CO(0) => comp2,
      CYINIT => '0',
      DI(3 downto 1) => \NLW_gmux.gm[4].gms.ms_CARRY4_DI_UNCONNECTED\(3 downto 1),
      DI(0) => '0',
      O(3 downto 0) => \NLW_gmux.gm[4].gms.ms_CARRY4_O_UNCONNECTED\(3 downto 0),
      S(3 downto 1) => \NLW_gmux.gm[4].gms.ms_CARRY4_S_UNCONNECTED\(3 downto 1),
      S(0) => v1_reg_0(4)
    );
ram_full_i_i_1: unisim.vcomponents.LUT5
    generic map(
      INIT => X"0000FF20"
    )
        port map (
      I0 => comp2,
      I1 => \out\,
      I2 => wr_en,
      I3 => comp1,
      I4 => \grstd1.grst_full.grst_f.rst_d3_reg\,
      O => ram_full_fb_i_reg
    );
end STRUCTURE;
library IEEE;
use IEEE.STD_LOGIC_1164.ALL;
library UNISIM;
use UNISIM.VCOMPONENTS.ALL;
entity FPGAtoFTDI_fifo_rd_bin_cntr is
  port (
    Q : out STD_LOGIC_VECTOR ( 0 to 0 );
    v1_reg : out STD_LOGIC_VECTOR ( 4 downto 0 );
    \DEVICE_7SERIES.NO_BMM_INFO.SDP.SIMPLE_PRIM18.ram\ : out STD_LOGIC_VECTOR ( 10 downto 0 );
    v1_reg_0 : out STD_LOGIC_VECTOR ( 4 downto 0 );
    WR_PNTR_RD : in STD_LOGIC_VECTOR ( 8 downto 0 );
    E : in STD_LOGIC_VECTOR ( 0 to 0 );
    rd_clk : in STD_LOGIC;
    AR : in STD_LOGIC_VECTOR ( 0 to 0 )
  );
  attribute ORIG_REF_NAME : string;
  attribute ORIG_REF_NAME of FPGAtoFTDI_fifo_rd_bin_cntr : entity is "rd_bin_cntr";
end FPGAtoFTDI_fifo_rd_bin_cntr;

architecture STRUCTURE of FPGAtoFTDI_fifo_rd_bin_cntr is
  signal \^device_7series.no_bmm_info.sdp.simple_prim18.ram\ : STD_LOGIC_VECTOR ( 10 downto 0 );
  signal \^q\ : STD_LOGIC_VECTOR ( 0 to 0 );
  signal \gc0.count[10]_i_2_n_0\ : STD_LOGIC;
  signal \plusOp__0\ : STD_LOGIC_VECTOR ( 10 downto 0 );
  signal rd_pntr_plus1 : STD_LOGIC_VECTOR ( 9 downto 0 );
  attribute SOFT_HLUTNM : string;
  attribute SOFT_HLUTNM of \gc0.count[1]_i_1\ : label is "soft_lutpair12";
  attribute SOFT_HLUTNM of \gc0.count[2]_i_1\ : label is "soft_lutpair12";
  attribute SOFT_HLUTNM of \gc0.count[3]_i_1\ : label is "soft_lutpair10";
  attribute SOFT_HLUTNM of \gc0.count[4]_i_1\ : label is "soft_lutpair10";
  attribute SOFT_HLUTNM of \gc0.count[6]_i_1\ : label is "soft_lutpair11";
  attribute SOFT_HLUTNM of \gc0.count[7]_i_1\ : label is "soft_lutpair11";
  attribute SOFT_HLUTNM of \gc0.count[8]_i_1\ : label is "soft_lutpair9";
  attribute SOFT_HLUTNM of \gc0.count[9]_i_1\ : label is "soft_lutpair9";
begin
  \DEVICE_7SERIES.NO_BMM_INFO.SDP.SIMPLE_PRIM18.ram\(10 downto 0) <= \^device_7series.no_bmm_info.sdp.simple_prim18.ram\(10 downto 0);
  Q(0) <= \^q\(0);
\gc0.count[0]_i_1\: unisim.vcomponents.LUT1
    generic map(
      INIT => X"1"
    )
        port map (
      I0 => rd_pntr_plus1(0),
      O => \plusOp__0\(0)
    );
\gc0.count[10]_i_1\: unisim.vcomponents.LUT6
    generic map(
      INIT => X"7FFFFFFF80000000"
    )
        port map (
      I0 => rd_pntr_plus1(8),
      I1 => rd_pntr_plus1(6),
      I2 => \gc0.count[10]_i_2_n_0\,
      I3 => rd_pntr_plus1(7),
      I4 => rd_pntr_plus1(9),
      I5 => \^q\(0),
      O => \plusOp__0\(10)
    );
\gc0.count[10]_i_2\: unisim.vcomponents.LUT6
    generic map(
      INIT => X"8000000000000000"
    )
        port map (
      I0 => rd_pntr_plus1(5),
      I1 => rd_pntr_plus1(3),
      I2 => rd_pntr_plus1(1),
      I3 => rd_pntr_plus1(0),
      I4 => rd_pntr_plus1(2),
      I5 => rd_pntr_plus1(4),
      O => \gc0.count[10]_i_2_n_0\
    );
\gc0.count[1]_i_1\: unisim.vcomponents.LUT2
    generic map(
      INIT => X"6"
    )
        port map (
      I0 => rd_pntr_plus1(0),
      I1 => rd_pntr_plus1(1),
      O => \plusOp__0\(1)
    );
\gc0.count[2]_i_1\: unisim.vcomponents.LUT3
    generic map(
      INIT => X"78"
    )
        port map (
      I0 => rd_pntr_plus1(0),
      I1 => rd_pntr_plus1(1),
      I2 => rd_pntr_plus1(2),
      O => \plusOp__0\(2)
    );
\gc0.count[3]_i_1\: unisim.vcomponents.LUT4
    generic map(
      INIT => X"7F80"
    )
        port map (
      I0 => rd_pntr_plus1(1),
      I1 => rd_pntr_plus1(0),
      I2 => rd_pntr_plus1(2),
      I3 => rd_pntr_plus1(3),
      O => \plusOp__0\(3)
    );
\gc0.count[4]_i_1\: unisim.vcomponents.LUT5
    generic map(
      INIT => X"7FFF8000"
    )
        port map (
      I0 => rd_pntr_plus1(2),
      I1 => rd_pntr_plus1(0),
      I2 => rd_pntr_plus1(1),
      I3 => rd_pntr_plus1(3),
      I4 => rd_pntr_plus1(4),
      O => \plusOp__0\(4)
    );
\gc0.count[5]_i_1\: unisim.vcomponents.LUT6
    generic map(
      INIT => X"7FFFFFFF80000000"
    )
        port map (
      I0 => rd_pntr_plus1(3),
      I1 => rd_pntr_plus1(1),
      I2 => rd_pntr_plus1(0),
      I3 => rd_pntr_plus1(2),
      I4 => rd_pntr_plus1(4),
      I5 => rd_pntr_plus1(5),
      O => \plusOp__0\(5)
    );
\gc0.count[6]_i_1\: unisim.vcomponents.LUT2
    generic map(
      INIT => X"6"
    )
        port map (
      I0 => \gc0.count[10]_i_2_n_0\,
      I1 => rd_pntr_plus1(6),
      O => \plusOp__0\(6)
    );
\gc0.count[7]_i_1\: unisim.vcomponents.LUT3
    generic map(
      INIT => X"78"
    )
        port map (
      I0 => \gc0.count[10]_i_2_n_0\,
      I1 => rd_pntr_plus1(6),
      I2 => rd_pntr_plus1(7),
      O => \plusOp__0\(7)
    );
\gc0.count[8]_i_1\: unisim.vcomponents.LUT4
    generic map(
      INIT => X"7F80"
    )
        port map (
      I0 => rd_pntr_plus1(6),
      I1 => \gc0.count[10]_i_2_n_0\,
      I2 => rd_pntr_plus1(7),
      I3 => rd_pntr_plus1(8),
      O => \plusOp__0\(8)
    );
\gc0.count[9]_i_1\: unisim.vcomponents.LUT5
    generic map(
      INIT => X"7FFF8000"
    )
        port map (
      I0 => rd_pntr_plus1(7),
      I1 => \gc0.count[10]_i_2_n_0\,
      I2 => rd_pntr_plus1(6),
      I3 => rd_pntr_plus1(8),
      I4 => rd_pntr_plus1(9),
      O => \plusOp__0\(9)
    );
\gc0.count_d1_reg[0]\: unisim.vcomponents.FDCE
    generic map(
      INIT => '0'
    )
        port map (
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
      I1 => WR_PNTR_RD(5),
      I2 => \^device_7series.no_bmm_info.sdp.simple_prim18.ram\(7),
      I3 => WR_PNTR_RD(6),
      O => v1_reg(3)
    );
\gmux.gm[3].gms.ms_i_1__2\: unisim.vcomponents.LUT4
    generic map(
      INIT => X"9009"
    )
        port map (
      I0 => rd_pntr_plus1(6),
      I1 => WR_PNTR_RD(5),
      I2 => rd_pntr_plus1(7),
      I3 => WR_PNTR_RD(6),
      O => v1_reg_0(3)
    );
\gmux.gm[4].gms.ms_i_1__1\: unisim.vcomponents.LUT4
    generic map(
      INIT => X"9009"
    )
        port map (
      I0 => \^device_7series.no_bmm_info.sdp.simple_prim18.ram\(8),
      I1 => WR_PNTR_RD(7),
      I2 => \^device_7series.no_bmm_info.sdp.simple_prim18.ram\(9),
      I3 => WR_PNTR_RD(8),
      O => v1_reg(4)
    );
\gmux.gm[4].gms.ms_i_1__2\: unisim.vcomponents.LUT4
    generic map(
      INIT => X"9009"
    )
        port map (
      I0 => rd_pntr_plus1(8),
      I1 => WR_PNTR_RD(7),
      I2 => rd_pntr_plus1(9),
      I3 => WR_PNTR_RD(8),
      O => v1_reg_0(4)
    );
end STRUCTURE;
library IEEE;
use IEEE.STD_LOGIC_1164.ALL;
library UNISIM;
use UNISIM.VCOMPONENTS.ALL;
entity FPGAtoFTDI_fifo_wr_bin_cntr is
  port (
    Q : out STD_LOGIC_VECTOR ( 9 downto 0 );
    \gic0.gc0.count_d2_reg[9]_0\ : out STD_LOGIC_VECTOR ( 9 downto 0 );
    \DEVICE_7SERIES.NO_BMM_INFO.SDP.SIMPLE_PRIM18.ram\ : out STD_LOGIC_VECTOR ( 9 downto 0 );
    E : in STD_LOGIC_VECTOR ( 0 to 0 );
    wr_clk : in STD_LOGIC;
    AR : in STD_LOGIC_VECTOR ( 0 to 0 )
  );
  attribute ORIG_REF_NAME : string;
  attribute ORIG_REF_NAME of FPGAtoFTDI_fifo_wr_bin_cntr : entity is "wr_bin_cntr";
end FPGAtoFTDI_fifo_wr_bin_cntr;

architecture STRUCTURE of FPGAtoFTDI_fifo_wr_bin_cntr is
  signal \^q\ : STD_LOGIC_VECTOR ( 9 downto 0 );
  signal \gic0.gc0.count[9]_i_2_n_0\ : STD_LOGIC;
  signal \^gic0.gc0.count_d2_reg[9]_0\ : STD_LOGIC_VECTOR ( 9 downto 0 );
  signal plusOp : STD_LOGIC_VECTOR ( 9 downto 0 );
  attribute SOFT_HLUTNM : string;
  attribute SOFT_HLUTNM of \gic0.gc0.count[0]_i_1\ : label is "soft_lutpair16";
  attribute SOFT_HLUTNM of \gic0.gc0.count[2]_i_1\ : label is "soft_lutpair16";
  attribute SOFT_HLUTNM of \gic0.gc0.count[3]_i_1\ : label is "soft_lutpair14";
  attribute SOFT_HLUTNM of \gic0.gc0.count[4]_i_1\ : label is "soft_lutpair14";
  attribute SOFT_HLUTNM of \gic0.gc0.count[6]_i_1\ : label is "soft_lutpair15";
  attribute SOFT_HLUTNM of \gic0.gc0.count[7]_i_1\ : label is "soft_lutpair15";
  attribute SOFT_HLUTNM of \gic0.gc0.count[8]_i_1\ : label is "soft_lutpair13";
  attribute SOFT_HLUTNM of \gic0.gc0.count[9]_i_1\ : label is "soft_lutpair13";
begin
  Q(9 downto 0) <= \^q\(9 downto 0);
  \gic0.gc0.count_d2_reg[9]_0\(9 downto 0) <= \^gic0.gc0.count_d2_reg[9]_0\(9 downto 0);
\gic0.gc0.count[0]_i_1\: unisim.vcomponents.LUT1
    generic map(
      INIT => X"1"
    )
        port map (
      I0 => \^q\(0),
      O => plusOp(0)
    );
\gic0.gc0.count[1]_i_1\: unisim.vcomponents.LUT2
    generic map(
      INIT => X"6"
    )
        port map (
      I0 => \^q\(0),
      I1 => \^q\(1),
      O => plusOp(1)
    );
\gic0.gc0.count[2]_i_1\: unisim.vcomponents.LUT3
    generic map(
      INIT => X"78"
    )
        port map (
      I0 => \^q\(0),
      I1 => \^q\(1),
      I2 => \^q\(2),
      O => plusOp(2)
    );
\gic0.gc0.count[3]_i_1\: unisim.vcomponents.LUT4
    generic map(
      INIT => X"7F80"
    )
        port map (
      I0 => \^q\(1),
      I1 => \^q\(0),
      I2 => \^q\(2),
      I3 => \^q\(3),
      O => plusOp(3)
    );
\gic0.gc0.count[4]_i_1\: unisim.vcomponents.LUT5
    generic map(
      INIT => X"7FFF8000"
    )
        port map (
      I0 => \^q\(2),
      I1 => \^q\(0),
      I2 => \^q\(1),
      I3 => \^q\(3),
      I4 => \^q\(4),
      O => plusOp(4)
    );
\gic0.gc0.count[5]_i_1\: unisim.vcomponents.LUT6
    generic map(
      INIT => X"7FFFFFFF80000000"
    )
        port map (
      I0 => \^q\(3),
      I1 => \^q\(1),
      I2 => \^q\(0),
      I3 => \^q\(2),
      I4 => \^q\(4),
      I5 => \^q\(5),
      O => plusOp(5)
    );
\gic0.gc0.count[6]_i_1\: unisim.vcomponents.LUT2
    generic map(
      INIT => X"6"
    )
        port map (
      I0 => \gic0.gc0.count[9]_i_2_n_0\,
      I1 => \^q\(6),
      O => plusOp(6)
    );
\gic0.gc0.count[7]_i_1\: unisim.vcomponents.LUT3
    generic map(
      INIT => X"78"
    )
        port map (
      I0 => \gic0.gc0.count[9]_i_2_n_0\,
      I1 => \^q\(6),
      I2 => \^q\(7),
      O => plusOp(7)
    );
\gic0.gc0.count[8]_i_1\: unisim.vcomponents.LUT4
    generic map(
      INIT => X"7F80"
    )
        port map (
      I0 => \^q\(6),
      I1 => \gic0.gc0.count[9]_i_2_n_0\,
      I2 => \^q\(7),
      I3 => \^q\(8),
      O => plusOp(8)
    );
\gic0.gc0.count[9]_i_1\: unisim.vcomponents.LUT5
    generic map(
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
      CLR => AR(0),
      D => plusOp(6),
      Q => \^q\(6)
    );
\gic0.gc0.count_reg[7]\: unisim.vcomponents.FDCE
    generic map(
      INIT => '0'
    )
        port map (
      C => wr_clk,
      CE => E(0),
      CLR => AR(0),
      D => plusOp(7),
      Q => \^q\(7)
    );
\gic0.gc0.count_reg[8]\: unisim.vcomponents.FDCE
    generic map(
      INIT => '0'
    )
        port map (
      C => wr_clk,
      CE => E(0),
      CLR => AR(0),
      D => plusOp(8),
      Q => \^q\(8)
    );
\gic0.gc0.count_reg[9]\: unisim.vcomponents.FDCE
    generic map(
      INIT => '0'
    )
        port map (
      C => wr_clk,
      CE => E(0),
      CLR => AR(0),
      D => plusOp(9),
      Q => \^q\(9)
    );
end STRUCTURE;
library IEEE;
use IEEE.STD_LOGIC_1164.ALL;
library UNISIM;
use UNISIM.VCOMPONENTS.ALL;
entity FPGAtoFTDI_fifo_blk_mem_gen_prim_width is
  port (
    dout : out STD_LOGIC_VECTOR ( 7 downto 0 );
    wr_clk : in STD_LOGIC;
    rd_clk : in STD_LOGIC;
    E : in STD_LOGIC_VECTOR ( 0 to 0 );
    tmp_ram_rd_en : in STD_LOGIC;
    AR : in STD_LOGIC_VECTOR ( 0 to 0 );
    \gic0.gc0.count_d2_reg[9]\ : in STD_LOGIC_VECTOR ( 9 downto 0 );
    \gc0.count_d1_reg[10]\ : in STD_LOGIC_VECTOR ( 10 downto 0 );
    din : in STD_LOGIC_VECTOR ( 15 downto 0 )
  );
  attribute ORIG_REF_NAME : string;
  attribute ORIG_REF_NAME of FPGAtoFTDI_fifo_blk_mem_gen_prim_width : entity is "blk_mem_gen_prim_width";
end FPGAtoFTDI_fifo_blk_mem_gen_prim_width;

architecture STRUCTURE of FPGAtoFTDI_fifo_blk_mem_gen_prim_width is
begin
\prim_noinit.ram\: entity work.FPGAtoFTDI_fifo_blk_mem_gen_prim_wrapper
     port map (
      AR(0) => AR(0),
      E(0) => E(0),
      din(15 downto 0) => din(15 downto 0),
      dout(7 downto 0) => dout(7 downto 0),
      \gc0.count_d1_reg[10]\(10 downto 0) => \gc0.count_d1_reg[10]\(10 downto 0),
      \gic0.gc0.count_d2_reg[9]\(9 downto 0) => \gic0.gc0.count_d2_reg[9]\(9 downto 0),
      rd_clk => rd_clk,
      tmp_ram_rd_en => tmp_ram_rd_en,
      wr_clk => wr_clk
    );
end STRUCTURE;
library IEEE;
use IEEE.STD_LOGIC_1164.ALL;
library UNISIM;
use UNISIM.VCOMPONENTS.ALL;
entity FPGAtoFTDI_fifo_clk_x_pntrs is
  port (
    v1_reg : out STD_LOGIC_VECTOR ( 4 downto 0 );
    v1_reg_0 : out STD_LOGIC_VECTOR ( 4 downto 0 );
    v1_reg_1 : out STD_LOGIC_VECTOR ( 0 to 0 );
    WR_PNTR_RD : out STD_LOGIC_VECTOR ( 8 downto 0 );
    v1_reg_2 : out STD_LOGIC_VECTOR ( 0 to 0 );
    Q : in STD_LOGIC_VECTOR ( 9 downto 0 );
    \gic0.gc0.count_reg[9]\ : in STD_LOGIC_VECTOR ( 9 downto 0 );
    \gc0.count_d1_reg[10]\ : in STD_LOGIC_VECTOR ( 10 downto 0 );
    \gc0.count_reg[10]\ : in STD_LOGIC_VECTOR ( 0 to 0 );
    wr_clk : in STD_LOGIC;
    \gic0.gc0.count_d2_reg[9]\ : in STD_LOGIC_VECTOR ( 9 downto 0 );
    rd_clk : in STD_LOGIC
  );
  attribute ORIG_REF_NAME : string;
  attribute ORIG_REF_NAME of FPGAtoFTDI_fifo_clk_x_pntrs : entity is "clk_x_pntrs";
end FPGAtoFTDI_fifo_clk_x_pntrs;

architecture STRUCTURE of FPGAtoFTDI_fifo_clk_x_pntrs is
  signal p_24_out : STD_LOGIC_VECTOR ( 9 to 9 );
  signal p_25_out : STD_LOGIC_VECTOR ( 10 downto 0 );
  attribute DEST_SYNC_FF : integer;
  attribute DEST_SYNC_FF of rd_pntr_cdc_inst : label is 2;
  attribute INIT_SYNC_FF : integer;
  attribute INIT_SYNC_FF of rd_pntr_cdc_inst : label is 0;
  attribute REG_OUTPUT : integer;
  attribute REG_OUTPUT of rd_pntr_cdc_inst : label is 1;
  attribute SIM_ASSERT_CHK : integer;
  attribute SIM_ASSERT_CHK of rd_pntr_cdc_inst : label is 0;
  attribute SIM_LOSSLESS_GRAY_CHK : integer;
  attribute SIM_LOSSLESS_GRAY_CHK of rd_pntr_cdc_inst : label is 0;
  attribute VERSION : integer;
  attribute VERSION of rd_pntr_cdc_inst : label is 0;
  attribute WIDTH : integer;
  attribute WIDTH of rd_pntr_cdc_inst : label is 11;
  attribute XPM_CDC : string;
  attribute XPM_CDC of rd_pntr_cdc_inst : label is "GRAY";
  attribute XPM_MODULE : string;
  attribute XPM_MODULE of rd_pntr_cdc_inst : label is "TRUE";
  attribute DEST_SYNC_FF of wr_pntr_cdc_inst : label is 2;
  attribute INIT_SYNC_FF of wr_pntr_cdc_inst : label is 0;
  attribute REG_OUTPUT of wr_pntr_cdc_inst : label is 1;
  attribute SIM_ASSERT_CHK of wr_pntr_cdc_inst : label is 0;
  attribute SIM_LOSSLESS_GRAY_CHK of wr_pntr_cdc_inst : label is 0;
  attribute VERSION of wr_pntr_cdc_inst : label is 0;
  attribute WIDTH of wr_pntr_cdc_inst : label is 10;
  attribute XPM_CDC of wr_pntr_cdc_inst : label is "GRAY";
  attribute XPM_MODULE of wr_pntr_cdc_inst : label is "TRUE";
begin
\gmux.gm[0].gm1.m1_i_1\: unisim.vcomponents.LUT4
    generic map(
      INIT => X"9009"
    )
        port map (
      I0 => p_25_out(1),
      I1 => Q(0),
      I2 => p_25_out(2),
      I3 => Q(1),
      O => v1_reg(0)
    );
\gmux.gm[0].gm1.m1_i_1__0\: unisim.vcomponents.LUT4
    generic map(
      INIT => X"9009"
    )
        port map (
      I0 => p_25_out(1),
      I1 => \gic0.gc0.count_reg[9]\(0),
      I2 => p_25_out(2),
      I3 => \gic0.gc0.count_reg[9]\(1),
      O => v1_reg_0(0)
    );
\gmux.gm[1].gms.ms_i_1\: unisim.vcomponents.LUT4
    generic map(
      INIT => X"9009"
    )
        port map (
      I0 => p_25_out(3),
      I1 => Q(2),
      I2 => p_25_out(4),
      I3 => Q(3),
      O => v1_reg(1)
    );
\gmux.gm[1].gms.ms_i_1__0\: unisim.vcomponents.LUT4
    generic map(
      INIT => X"9009"
    )
        port map (
      I0 => p_25_out(3),
      I1 => \gic0.gc0.count_reg[9]\(2),
      I2 => p_25_out(4),
      I3 => \gic0.gc0.count_reg[9]\(3),
      O => v1_reg_0(1)
    );
\gmux.gm[2].gms.ms_i_1\: unisim.vcomponents.LUT4
    generic map(
      INIT => X"9009"
    )
        port map (
      I0 => p_25_out(5),
      I1 => Q(4),
      I2 => p_25_out(6),
      I3 => Q(5),
      O => v1_reg(2)
    );
\gmux.gm[2].gms.ms_i_1__0\: unisim.vcomponents.LUT4
    generic map(
      INIT => X"9009"
    )
        port map (
      I0 => p_25_out(5),
      I1 => \gic0.gc0.count_reg[9]\(4),
      I2 => p_25_out(6),
      I3 => \gic0.gc0.count_reg[9]\(5),
      O => v1_reg_0(2)
    );
\gmux.gm[3].gms.ms_i_1\: unisim.vcomponents.LUT4
    generic map(
      INIT => X"9009"
    )
        port map (
      I0 => p_25_out(7),
      I1 => Q(6),
      I2 => p_25_out(8),
      I3 => Q(7),
      O => v1_reg(3)
    );
\gmux.gm[3].gms.ms_i_1__0\: unisim.vcomponents.LUT4
    generic map(
      INIT => X"9009"
    )
        port map (
      I0 => p_25_out(7),
      I1 => \gic0.gc0.count_reg[9]\(6),
      I2 => p_25_out(8),
      I3 => \gic0.gc0.count_reg[9]\(7),
      O => v1_reg_0(3)
    );
\gmux.gm[4].gms.ms_i_1\: unisim.vcomponents.LUT4
    generic map(
      INIT => X"9009"
    )
        port map (
      I0 => p_25_out(9),
      I1 => Q(8),
      I2 => p_25_out(10),
      I3 => Q(9),
      O => v1_reg(4)
    );
\gmux.gm[4].gms.ms_i_1__0\: unisim.vcomponents.LUT4
    generic map(
      INIT => X"9009"
    )
        port map (
      I0 => p_25_out(9),
      I1 => \gic0.gc0.count_reg[9]\(8),
      I2 => p_25_out(10),
      I3 => \gic0.gc0.count_reg[9]\(9),
      O => v1_reg_0(4)
    );
\gmux.gm[5].gms.ms_i_1\: unisim.vcomponents.LUT2
    generic map(
      INIT => X"9"
    )
        port map (
      I0 => p_24_out(9),
      I1 => \gc0.count_d1_reg[10]\(10),
      O => v1_reg_1(0)
    );
\gmux.gm[5].gms.ms_i_1__0\: unisim.vcomponents.LUT2
    generic map(
      INIT => X"9"
    )
        port map (
      I0 => p_24_out(9),
      I1 => \gc0.count_reg[10]\(0),
      O => v1_reg_2(0)
    );
rd_pntr_cdc_inst: entity work.\FPGAtoFTDI_fifo_xpm_cdc_gray__parameterized0\
     port map (
      dest_clk => wr_clk,
      dest_out_bin(10 downto 0) => p_25_out(10 downto 0),
      src_clk => rd_clk,
      src_in_bin(10 downto 0) => \gc0.count_d1_reg[10]\(10 downto 0)
    );
wr_pntr_cdc_inst: entity work.FPGAtoFTDI_fifo_xpm_cdc_gray
     port map (
      dest_clk => rd_clk,
      dest_out_bin(9) => p_24_out(9),
      dest_out_bin(8 downto 0) => WR_PNTR_RD(8 downto 0),
      src_clk => wr_clk,
      src_in_bin(9 downto 0) => \gic0.gc0.count_d2_reg[9]\(9 downto 0)
    );
end STRUCTURE;
library IEEE;
use IEEE.STD_LOGIC_1164.ALL;
library UNISIM;
use UNISIM.VCOMPONENTS.ALL;
entity FPGAtoFTDI_fifo_rd_status_flags_as is
  port (
    empty : out STD_LOGIC;
    tmp_ram_rd_en : out STD_LOGIC;
    E : out STD_LOGIC_VECTOR ( 0 to 0 );
    v1_reg : in STD_LOGIC_VECTOR ( 4 downto 0 );
    \dest_out_bin_ff_reg[9]\ : in STD_LOGIC_VECTOR ( 0 to 0 );
    v1_reg_0 : in STD_LOGIC_VECTOR ( 4 downto 0 );
    \dest_out_bin_ff_reg[9]_0\ : in STD_LOGIC_VECTOR ( 0 to 0 );
    rd_clk : in STD_LOGIC;
    AR : in STD_LOGIC_VECTOR ( 0 to 0 );
    rd_en : in STD_LOGIC
  );
  attribute ORIG_REF_NAME : string;
  attribute ORIG_REF_NAME of FPGAtoFTDI_fifo_rd_status_flags_as : entity is "rd_status_flags_as";
end FPGAtoFTDI_fifo_rd_status_flags_as;

architecture STRUCTURE of FPGAtoFTDI_fifo_rd_status_flags_as is
  signal c0_n_0 : STD_LOGIC;
  signal comp1 : STD_LOGIC;
  signal ram_empty_fb_i : STD_LOGIC;
  attribute DONT_TOUCH : boolean;
  attribute DONT_TOUCH of ram_empty_fb_i : signal is std.standard.true;
  signal ram_empty_i : STD_LOGIC;
  attribute DONT_TOUCH of ram_empty_i : signal is std.standard.true;
  attribute DONT_TOUCH of ram_empty_fb_i_reg : label is std.standard.true;
  attribute KEEP : string;
  attribute KEEP of ram_empty_fb_i_reg : label is "yes";
  attribute equivalent_register_removal : string;
  attribute equivalent_register_removal of ram_empty_fb_i_reg : label is "no";
  attribute DONT_TOUCH of ram_empty_i_reg : label is std.standard.true;
  attribute KEEP of ram_empty_i_reg : label is "yes";
  attribute equivalent_register_removal of ram_empty_i_reg : label is "no";
begin
  empty <= ram_empty_i;
\DEVICE_7SERIES.NO_BMM_INFO.SDP.SIMPLE_PRIM18.ram_i_2\: unisim.vcomponents.LUT3
    generic map(
      INIT => X"F4"
    )
        port map (
      I0 => ram_empty_fb_i,
      I1 => rd_en,
      I2 => AR(0),
      O => tmp_ram_rd_en
    );
c0: entity work.FPGAtoFTDI_fifo_compare
     port map (
      comp1 => comp1,
      \dest_out_bin_ff_reg[9]\(0) => \dest_out_bin_ff_reg[9]\(0),
      \out\ => ram_empty_fb_i,
      ram_empty_fb_i_reg => c0_n_0,
      rd_en => rd_en,
      v1_reg(4 downto 0) => v1_reg(4 downto 0)
    );
c1: entity work.FPGAtoFTDI_fifo_compare_1
     port map (
      comp1 => comp1,
      \dest_out_bin_ff_reg[9]\(0) => \dest_out_bin_ff_reg[9]_0\(0),
      v1_reg_0(4 downto 0) => v1_reg_0(4 downto 0)
    );
\gc0.count_d1[10]_i_1\: unisim.vcomponents.LUT2
    generic map(
      INIT => X"2"
    )
        port map (
      I0 => rd_en,
      I1 => ram_empty_fb_i,
      O => E(0)
    );
ram_empty_fb_i_reg: unisim.vcomponents.FDPE
    generic map(
      INIT => '1'
    )
        port map (
      C => rd_clk,
      CE => '1',
      D => c0_n_0,
      PRE => AR(0),
      Q => ram_empty_fb_i
    );
ram_empty_i_reg: unisim.vcomponents.FDPE
    generic map(
      INIT => '1'
    )
        port map (
      C => rd_clk,
      CE => '1',
      D => c0_n_0,
      PRE => AR(0),
      Q => ram_empty_i
    );
end STRUCTURE;
library IEEE;
use IEEE.STD_LOGIC_1164.ALL;
library UNISIM;
use UNISIM.VCOMPONENTS.ALL;
entity FPGAtoFTDI_fifo_reset_blk_ramfifo is
  port (
    AR : out STD_LOGIC_VECTOR ( 0 to 0 );
    \syncstages_ff_reg[0]\ : out STD_LOGIC_VECTOR ( 0 to 0 );
    \out\ : out STD_LOGIC;
    ram_full_fb_i_reg : out STD_LOGIC;
    wr_rst_busy : out STD_LOGIC;
    rst : in STD_LOGIC;
    wr_clk : in STD_LOGIC;
    rd_clk : in STD_LOGIC
  );
  attribute ORIG_REF_NAME : string;
  attribute ORIG_REF_NAME of FPGAtoFTDI_fifo_reset_blk_ramfifo : entity is "reset_blk_ramfifo";
end FPGAtoFTDI_fifo_reset_blk_ramfifo;
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
