mfkiwl/SDR-R/fpga-src/sources_1/ip/c_counter_binary_0/c_counter_binary_0_sim_netlist.v

// Copyright 1986-2018 Xilinx, Inc. All Rights Reserved.
// --------------------------------------------------------------------------------
// Tool Version: Vivado v.2018.2.2 (win64) Build 2348494 Mon Oct  1 18:25:44 MDT 2018
// Date        : Wed May 15 18:44:14 2019
// Host        : DESKTOP-4O36AQC running 64-bit major release  (build 9200)
// Command     : write_verilog -force -mode funcsim
//               c:/Users/Guy/Desktop/UMBC/2019_Spring/451/SDRR_FINAL/SDRR_FINAL.srcs/sources_1/ip/c_counter_binary_0/c_counter_binary_0_sim_netlist.v
// Design      : c_counter_binary_0
// Purpose     : This verilog netlist is a functional simulation representation of the design and should not be modified
//               or synthesized. This netlist cannot be used for SDF annotated simulation.
// Device      : xc7a15tcpg236-1
// --------------------------------------------------------------------------------
`timescale 1 ps / 1 ps

(* CHECK_LICENSE_TYPE = "c_counter_binary_0,c_counter_binary_v12_0_12,{}" *) (* downgradeipidentifiedwarnings = "yes" *) (* x_core_info = "c_counter_binary_v12_0_12,Vivado 2018.2.2" *) 
(* NotValidForBitStream *)
module c_counter_binary_0
   (CLK,
    SCLR,
    Q);
  (* x_interface_info = "xilinx.com:signal:clock:1.0 clk_intf CLK" *) (* x_interface_parameter = "XIL_INTERFACENAME clk_intf, ASSOCIATED_BUSIF q_intf:thresh0_intf:l_intf:load_intf:up_intf:sinit_intf:sset_intf, ASSOCIATED_RESET SCLR, ASSOCIATED_CLKEN CE, FREQ_HZ 10000000, PHASE 0.000" *) input CLK;
  (* x_interface_info = "xilinx.com:signal:reset:1.0 sclr_intf RST" *) (* x_interface_parameter = "XIL_INTERFACENAME sclr_intf, POLARITY ACTIVE_HIGH" *) input SCLR;
  (* x_interface_info = "xilinx.com:signal:data:1.0 q_intf DATA" *) (* x_interface_parameter = "XIL_INTERFACENAME q_intf, LAYERED_METADATA undef" *) output [9:0]Q;

  wire CLK;
  wire [9:0]Q;
  wire SCLR;
  wire NLW_U0_THRESH0_UNCONNECTED;

  (* C_AINIT_VAL = "0" *) 
  (* C_CE_OVERRIDES_SYNC = "0" *) 
  (* C_COUNT_BY = "1" *) 
  (* C_COUNT_MODE = "0" *) 
  (* C_COUNT_TO = "1" *) 
  (* C_FB_LATENCY = "0" *) 
  (* C_HAS_CE = "0" *) 
  (* C_HAS_LOAD = "0" *) 
  (* C_HAS_SCLR = "1" *) 
  (* C_HAS_SINIT = "0" *) 
  (* C_HAS_SSET = "0" *) 
  (* C_HAS_THRESH0 = "0" *) 
  (* C_IMPLEMENTATION = "1" *) 
  (* C_LATENCY = "1" *) 
  (* C_LOAD_LOW = "0" *) 
  (* C_RESTRICT_COUNT = "0" *) 
  (* C_SCLR_OVERRIDES_SSET = "1" *) 
  (* C_SINIT_VAL = "0" *) 
  (* C_THRESH0_VALUE = "1" *) 
  (* C_VERBOSITY = "0" *) 
  (* C_WIDTH = "10" *) 
  (* C_XDEVICEFAMILY = "artix7" *) 
  (* downgradeipidentifiedwarnings = "yes" *) 
  c_counter_binary_0_c_counter_binary_v12_0_12 U0
       (.CE(1'b1),
        .CLK(CLK),
        .L({1'b0,1'b0,1'b0,1'b0,1'b0,1'b0,1'b0,1'b0,1'b0,1'b0}),
        .LOAD(1'b0),
        .Q(Q),
        .SCLR(SCLR),
        .SINIT(1'b0),
        .SSET(1'b0),
        .THRESH0(NLW_U0_THRESH0_UNCONNECTED),
        .UP(1'b1));
endmodule

(* C_AINIT_VAL = "0" *) (* C_CE_OVERRIDES_SYNC = "0" *) (* C_COUNT_BY = "1" *) 
(* C_COUNT_MODE = "0" *) (* C_COUNT_TO = "1" *) (* C_FB_LATENCY = "0" *) 
(* C_HAS_CE = "0" *) (* C_HAS_LOAD = "0" *) (* C_HAS_SCLR = "1" *) 
(* C_HAS_SINIT = "0" *) (* C_HAS_SSET = "0" *) (* C_HAS_THRESH0 = "0" *) 
(* C_IMPLEMENTATION = "1" *) (* C_LATENCY = "1" *) (* C_LOAD_LOW = "0" *) 
(* C_RESTRICT_COUNT = "0" *) (* C_SCLR_OVERRIDES_SSET = "1" *) (* C_SINIT_VAL = "0" *) 
(* C_THRESH0_VALUE = "1" *) (* C_VERBOSITY = "0" *) (* C_WIDTH = "10" *) 
(* C_XDEVICEFAMILY = "artix7" *) (* ORIG_REF_NAME = "c_counter_binary_v12_0_12" *) (* downgradeipidentifiedwarnings = "yes" *) 
module c_counter_binary_0_c_counter_binary_v12_0_12
   (CLK,
    CE,
    SCLR,
    SSET,
    SINIT,
    UP,
    LOAD,
    L,
    THRESH0,
    Q);
  input CLK;
  input CE;
  input SCLR;
  input SSET;
  input SINIT;
  input UP;
  input LOAD;
  input [9:0]L;
  output THRESH0;
  output [9:0]Q;

  wire \<const1> ;
  wire CLK;
  wire [9:0]L;
  wire [9:0]Q;
  wire SCLR;
  wire NLW_i_synth_THRESH0_UNCONNECTED;

  assign THRESH0 = \<const1> ;
  VCC VCC
       (.P(\<const1> ));
  (* C_AINIT_VAL = "0" *) 
  (* C_CE_OVERRIDES_SYNC = "0" *) 
  (* C_COUNT_BY = "1" *) 
  (* C_COUNT_MODE = "0" *) 
  (* C_COUNT_TO = "1" *) 
  (* C_FB_LATENCY = "0" *) 
  (* C_HAS_CE = "0" *) 
  (* C_HAS_LOAD = "0" *) 
  (* C_HAS_SCLR = "1" *) 
  (* C_HAS_SINIT = "0" *) 
  (* C_HAS_SSET = "0" *) 
  (* C_HAS_THRESH0 = "0" *) 
  (* C_IMPLEMENTATION = "1" *) 
  (* C_LATENCY = "1" *) 
  (* C_LOAD_LOW = "0" *) 
  (* C_RESTRICT_COUNT = "0" *) 
  (* C_SCLR_OVERRIDES_SSET = "1" *) 
  (* C_SINIT_VAL = "0" *) 
  (* C_THRESH0_VALUE = "1" *) 
  (* C_VERBOSITY = "0" *) 
  (* C_WIDTH = "10" *) 
  (* C_XDEVICEFAMILY = "artix7" *) 
  (* downgradeipidentifiedwarnings = "yes" *) 
  c_counter_binary_0_c_counter_binary_v12_0_12_viv i_synth
       (.CE(1'b0),
        .CLK(CLK),
        .L(L),
        .LOAD(1'b0),
        .Q(Q),
        .SCLR(SCLR),
        .SINIT(1'b0),
        .SSET(1'b0),
        .THRESH0(NLW_i_synth_THRESH0_UNCONNECTED),
        .UP(1'b0));
endmodule
`pragma protect begin_protected
`pragma protect version = 1
`pragma protect encrypt_agent = "XILINX"
`pragma protect encrypt_agent_info = "Xilinx Encryption Tool 2015"
`pragma protect key_keyowner="Cadence Design Systems.", key_keyname="cds_rsa_key", key_method="rsa"
`pragma protect encoding = (enctype="BASE64", line_length=76, bytes=64)
`pragma protect key_block
kfi029mOwVaAexw2bRh3FaYGJRTc5bG/7m5UbBrHjD+cYKYlNVTn+xX1sqkCm+iSza4kZ+TkPquh
v/Bl3NP8IQ==

`pragma protect key_keyowner="Synopsys", key_keyname="SNPS-VCS-RSA-2", key_method="rsa"
`pragma protect encoding = (enctype="BASE64", line_length=76, bytes=128)
`pragma protect key_block
JxCFWcdXC3xLmRSmBA3FzGUlrmxUZneu/utMrbWHF36ASvctamIyzdarXyNgv0aZPklDBnhFgNu+
rdUqubRvo+ChN8q464n/cn/OU8M9vhhlwPdWZuqfiDinHD0UZUTfUoBcHYK1TxMor2VStyPA4AT5
yZZlFdfP/MAFfHFkTKY=

`pragma protect key_keyowner="Aldec", key_keyname="ALDEC15_001", key_method="rsa"
`pragma protect encoding = (enctype="BASE64", line_length=76, bytes=256)
`pragma protect key_block
1yWdSHPSFnMeKQJoCTsGuiLL0ZHvrx1TrwVn0GWHe6Acr1Dx0P7P8ZYIxWtkfF1YuxD50E3pCXXP
7QdnFTeGdJSUHyC7340PMORTAhBZoHhmb1fKB7K8GCXnsL2BM5oQqDrLA2DfJJ2U1gWog/H7QLp5
23bfkZacfT7XCkhb4b/bYUUxbA88Bk9rpZF/eDHEYhhgxbpyUW5JuOkws7SVQwT2ldD6g3rnjgix
XGErVwYQhLYKRraQj1N02cdafgj94EqbnxC3TnoW9TLvKxHS3/8wGdcpMngZ7fY6LuDAxlNazfRI
CO20GeeomnBj4pBNxWG9oWIUXTZdqCsb62Y5Nw==

`pragma protect key_keyowner="ATRENTA", key_keyname="ATR-SG-2015-RSA-3", key_method="rsa"
`pragma protect encoding = (enctype="BASE64", line_length=76, bytes=256)
`pragma protect key_block
g7hlFmGTS+XVOdK+WtfQGihndYfR5S97YIvDLXzeoj/KHE8qyLpZqQ7at9cNHuOHC+xVk4OCpmjx
HZTFiDMP83uOCtl/lM5jOKsvEwC05dPzn2c6D3KUVvFGx7P00w40S43lOeC6rWCkMF2mLxI+9z2n
26CjxvSDukMD4/zqgbl2EkTKMuQ2ck/INBmCs1MHkkQjQbUhBiIlcrbVxiQGl3jOp66u17H8VKDz
dpRHj+MgrB/q7qVU+71D2TJjseYxT7oWGUJeYjvGK6aH11dpVelnEpWcWLlvPbogWRHar1oaSZPD
hjDPwujxH6eLiDIPzMtcO3Aud4nhKF1DRH021Q==

`pragma protect key_keyowner="Xilinx", key_keyname="xilinxt_2017_05", key_method="rsa"
`pragma protect encoding = (enctype="BASE64", line_length=76, bytes=256)
`pragma protect key_block
qDVS8yp0Hz/d9umzgDI4Qy4tfjNqsAx55hcL0bayLQwhE0tUYxkdob1ZpMAQjZUMOG+33AUE7bcv
EmEgmNzSFvgtePKWmartlwQV8c4AVZLs1m+ZzKHDdke4zWmAYj2OD32a3IfANsmnZ5iM8i+n0iK8
RgC94/l9aM08szmMx5rprkKlS+0gty7OBKWhkPHXsfcyo+DX2Bfscrp9wdC/wA6IVm/DcFO7bNlu
zX6F3GZ0r3b7q8M4IqtCUV0qkvl75pvGiGQjH2jWAZHjDoo+BQe6vqOmyiYDfTWpWY+AphRGxkB9
tKiNbKOOr0iABX9g/QQhnwmmMp896DCuXISbtA==

`pragma protect key_keyowner="Mentor Graphics Corporation", key_keyname="MGC-VELOCE-RSA", key_method="rsa"
`pragma protect encoding = (enctype="BASE64", line_length=76, bytes=128)
`pragma protect key_block
FKcUrAaKeh7vQMZ5PAkg8M2YlwpOs68g8WGncL2egAQF3KwczRSEzhYOmfvGUXBHW3mh2pquNEb2
OooUhLgw8alMYDIvNIwGRpVKO7l64Y+JA9que0oKXpoeW6ElFdIqEcD2dOE5BzDNqAIzOPDuXN9M
ngjt5qGrMHaw5yTYMfQ=

`pragma protect key_keyowner="Mentor Graphics Corporation", key_keyname="MGC-VERIF-SIM-RSA-2", key_method="rsa"
`pragma protect encoding = (enctype="BASE64", line_length=76, bytes=256)
`pragma protect key_block
URYhWe83nVILty6DlJMXGIlVnsNR+u6saIMUTTGmEX44dK8vZ6MGokTk0vsAoq+SxuPxmwI/y3/D
VfBFq6zKSSwJYV8gi80EPec0zA18G+GNqag0J8wB931PwddtFMYcdKT9gjIM9iPUsyZpkPHZ4BaM
SsBY71714eyb4JbLYTB6brsK81Xf1lAsGueALMp4TfGhhJX+dYFpexZPyXlq8rYRFZcUCN/SDO2A
R7AVZHQ1OQ988E2wTPfkwkOkaMjae5jh2nFh1llipaEYmhWxIY5Pl+hzADlELU5DtAh7Q6xUbL/2
aByFdbrnDGm3vuDP9q62FRO7aUagiRBVt6fXPA==

`pragma protect key_keyowner="Mentor Graphics Corporation", key_keyname="MGC-PREC-RSA", key_method="rsa"
`pragma protect encoding = (enctype="BASE64", line_length=76, bytes=256)
`pragma protect key_block
NcvhnlM6SJF9a3c0ITFidXLoJoB37BNuzBzRuH0byeljlP0FljU3VSNPVHJAd009s9GKaYhF58u6
Lh0jD2zbg7K4MZYK4db1QHawROq+NIxtjM7nV+O9bYuy6favHZjg88nAv4MVRrZdOxesvP6Y8K4u
hDdaQHn3tm1ZXpfpQoGnWw5jNGRXZwaIWt1oF6s1EvZEJanpi9sXMXCtL8KP7zEBPDd++raSZXPH
uA1zP+xe4ElW72ZnkQl6cOaHHRQxbOSn6XJW9L0G7qXxj8cMAJ5RVJry0HbJ6i4m8x2D2sWloz/J
T8DNVBu3W9m+/S6TG8oIPdMs6VT3kuMhdB5RVg==

`pragma protect key_keyowner="Synplicity", key_keyname="SYNP15_1", key_method="rsa"
`pragma protect encoding = (enctype="BASE64", line_length=76, bytes=256)
`pragma protect key_block
LFKIrkY7boUrLyBSUIsn4jR6WFWzLd+Q+Q6qh/Vzzr00zrqS6+7xuFL4UnR5mST3ftO+n4jAqLXh
dn4V5viZNE7phP61ojN5GciObj1kceenzzCBAHHr7nR0HTu3k7i2sbYf8FYUQJ43/qliZDWn4wvS
A8oV8eG+iSeJdOJp+EZW1sc6djQWAMxR7efYr+1X1aEK+QPe5klrXJNmr48RMRLQAha2hTxxSp/E
BTvbtb3m0fqT+FQv6pcDkH4o0PLm76Al5+rZYKjaQnITRVP7/Wd77zXnwvlT68y2kzptC1ajTy/X
9/eP3EPVOusL2LS4bfLlcfhtnp4q2WrkTvPkKQ==

`pragma protect data_method = "AES128-CBC"
`pragma protect encoding = (enctype = "BASE64", line_length = 76, bytes = 11696)
`pragma protect data_block
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
12cv4tUYp8L7ap0=
`pragma protect end_protected
`ifndef GLBL
`define GLBL
`timescale  1 ps / 1 ps

module glbl ();

    parameter ROC_WIDTH = 100000;
    parameter TOC_WIDTH = 0;

//--------   STARTUP Globals --------------
    wire GSR;
    wire GTS;
    wire GWE;
    wire PRLD;
    tri1 p_up_tmp;
    tri (weak1, strong0) PLL_LOCKG = p_up_tmp;

    wire PROGB_GLBL;
    wire CCLKO_GLBL;
    wire FCSBO_GLBL;
    wire [3:0] DO_GLBL;
    wire [3:0] DI_GLBL;
   
    reg GSR_int;
    reg GTS_int;
    reg PRLD_int;

//--------   JTAG Globals --------------
    wire JTAG_TDO_GLBL;
    wire JTAG_TCK_GLBL;
    wire JTAG_TDI_GLBL;
    wire JTAG_TMS_GLBL;
    wire JTAG_TRST_GLBL;

    reg JTAG_CAPTURE_GLBL;
    reg JTAG_RESET_GLBL;
    reg JTAG_SHIFT_GLBL;
    reg JTAG_UPDATE_GLBL;
    reg JTAG_RUNTEST_GLBL;

    reg JTAG_SEL1_GLBL = 0;
    reg JTAG_SEL2_GLBL = 0 ;
    reg JTAG_SEL3_GLBL = 0;
    reg JTAG_SEL4_GLBL = 0;

    reg JTAG_USER_TDO1_GLBL = 1'bz;
    reg JTAG_USER_TDO2_GLBL = 1'bz;
    reg JTAG_USER_TDO3_GLBL = 1'bz;
    reg JTAG_USER_TDO4_GLBL = 1'bz;

    assign (strong1, weak0) GSR = GSR_int;
    assign (strong1, weak0) GTS = GTS_int;
    assign (weak1, weak0) PRLD = PRLD_int;

    initial begin
	GSR_int = 1'b1;
	PRLD_int = 1'b1;
	#(ROC_WIDTH)
	GSR_int = 1'b0;
	PRLD_int = 1'b0;
    end

    initial begin
	GTS_int = 1'b1;
	#(TOC_WIDTH)
	GTS_int = 1'b0;
    end

endmodule
`endif
