mfkiwl/SDR-R/fpga-src/sources_1/ip/c_counter_binary_0/c_counter_binary_0_sim_netlist.vhdl

-- Copyright 1986-2018 Xilinx, Inc. All Rights Reserved.
-- --------------------------------------------------------------------------------
-- Tool Version: Vivado v.2018.2.2 (win64) Build 2348494 Mon Oct  1 18:25:44 MDT 2018
-- Date        : Wed May 15 18:44:14 2019
-- Host        : DESKTOP-4O36AQC running 64-bit major release  (build 9200)
-- Command     : write_vhdl -force -mode funcsim
--               c:/Users/Guy/Desktop/UMBC/2019_Spring/451/SDRR_FINAL/SDRR_FINAL.srcs/sources_1/ip/c_counter_binary_0/c_counter_binary_0_sim_netlist.vhdl
-- Design      : c_counter_binary_0
-- Purpose     : This VHDL netlist is a functional simulation representation of the design and should not be modified or
--               synthesized. This netlist cannot be used for SDF annotated simulation.
-- Device      : xc7a15tcpg236-1
-- --------------------------------------------------------------------------------
`protect begin_protected
`protect version = 1
`protect encrypt_agent = "XILINX"
`protect encrypt_agent_info = "Xilinx Encryption Tool 2015"
`protect key_keyowner="Cadence Design Systems.", key_keyname="cds_rsa_key", key_method="rsa"
`protect encoding = (enctype="BASE64", line_length=76, bytes=64)
`protect key_block
YNLWGD0i7x4Luf3Kb1nt8rV4yWtJLLeagRgR3BWcdiLA1Bf3PDRR1d99wdZorVCWW7j75Z0IJV2w
BLbcu1z+tw==

`protect key_keyowner="Synopsys", key_keyname="SNPS-VCS-RSA-2", key_method="rsa"
`protect encoding = (enctype="BASE64", line_length=76, bytes=128)
`protect key_block
BV5oR0TaRaPMnh9abEXwWFeWoCP/kjtCvhXmZ2Ch0hsgjYpdtxKPdS5JAG85EwJkG9Um8wCP4fmQ
KsG/4bv/L4XbCnkHlErkVxA2t1RFKuixCaDuo9T0+NEwKjGoMbWBTYrSE5zXk6HU9HYOJ3OcTYEG
f46Kq2RsRV78oCY/JSE=

`protect key_keyowner="Aldec", key_keyname="ALDEC15_001", key_method="rsa"
`protect encoding = (enctype="BASE64", line_length=76, bytes=256)
`protect key_block
svNAK+4lbGaEYTJjSxKewpvQJXVx6cCxkrxJrua3L0nOXKJb8P05WZ77H3tFvsgqxt1Aw8r7HGpc
5NDmkfvyHdOh/CtT6LFXB7WOJ65V2MCgx0ysvgLowhNDb54VxFtWeFjLLg06PqFE9dOw5KX25FNI
vpJyH9SmH8hcn6oSjK7AtddBnsDSZWhEPCLDzcEXAFFqnUo2jLJtBRPpKhsrn+J5VKXH+e7VHzLN
MPH7lB4exB0YtpyIKgnxMDj2lWCQfeCAIbAMg9zd1b66y5K9Iz03hDWEOE/hPFHm3d5yQeemMzIC
Z4kSlnMJWL90m08bR+OFG4YdoQDZSbWbUaawKg==

`protect key_keyowner="ATRENTA", key_keyname="ATR-SG-2015-RSA-3", key_method="rsa"
`protect encoding = (enctype="BASE64", line_length=76, bytes=256)
`protect key_block
udGuwrgNhtm6NxHrkt7+6GbPpuYTLAPgzXizF4uNQRz+BZOq0xfCP+xt8DvWRfO8iwt0VLm76P7E
qZ+GBYk1KVZxhLe+Ft9fKXZC5nMh2EThb1uL1mOAsTpErQVla70pezCuBceygMGfnWuRXYbC3oco
13dRs0SZZqhTBaPzxeeXH0WYhIqI/zSYUKBxiV1FW2mqsjx0RjOlgcUCM7e8JcPTdVSrQPz/ODe0
QZIVSR15fo1J1I2y9J+dGfy/gR1148DWRPgkLKYlvhLShVi09ulIuOG/p0ifub9C4w8uYvpYihFK
ZRmK7hnFs8zod0OIUmZ0PhKJN2+UAuMrHG/4KQ==

`protect key_keyowner="Xilinx", key_keyname="xilinxt_2017_05", key_method="rsa"
`protect encoding = (enctype="BASE64", line_length=76, bytes=256)
`protect key_block
s8lCm5p3ommwSYkR//pixw+u8YtOC7N4ySJ0/FG4dPJ3nfe5bUNOtwKH5pZ6mKkh+f+f3uKaSmOv
S6ExBzmunJuMa803YvGhR0H9fvGuMIgPN6ygBpWA4ETsOvrvkAWG75lTvm9W0s6soh22/acA4943
vRplx1uK0f+c7GICGNdk7+FxDR7IQkVgV8ZI0Zc7x+zipGjp/Au60TJhMuDiO4Z0oga1MPfrX0/d
dD/wn24qwkhyL0nmhv0fPyuxe+BCpaC8S2Z+vjn58Odf2+v+Zt3PuWu3KlxISRwy5F0lz/Jk2yjs
0wIT6/b+F0dC0oVgallJa3HkjrFeq+BablJPOg==

`protect key_keyowner="Mentor Graphics Corporation", key_keyname="MGC-VELOCE-RSA", key_method="rsa"
`protect encoding = (enctype="BASE64", line_length=76, bytes=128)
`protect key_block
h4FTd9nkYyO6VBHZJ+ndjhT+pF3dIfAGBExn2ssEopuet674a/8U6bxGrV6lMrVpmsvnbC3yxSRF
uriBV58D7vTFFEdE86l8H97tkIVbNsMUPZTIppjPaE7MJ8dmIWID5rlKMaaxfNM8Y6y0hSzfSxUI
hp6vKsR/HMYFjkoYqiE=

`protect key_keyowner="Mentor Graphics Corporation", key_keyname="MGC-VERIF-SIM-RSA-2", key_method="rsa"
`protect encoding = (enctype="BASE64", line_length=76, bytes=256)
`protect key_block
QgEaefFkPBaTVY+qhVJVhf/XD3oeN/p6cJLU4gWUUuYxa/QcVPFgIkZJTcF9kJKox1xRvhusF+lt
Pni9IeJruOHgBH33Nk9rsQsOh37Do0fg8oUidXCt52AYcZg/e8T03rON07LJePJz3e5JbPxaBiWY
LVY0hVFPJ7SN5TqfUqspJZYLxqtbXa7dlDViJtQG2GCyOYi/5Fa34gt3rmjZZFlfUUPRAkr4Rz8L
0wzmv0VwEE6EeN69yFlegy3eTG82n2DsAyCMn1mXN+h6SLm93pypE39O8A5z5x0nDFjx3z3kfvaX
Yy6o91LgleuoSLkQq5FMe8LphEwDyxJe2j4IgA==

`protect key_keyowner="Mentor Graphics Corporation", key_keyname="MGC-PREC-RSA", key_method="rsa"
`protect encoding = (enctype="BASE64", line_length=76, bytes=256)
`protect key_block
ZZNKXMFO6wMzEQAeJ7LGT6A6DRGw2FsS+SX0JWTQfIsWuK61P54mPi+d6ICEPZ+rfkb26iV/64dW
a1OezoCLEgzTvmSa8rknTRI0qWX/ca+rCoG1wCkQEu+6eQ1je+kl45NHFChln/vXSAIe9p57heyD
VR+BjZmsoYvdB/i6ASndePgL8ONr+thLr+XdTf34RHmghFujlwr54YCTkGdu5HjcF2HSQV+f7mwZ
ertVSvST2nWmk3MCLpmhMaDufx2LrY+pbR7l/Wd6mSf/uPTuhKZtCMpUbF6bYsuDLsKDgQTZI/Eo
9jczxFVflPyFL3yo4xhxlgwtx54dLBKm//rN3g==

`protect key_keyowner="Synplicity", key_keyname="SYNP15_1", key_method="rsa"
`protect encoding = (enctype="BASE64", line_length=76, bytes=256)
`protect key_block
2XioPi1JfoyCAo9EMCKpLRhGgNJYUCwESIlUfnqqBYd1b54qX8RvRaCAr6KFaFmLLPf9V/Ryrp5k
UOrpZrvrISDN3NgOrOqA929xhwhw5xGuplli3UQW+L2+SVKQxgPTUvvVFrqnM2xqPa9IAg8HwWPq
4jpAhdjE22fpoHfMEh+9TC9gvH3S36f7H4ZD/iPJDydEwNg83UwJMA24KUJURk2XmRiREjBYBzqa
Wz5KMHudDHuHDIxM6PaKIuhT4yFplqiR/bF7xQxWptFAWmGzfd8x1pAQ4wG/usN7p4Wsn7LT9icJ
TtxlrFyoYvOvrShKH3ko6D7xIFwfMMeLHe/Vkg==

`protect data_method = "AES128-CBC"
`protect encoding = (enctype = "BASE64", line_length = 76, bytes = 19888)
`protect data_block
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
`protect end_protected
library IEEE;
use IEEE.STD_LOGIC_1164.ALL;
library UNISIM;
use UNISIM.VCOMPONENTS.ALL;
entity c_counter_binary_0_c_counter_binary_v12_0_12 is
  port (
    CLK : in STD_LOGIC;
    CE : in STD_LOGIC;
    SCLR : in STD_LOGIC;
    SSET : in STD_LOGIC;
    SINIT : in STD_LOGIC;
    UP : in STD_LOGIC;
    LOAD : in STD_LOGIC;
    L : in STD_LOGIC_VECTOR ( 9 downto 0 );
    THRESH0 : out STD_LOGIC;
    Q : out STD_LOGIC_VECTOR ( 9 downto 0 )
  );
  attribute C_AINIT_VAL : string;
  attribute C_AINIT_VAL of c_counter_binary_0_c_counter_binary_v12_0_12 : entity is "0";
  attribute C_CE_OVERRIDES_SYNC : integer;
  attribute C_CE_OVERRIDES_SYNC of c_counter_binary_0_c_counter_binary_v12_0_12 : entity is 0;
  attribute C_COUNT_BY : string;
  attribute C_COUNT_BY of c_counter_binary_0_c_counter_binary_v12_0_12 : entity is "1";
  attribute C_COUNT_MODE : integer;
  attribute C_COUNT_MODE of c_counter_binary_0_c_counter_binary_v12_0_12 : entity is 0;
  attribute C_COUNT_TO : string;
  attribute C_COUNT_TO of c_counter_binary_0_c_counter_binary_v12_0_12 : entity is "1";
  attribute C_FB_LATENCY : integer;
  attribute C_FB_LATENCY of c_counter_binary_0_c_counter_binary_v12_0_12 : entity is 0;
  attribute C_HAS_CE : integer;
  attribute C_HAS_CE of c_counter_binary_0_c_counter_binary_v12_0_12 : entity is 0;
  attribute C_HAS_LOAD : integer;
  attribute C_HAS_LOAD of c_counter_binary_0_c_counter_binary_v12_0_12 : entity is 0;
  attribute C_HAS_SCLR : integer;
  attribute C_HAS_SCLR of c_counter_binary_0_c_counter_binary_v12_0_12 : entity is 1;
  attribute C_HAS_SINIT : integer;
  attribute C_HAS_SINIT of c_counter_binary_0_c_counter_binary_v12_0_12 : entity is 0;
  attribute C_HAS_SSET : integer;
  attribute C_HAS_SSET of c_counter_binary_0_c_counter_binary_v12_0_12 : entity is 0;
  attribute C_HAS_THRESH0 : integer;
  attribute C_HAS_THRESH0 of c_counter_binary_0_c_counter_binary_v12_0_12 : entity is 0;
  attribute C_IMPLEMENTATION : integer;
  attribute C_IMPLEMENTATION of c_counter_binary_0_c_counter_binary_v12_0_12 : entity is 1;
  attribute C_LATENCY : integer;
  attribute C_LATENCY of c_counter_binary_0_c_counter_binary_v12_0_12 : entity is 1;
  attribute C_LOAD_LOW : integer;
  attribute C_LOAD_LOW of c_counter_binary_0_c_counter_binary_v12_0_12 : entity is 0;
  attribute C_RESTRICT_COUNT : integer;
  attribute C_RESTRICT_COUNT of c_counter_binary_0_c_counter_binary_v12_0_12 : entity is 0;
  attribute C_SCLR_OVERRIDES_SSET : integer;
  attribute C_SCLR_OVERRIDES_SSET of c_counter_binary_0_c_counter_binary_v12_0_12 : entity is 1;
  attribute C_SINIT_VAL : string;
  attribute C_SINIT_VAL of c_counter_binary_0_c_counter_binary_v12_0_12 : entity is "0";
  attribute C_THRESH0_VALUE : string;
  attribute C_THRESH0_VALUE of c_counter_binary_0_c_counter_binary_v12_0_12 : entity is "1";
  attribute C_VERBOSITY : integer;
  attribute C_VERBOSITY of c_counter_binary_0_c_counter_binary_v12_0_12 : entity is 0;
  attribute C_WIDTH : integer;
  attribute C_WIDTH of c_counter_binary_0_c_counter_binary_v12_0_12 : entity is 10;
  attribute C_XDEVICEFAMILY : string;
  attribute C_XDEVICEFAMILY of c_counter_binary_0_c_counter_binary_v12_0_12 : entity is "artix7";
  attribute ORIG_REF_NAME : string;
  attribute ORIG_REF_NAME of c_counter_binary_0_c_counter_binary_v12_0_12 : entity is "c_counter_binary_v12_0_12";
  attribute downgradeipidentifiedwarnings : string;
  attribute downgradeipidentifiedwarnings of c_counter_binary_0_c_counter_binary_v12_0_12 : entity is "yes";
end c_counter_binary_0_c_counter_binary_v12_0_12;

architecture STRUCTURE of c_counter_binary_0_c_counter_binary_v12_0_12 is
  signal \<const1>\ : STD_LOGIC;
  signal NLW_i_synth_THRESH0_UNCONNECTED : STD_LOGIC;
  attribute C_AINIT_VAL of i_synth : label is "0";
  attribute C_CE_OVERRIDES_SYNC of i_synth : label is 0;
  attribute C_COUNT_BY of i_synth : label is "1";
  attribute C_COUNT_MODE of i_synth : label is 0;
  attribute C_COUNT_TO of i_synth : label is "1";
  attribute C_FB_LATENCY of i_synth : label is 0;
  attribute C_HAS_CE of i_synth : label is 0;
  attribute C_HAS_LOAD of i_synth : label is 0;
  attribute C_HAS_SCLR of i_synth : label is 1;
  attribute C_HAS_SINIT of i_synth : label is 0;
  attribute C_HAS_SSET of i_synth : label is 0;
  attribute C_HAS_THRESH0 of i_synth : label is 0;
  attribute C_IMPLEMENTATION of i_synth : label is 1;
  attribute C_LATENCY of i_synth : label is 1;
  attribute C_LOAD_LOW of i_synth : label is 0;
  attribute C_RESTRICT_COUNT of i_synth : label is 0;
  attribute C_SCLR_OVERRIDES_SSET of i_synth : label is 1;
  attribute C_SINIT_VAL of i_synth : label is "0";
  attribute C_THRESH0_VALUE of i_synth : label is "1";
  attribute C_VERBOSITY of i_synth : label is 0;
  attribute C_WIDTH of i_synth : label is 10;
  attribute C_XDEVICEFAMILY of i_synth : label is "artix7";
  attribute downgradeipidentifiedwarnings of i_synth : label is "yes";
begin
  THRESH0 <= \<const1>\;
VCC: unisim.vcomponents.VCC
     port map (
      P => \<const1>\
    );
i_synth: entity work.c_counter_binary_0_c_counter_binary_v12_0_12_viv
     port map (
      CE => '0',
      CLK => CLK,
      L(9 downto 0) => L(9 downto 0),
      LOAD => '0',
      Q(9 downto 0) => Q(9 downto 0),
      SCLR => SCLR,
      SINIT => '0',
      SSET => '0',
      THRESH0 => NLW_i_synth_THRESH0_UNCONNECTED,
      UP => '0'
    );
end STRUCTURE;
library IEEE;
use IEEE.STD_LOGIC_1164.ALL;
library UNISIM;
use UNISIM.VCOMPONENTS.ALL;
entity c_counter_binary_0 is
  port (
    CLK : in STD_LOGIC;
    SCLR : in STD_LOGIC;
    Q : out STD_LOGIC_VECTOR ( 9 downto 0 )
  );
  attribute NotValidForBitStream : boolean;
  attribute NotValidForBitStream of c_counter_binary_0 : entity is true;
  attribute CHECK_LICENSE_TYPE : string;
  attribute CHECK_LICENSE_TYPE of c_counter_binary_0 : entity is "c_counter_binary_0,c_counter_binary_v12_0_12,{}";
  attribute downgradeipidentifiedwarnings : string;
  attribute downgradeipidentifiedwarnings of c_counter_binary_0 : entity is "yes";
  attribute x_core_info : string;
  attribute x_core_info of c_counter_binary_0 : entity is "c_counter_binary_v12_0_12,Vivado 2018.2.2";
end c_counter_binary_0;

architecture STRUCTURE of c_counter_binary_0 is
  signal NLW_U0_THRESH0_UNCONNECTED : STD_LOGIC;
  attribute C_AINIT_VAL : string;
  attribute C_AINIT_VAL of U0 : label is "0";
  attribute C_CE_OVERRIDES_SYNC : integer;
  attribute C_CE_OVERRIDES_SYNC of U0 : label is 0;
  attribute C_COUNT_BY : string;
  attribute C_COUNT_BY of U0 : label is "1";
  attribute C_COUNT_MODE : integer;
  attribute C_COUNT_MODE of U0 : label is 0;
  attribute C_COUNT_TO : string;
  attribute C_COUNT_TO of U0 : label is "1";
  attribute C_FB_LATENCY : integer;
  attribute C_FB_LATENCY of U0 : label is 0;
  attribute C_HAS_CE : integer;
  attribute C_HAS_CE of U0 : label is 0;
  attribute C_HAS_LOAD : integer;
  attribute C_HAS_LOAD of U0 : label is 0;
  attribute C_HAS_SCLR : integer;
  attribute C_HAS_SCLR of U0 : label is 1;
  attribute C_HAS_SINIT : integer;
  attribute C_HAS_SINIT of U0 : label is 0;
  attribute C_HAS_SSET : integer;
  attribute C_HAS_SSET of U0 : label is 0;
  attribute C_HAS_THRESH0 : integer;
  attribute C_HAS_THRESH0 of U0 : label is 0;
  attribute C_IMPLEMENTATION : integer;
  attribute C_IMPLEMENTATION of U0 : label is 1;
  attribute C_LATENCY : integer;
  attribute C_LATENCY of U0 : label is 1;
  attribute C_LOAD_LOW : integer;
  attribute C_LOAD_LOW of U0 : label is 0;
  attribute C_RESTRICT_COUNT : integer;
  attribute C_RESTRICT_COUNT of U0 : label is 0;
  attribute C_SCLR_OVERRIDES_SSET : integer;
  attribute C_SCLR_OVERRIDES_SSET of U0 : label is 1;
  attribute C_SINIT_VAL : string;
  attribute C_SINIT_VAL of U0 : label is "0";
  attribute C_THRESH0_VALUE : string;
  attribute C_THRESH0_VALUE of U0 : label is "1";
  attribute C_VERBOSITY : integer;
  attribute C_VERBOSITY of U0 : label is 0;
  attribute C_WIDTH : integer;
  attribute C_WIDTH of U0 : label is 10;
  attribute C_XDEVICEFAMILY : string;
  attribute C_XDEVICEFAMILY of U0 : label is "artix7";
  attribute downgradeipidentifiedwarnings of U0 : label is "yes";
  attribute x_interface_info : string;
  attribute x_interface_info of CLK : signal is "xilinx.com:signal:clock:1.0 clk_intf CLK";
  attribute x_interface_parameter : string;
  attribute x_interface_parameter of CLK : signal is "XIL_INTERFACENAME clk_intf, ASSOCIATED_BUSIF q_intf:thresh0_intf:l_intf:load_intf:up_intf:sinit_intf:sset_intf, ASSOCIATED_RESET SCLR, ASSOCIATED_CLKEN CE, FREQ_HZ 10000000, PHASE 0.000";
  attribute x_interface_info of SCLR : signal is "xilinx.com:signal:reset:1.0 sclr_intf RST";
  attribute x_interface_parameter of SCLR : signal is "XIL_INTERFACENAME sclr_intf, POLARITY ACTIVE_HIGH";
  attribute x_interface_info of Q : signal is "xilinx.com:signal:data:1.0 q_intf DATA";
  attribute x_interface_parameter of Q : signal is "XIL_INTERFACENAME q_intf, LAYERED_METADATA undef";
begin
U0: entity work.c_counter_binary_0_c_counter_binary_v12_0_12
     port map (
      CE => '1',
      CLK => CLK,
      L(9 downto 0) => B"0000000000",
      LOAD => '0',
      Q(9 downto 0) => Q(9 downto 0),
      SCLR => SCLR,
      SINIT => '0',
      SSET => '0',
      THRESH0 => NLW_U0_THRESH0_UNCONNECTED,
      UP => '1'
    );
end STRUCTURE;
